hellosamblack/lidar-roomscanner/references/datasheets/NUCLEO-H563ZI/schematic/mb1404-bdp/readme.txt

******************************************************************************
* @file    readme.txt
* @author  MCD Application Team
* @version 1.1
* @date    04-August-2023  
* @brief   MB1404 board design files package
******************************************************************************
* COPYRIGHT(c) 2023 STMicroelectronics
*
* The Open Platform License Agreement (“Agreement”) is a binding legal contract
* between you ("You") and STMicroelectronics International N.V. (“ST”), a
* company incorporated under the laws of the Netherlands acting for the purpose
* of this Agreement through its Swiss branch 39, Chemin du Champ des Filles,
* 1228 Plan-les-Ouates, Geneva, Switzerland.
*
* By using the enclosed reference designs, schematics, PC board layouts, and
* documentation, in hardcopy or CAD tool file format (collectively, the
* “Reference Material”), You are agreeing to be bound by the terms and
* conditions of this Agreement. Do not use the Reference Material until You
* have read and agreed to this Agreement terms and conditions. The use of
* the Reference Material automatically implies the acceptance of the Agreement
* terms and conditions.
*
* The complete Open Platform License Agreement can be found on www.st.com/opla.
******************************************************************************

========================
* 1.0 - 22-February-2023
========================
    + First official release.
 
========================
* 1.1 - 04-August-2023
========================
    +  Schematics template updated + minor component changes (C59, C66, C69, C74, C79, C80, C81, C83, C84: YAGEO reference replaced by KEMET reference).

******************* (C) COPYRIGHT 2023 STMicroelectronics *****END OF FILE
