hellosamblack/lidar-roomscanner/references/datasheets/NUCLEO-IKS4A1/LSM6DSV16XTR/an5763-lsm6dsv16x-6axis-imu-with-embedded-sensor-fusion-ai-qvar-for-highend-applications-stmicroelectronics.md

# AN5763 Application Note Summary

* **Document ID**: AN5763 (Rev 4)
* **Title**: LSM6DSV16X: 6-axis IMU with embedded sensor fusion, AI, Qvar for high-end applications application note
* **PDF Files**: [an5763...pdf](file:///home/sam/git/personal/lidar-roomscanner/references/datasheets/NUCLEO-IKS4A1/LSM6DSV16XTR/an5763-lsm6dsv16x-6axis-imu-with-embedded-sensor-fusion-ai-qvar-for-highend-applications-stmicroelectronics.pdf) / [applicationNote.pdf](file:///home/sam/git/personal/lidar-roomscanner/references/datasheets/NUCLEO-IKS4A1/LSM6DSV16XTR/applicationNote.pdf) (See also `an.txt`)
* **Page Count**: 147 pages
* **Manufacturer**: STMicroelectronics

---

## Executive Summary
**AN5763** is the primary, comprehensive application note for the LSM6DSV16X 6-axis IMU. It details full operating modes, digital filtering pipelines (LPF1, LPF2, HPF), FIFO operation & compression, Embedded Sensor Fusion (SFI), interrupt routing, temperature compensation, Qvar sensing, and $\text{I}^2\text{C}$/SPI/$\text{I3C}$ serial interface protocol handling.

---

## Major Technical Topics & Chapters

### 1. Operating Modes & Power Management
* **Power Modes**: Low-power mode 1/2/3 and High-Performance mode.
* **Independent ODR Selection**: Accelerometer and Gyroscope can run at independent output data rates (1.875 Hz to 7.68 kHz).
* **Dual Channel Mode**: Allows splitting stream data for UI (User Interface) and EIS/OIS (Electronic / Optical Image Stabilization).

### 2. Digital Filtering & Processing Pipeline
```
[ Raw Sensor ] ---> [ LPF1 ] ---> [ LPF2 / HPF ] ---> [ FIFO / Output Registers ]
                                       |
                                       +---> [ Embedded Sensor Fusion (SFI) ]
```
* **Accelerometer Filters**: LPF1 cutoff frequency, LPF2 second-order low-pass filter, HPF high-pass filter for motion detection.
* **Gyroscope Filters**: LPF1 and HPF configuration for bias removal.

### 3. FIFO Buffer (4.5 KB) & Compression
* Modes: Bypass, FIFO mode, Continuous (Stream), Continuous-to-FIFO, Bypass-to-Continuous.
* Batching ODRs for Accel, Gyro, SFI, Temperature, FSM, MLC, and external sensors.
* **FIFO Compression**: Embedded lossless compression algorithm (2x or 3x compression factor) to maximize FIFO autonomy buffer time.

### 4. Embedded Sensor Fusion (SFLP)
* Computes the **game rotation vector** (attitude quaternion), gravity vector and gyroscope bias directly inside the LSM6DSV16X hardware core.
* **6-axis ONLY — accelerometer + gyroscope. There is no 9-axis / eCompass / geomagnetic mode on this part.**
  AN5763 §6.5: *"based on the accelerometer and gyroscope data processing"*. Datasheet §2.8 and p.1:
  *"a sensor fusion low-power (SFLP) algorithm able to provide a 6-axis (accelerometer + gyroscope) game
  rotation vector"*; the `SFLP_GAME_EN` bit is documented as *"sensor fusion algorithm for 6-axis
  accelerometer + gyroscope"*. "Game rotation vector" is Android's term for precisely the mag-free one.
* The **sensor hub (mode 2) is an I²C master**, not a fusion input: it attaches an external magnetometer or
  barometer so their data can reach the FIFO / FSM / MLC. It does **not** feed SFLP. Magnetometer fusion on
  this project is therefore host-side (`roomscan.sensors` `YawFusion`) by necessity, not by choice.
* Heading drift spec (datasheet Table 1): **0.5°/5 min** static, **0.7°/5 min** low-dynamic,
  **5.9°/5 min** high-dynamic. Pitch/roll 1.5°/0.5°/1.6° respectively.
* Outperformed host software fusion in power efficiency (~0.65 mA total IMU + fusion current).

> ⚠ **This file is a derived summary, not ST text.** An earlier revision of this section claimed SFLP
> *"Operates in 6-axis mode or 9-axis eCompass mode (Accel + Gyro + External Magnetometer via Sensor Hub /
> I3C)"* — that sentence appears **nowhere** in the source PDF and sent a 2026-07-30 session looking for an
> on-chip 9-axis mode that does not exist. Corrected against `pdftotext` output of the PDF beside it.
> **Verify any load-bearing claim in these `.md` summaries against the PDF before acting on it.**

### 5. Interrupt & Event Generation
* **Free-Fall Detection**: Triggers when acceleration along all 3 axes drops below configurable threshold.
* **Wake-Up & Activity/Inactivity**: Dynamic sleep-to-wake switching.
* **6D / 4D Orientation**: Detects portrait/landscape tilt position changes.
* **Single-Tap / Double-Tap**: Advanced tap gesture recognition.

---

## Recommended Initialization Code Sequence

```c
// 1. Soft Reset
write_reg(CTRL3, 0x01); // SW_RESET = 1
delay_ms(10);

// 2. Enable Block Data Update & Auto-Increment
write_reg(CTRL3, 0x44); // BDU = 1, IF_INC = 1

// 3. Configure Accelerometer: High-Performance Mode @ 120 Hz, FS = +/-4g
write_reg(CTRL1, 0x05 | (0x02 << 2)); // ODR_XL = 120 Hz, FS_XL = +/-4g

// 4. Configure Gyroscope: High-Performance Mode @ 120 Hz, FS = +/-2000 dps
write_reg(CTRL2, 0x05 | (0x03 << 2)); // ODR_G = 120 Hz, FS_G = +/-2000 dps

// 5. Enable Timestamp Counter
write_reg(CTRL10, 0x20); // TIMESTAMP_EN = 1
```

---

## LLM Routing Guide: When to Consult This File
Consult `AN5763` when:
* Implementing the complete hardware driver, FIFO reader, or interrupt handler for LSM6DSV16X.
* Configuring Embedded Sensor Fusion (SFI) vector outputs.
* Setting up FIFO batching and 2x/3x data compression.
* Tuning digital filters (LPF1, LPF2, HPF) for noise reduction or motion detection.
