hellosamblack/lidar-roomscanner/references/datasheets/NUCLEO-IKS4A1/LIS2MDL/dt0104-exploiting-the-magnetometer-as-a-virtual-gyroscope-at-low-and-ultrahigh-spin-rates-stmicroelectronics.md

# DT0104 Design Tip Summary

* **Document ID**: DT0104
* **Title**: Exploiting the magnetometer as a virtual gyroscope at low and ultra-high spin rates
* **Author**: Andrea Vitali
* **PDF File**: [dt0104...pdf](file:///home/sam/git/personal/lidar-roomscanner/references/datasheets/NUCLEO-IKS4A1/LIS2MDL/dt0104-exploiting-the-magnetometer-as-a-virtual-gyroscope-at-low-and-ultrahigh-spin-rates-stmicroelectronics.pdf)
* **Page Count**: 5 pages
* **Manufacturer**: STMicroelectronics

---

## Executive Summary
**DT0104** explains how to use a 3-axis magnetometer (e.g. LIS2MDL) as a **virtual gyroscope** to estimate angular velocity ($\omega$). This techniques allows measuring high spin rates beyond the dynamic full-scale range of physical gyroscopes (> 4000 dps) or saving power by disabling physical gyroscopes in low-rate monitoring applications.

---

## Technical Principle & Mathematical Derivation

### Principle
When a magnetometer rotates in a stable ambient magnetic field $\vec{B}_{earth}$, the magnetic vector measured in the sensor frame rotates at rate $\vec{\omega}$.
The time derivative of the magnetic field vector in the sensor body frame is:
$$\frac{d\vec{B}}{dt} = -\vec{\omega} \times \vec{B}$$

### Angular Rate Calculation
From the cross-product relation, the component of angular velocity perpendicular to the magnetic field vector is given by:
$$\vec{\omega}_{\perp} = \frac{\vec{B} \times \frac{d\vec{B}}{dt}}{\|\vec{B}\|^2}$$

### Spin Rate Estimation (Rotation Phase Derivative)
For 2D planar rotation around the Z axis:
$$\theta(t) = \arctan2(B_y(t), B_x(t))$$
$$\omega_z(t) = \frac{d\theta(t)}{dt} = \frac{B_x \cdot \frac{dB_y}{dt} - B_y \cdot \frac{dB_x}{dt}}{B_x^2 + B_y^2}$$

---

## Key Benefits & Operating Ranges

| Capability | Physical Gyroscope | Virtual Gyroscope (LIS2MDL) |
| :--- | :--- | :--- |
| **Max Rate Range** | $\pm 2000$ to $\pm 4000$ dps (saturation) | **> 10,000 dps** (limited only by sampling ODR & bandwidth) |
| **Power Consumption** | High (~0.5 - 1.2 mA) | **Ultralow (~50 - 200 $\mu\text{A}$)** |
| **Bias Drift** | Temperature / time gyro bias drift | **Zero long-term drift** (tied to Earth's magnetic field) |

---

## LLM Routing Guide: When to Consult This File
Consult `DT0104` when:
* Measuring extremely high spin rates (e.g., spinning lidar turrets, projectiles, drill heads, high-RPM motors).
* Reducing power consumption by replacing or augmenting physical gyroscopes with magnetometer angular rate tracking.
* Estimating rotational velocity when gyro sensors saturate or fail.
