hellosamblack/lidar-roomscanner/references/datasheets/NUCLEO-IKS4A1/LSM6DSV16XTR/an5882-lsm6dsv16x-finite-state-machine-stmicroelectronics.md

# AN5882 Application Note Summary

* **Document ID**: AN5882 (Rev 3)
* **Title**: LSM6DSV16X: finite state machine application note
* **PDF File**: [an5882...pdf](file:///home/sam/git/personal/lidar-roomscanner/references/datasheets/NUCLEO-IKS4A1/LSM6DSV16XTR/an5882-lsm6dsv16x-finite-state-machine-stmicroelectronics.md)
* **Page Count**: 68 pages
* **Manufacturer**: STMicroelectronics

---

## Executive Summary
**AN5882** describes the programming, architecture, and instruction set of the **Finite State Machines (FSM)** integrated into the LSM6DSV16X. Up to **8 independent state machines** can be programmed to detect specific gesture sequences, motion patterns, or orientation changes directly in hardware.

---

## FSM Architecture & Instruction Set

```
[ Motion Sensor Stream ] ---> [ Signal Conditioning ] ---> [ FSM Program Memory ] ---> [ FSM Interrupt / Status ]
                                (Filters & Selection)      (Commands: CHK, JMP...)
```

### 1. Key Components
* **Signal Conditioning Block**: Applies high-pass / low-pass filtering, magnitude calculation ($\sqrt{X^2+Y^2+Z^2}$), vector inner products, and thresholds.
* **FSM Block**: 8 independent execution engines reading FSM program memory.
* **Long Counter**: 16-bit timing counter shared between state machines to evaluate duration constraints.

### 2. Main FSM Commands / Opcodes
* `NOP`: No operation.
* `CHK`: Check condition (evaluates threshold, axis sign, or time counter).
* `JMP`: Jump to instruction address if condition evaluates true.
* `SET`: Set flag or output state.
* `RESET`: Reset timer counter or state.
* `OUT`: Generate FSM interrupt signal and output state code to status register.

---

## Programming & Memory Loading
1. Create state machine definition using ST FSM Tool / MEMS Studio.
2. Generate FSM byte code program.
3. Write FSM configuration bytes into LSM6DSV16X Embedded Advanced Features pages (`EMB_FUNC_EN_A`, `FSM_ENABLE`).

---

## LLM Routing Guide: When to Consult This File
Consult `AN5882` when:
* Developing custom hardware-accelerated motion gesture algorithms (e.g., glance, wrist tilt, shake, rotation detection).
* Writing software drivers to load FSM binary code into LSM6DSV16X memory.
* Handling FSM interrupt status flags (`FSM_STATUS_A / B`).
