hellosamblack/lidar-roomscanner/references/datasheets/NUCLEO-IKS4A1/LSM6DSV16XTR/dt0060-exploiting-the-gyroscope-to-update-tilt-measurement-and-ecompass-stmicroelectronics.md

# DT0060 Design Tip Summary

* **Document ID**: DT0060
* **Title**: Exploiting the gyroscope to update tilt measurement and eCompass
* **Author**: Andrea Vitali
* **PDF File**: [dt0060...pdf](file:///home/sam/git/personal/lidar-roomscanner/references/datasheets/NUCLEO-IKS4A1/LSM6DSV16XTR/dt0060-exploiting-the-gyroscope-to-update-tilt-measurement-and-ecompass-stmicroelectronics.pdf)
* **Page Count**: 7 pages
* **Manufacturer**: STMicroelectronics

---

## Executive Summary
**DT0060** details how to integrate gyroscope angular rate measurements ($\omega_x, \omega_y, \omega_z$) into tilt and eCompass estimation loops to prevent external dynamic accelerations (such as linear motion, vehicle turning, or vibrations) from corrupting tilt and heading measurements.

---

## Dynamic Fusion Principle & Complementary Filtering

### Problem Statement
Accelerometer-only tilt computation (DT0058) assumes that the measured vector is pure Earth gravity ($1g$). Under linear acceleration (e.g. robot accelerating forward), accelerometer measurements combine gravity and linear acceleration ($A = g + a_{linear}$), creating severe tilt calculation errors.

### Gyroscope Integration Solution
1. **Short-Term High Frequency Update**: Integrate gyroscope angular velocity ($\vec{\omega}$) to update orientation quaternions or DCM (Direction Cosine Matrix) smoothly over time $\Delta t$.
2. **Long-Term Drift Correction**: Apply complementary filter or Kalman filter gain to fuse accelerometer gravity vector and magnetometer heading at low rates:
$$\vec{q}_{k} = \vec{q}_{k-1} \otimes \Delta\vec{q}_{gyro} + \alpha \cdot (\vec{q}_{accel/mag} - \vec{q}_{k-1})$$

---

## LLM Routing Guide: When to Consult This File
Consult `DT0060` when:
* Implementing 6-axis / 9-axis complementary filters or Extended Kalman Filters (EKF).
* Resolving orientation jitter or tilt errors caused by mechanical vibration or robot movement.
