hellosamblack/lidar-roomscanner/calibration/flatfield/2026-08-04/analysis_20260804_metrics.csv

file | raw_frames | depth_accuracy_global_error_mm | depth_plane_rms_mm | depth_zone_std_median_mm | depth_zone_std_p95_mm | depth_valid_pct | refl_fpn_pct | refl_holdout_after_pct | refl_temporal_cv_pct | deproj_xy_p95_mm | deproj_xy_edge_p95_mm
4msExpPrecision55inchFlatField.bin | 1271 | -4.109130859375 | 2.0163314069502403 | 0.7660982689572351 | 0.8609254001545432 | 100.0 | 6.596441922477059 | 1.4478581717208816 | 0.6963480464052492 | 31.431350536653053 | 43.82652857957803
8msExpPrecision55inchFlatField.bin | 1173 | -4.242919921875 | 2.0286684740914684 | 0.5268087677416203 | 0.601913518048294 | 100.0 | 6.679974894812315 | 1.4549387802397868 | 0.43813580350810893 | 31.420344466770047 | 43.81545564114227
8msExpPrecision60hzEnv55inchFlatField.bin | 1196 | -4.02734375 | 2.0329517637275347 | 0.5115222347405917 | 0.5867092585629184 | 100.0 | 6.662128279519313 | 1.4468677948119013 | 0.4390378373825098 | 31.420387760098127 | 43.81260219086063
Reg16msExpAmbient55inchFlatField.bin | 1227 | -7.1934814453125 | 2.5540982429090264 | 0.43187292052123105 | 0.5053695860848644 | 100.0 | 3.7271666114927395 | 1.7651792741803083 | 0.13134724100037556 | 31.3895410448603 | 43.94168717777747
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
