hellosamblack/lidar-roomscanner/calibration/flatfield/2026-08-04/analysis_20260804_flatfield_maps.png

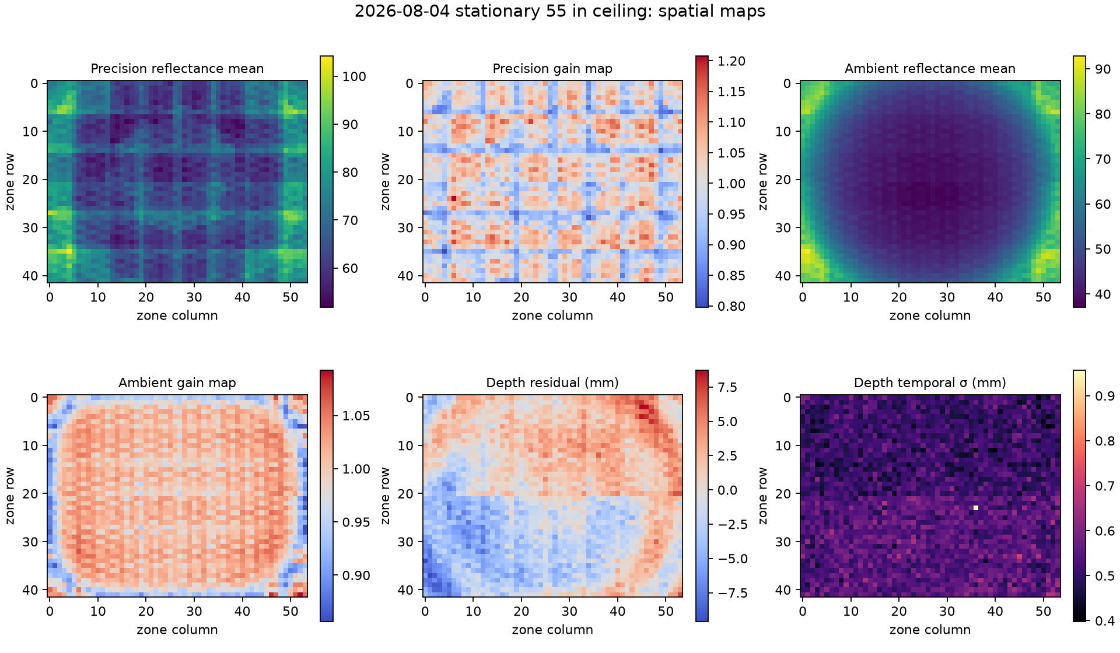
calibration/flatfield/2026-08-04/analysis_20260804_flatfield_maps.png
