hellosamblack/lidar-roomscanner/calibration/flatfield/2026-08-04/ffpan_20260804_ambientRegular8msFFpan.png

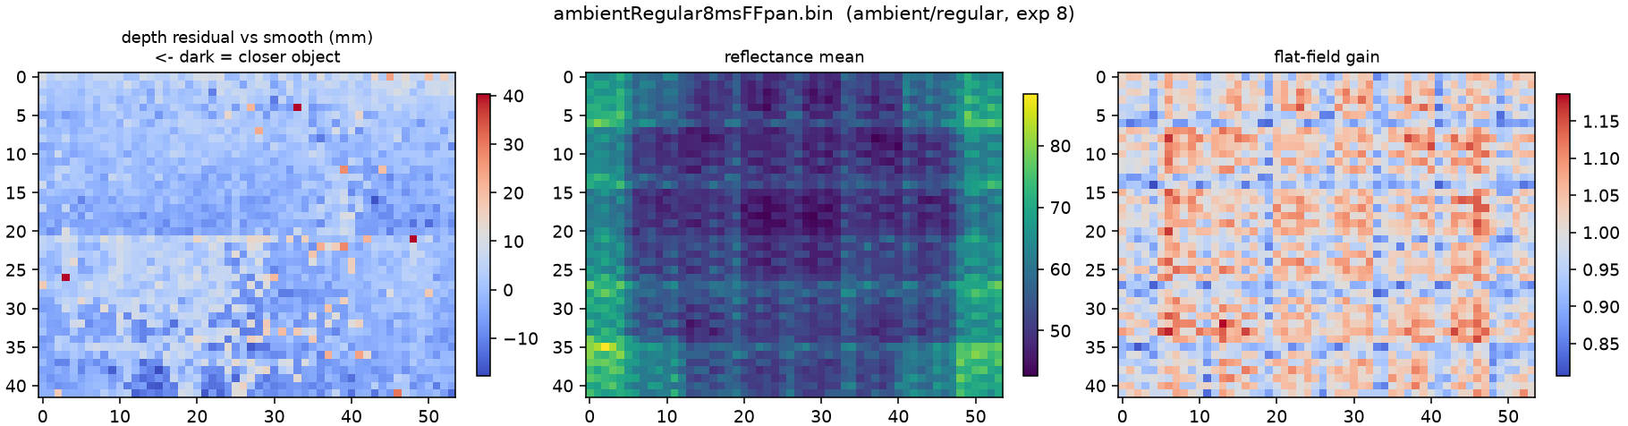
calibration/flatfield/2026-08-04/ffpan_20260804_ambientRegular8msFFpan.png
