hellosamblack/lidar-roomscanner/references/kicad/roomscanner-stack/roomscanner-stack.kicad_sch

## KiCad design references/kicad/roomscanner-stack/roomscanner-stack.kicad_sch (2026-07-10)

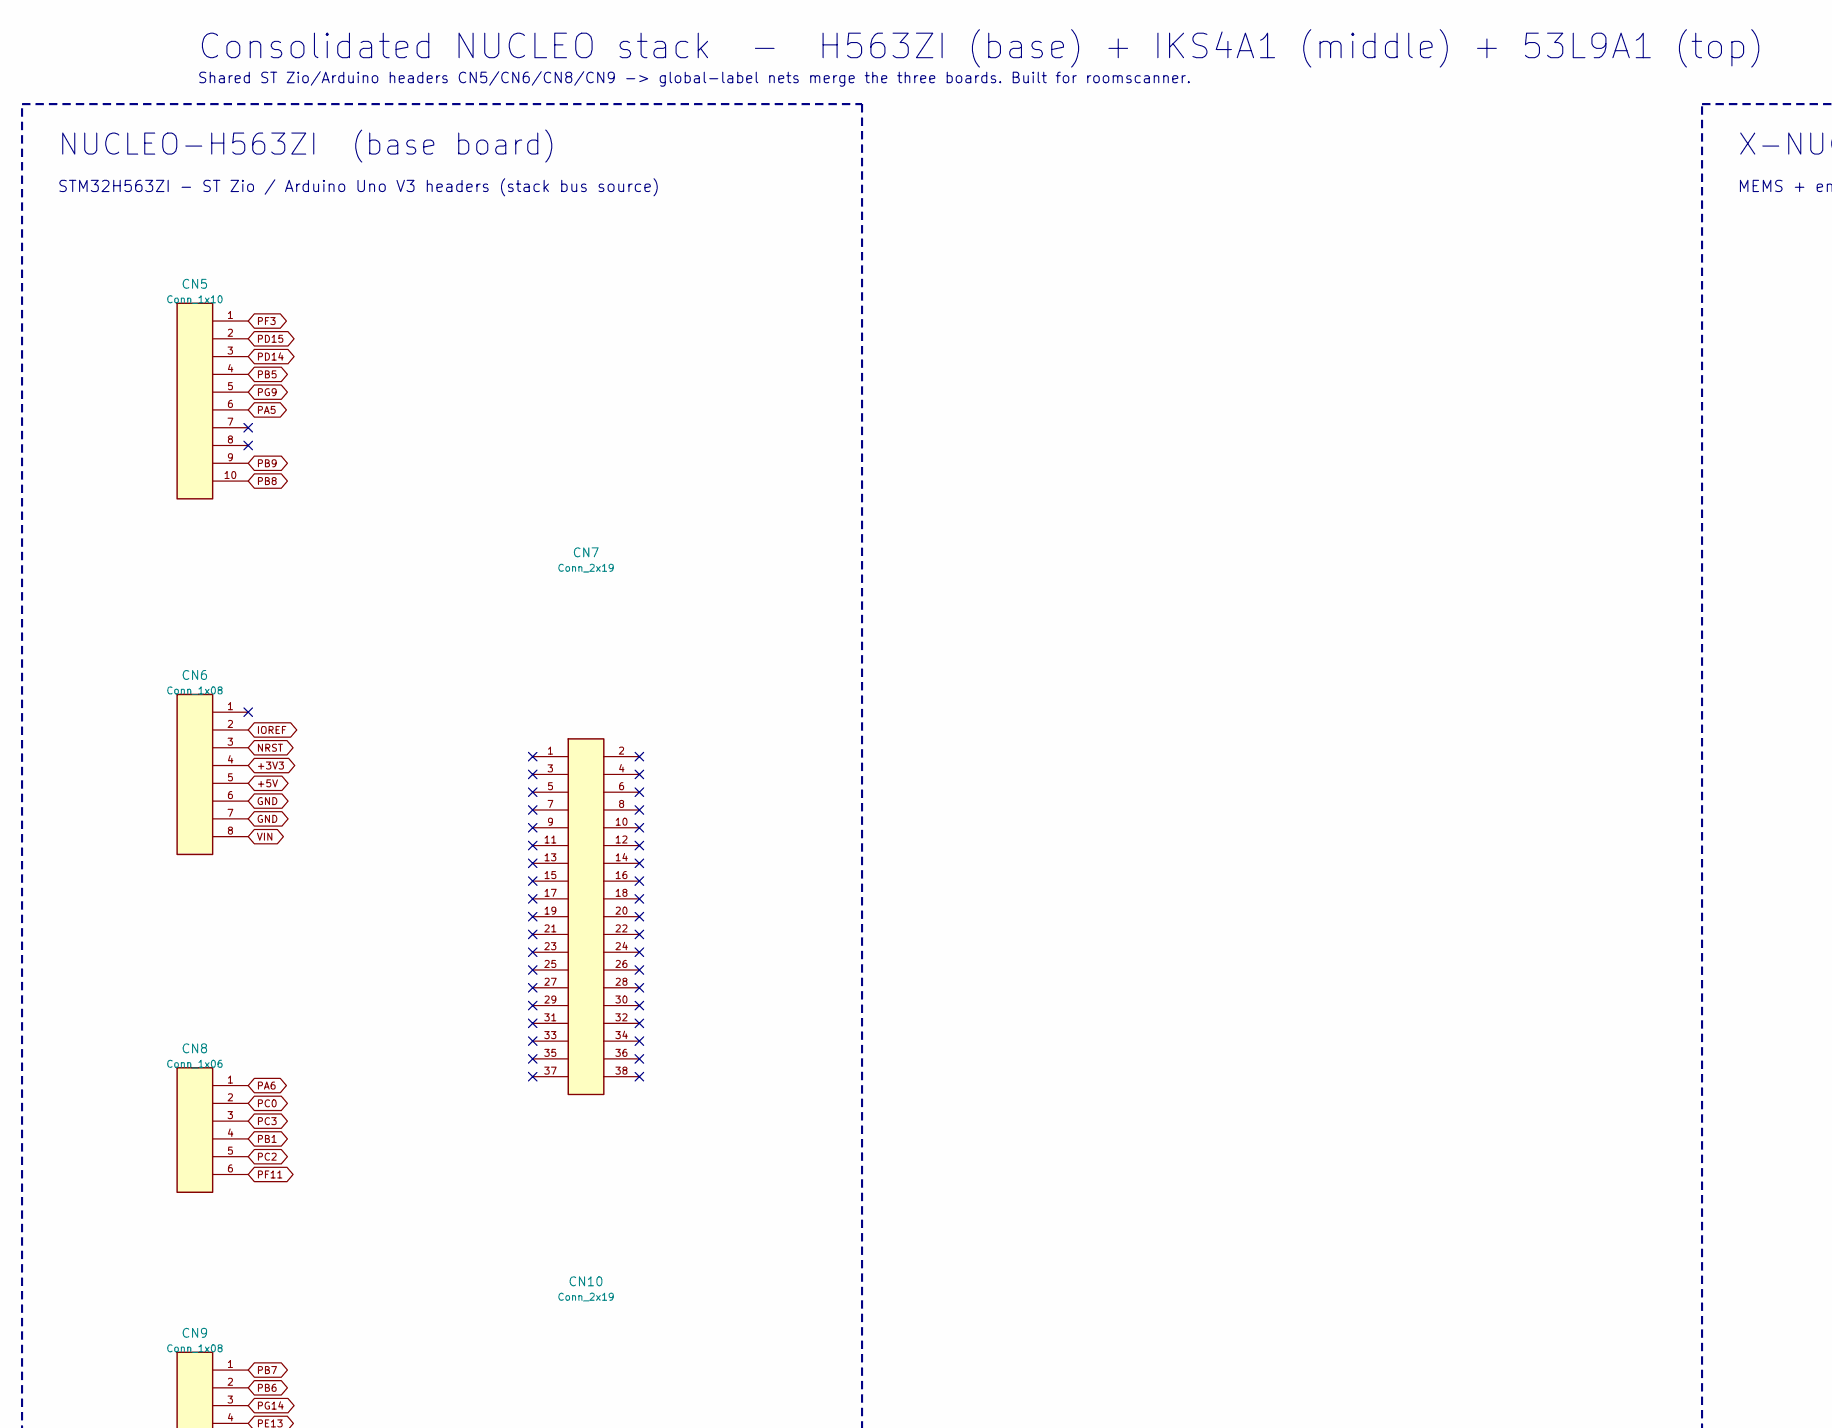
[picture p10: schematic roomscanner-stack.kicad_sch, part in row 1, column 1]

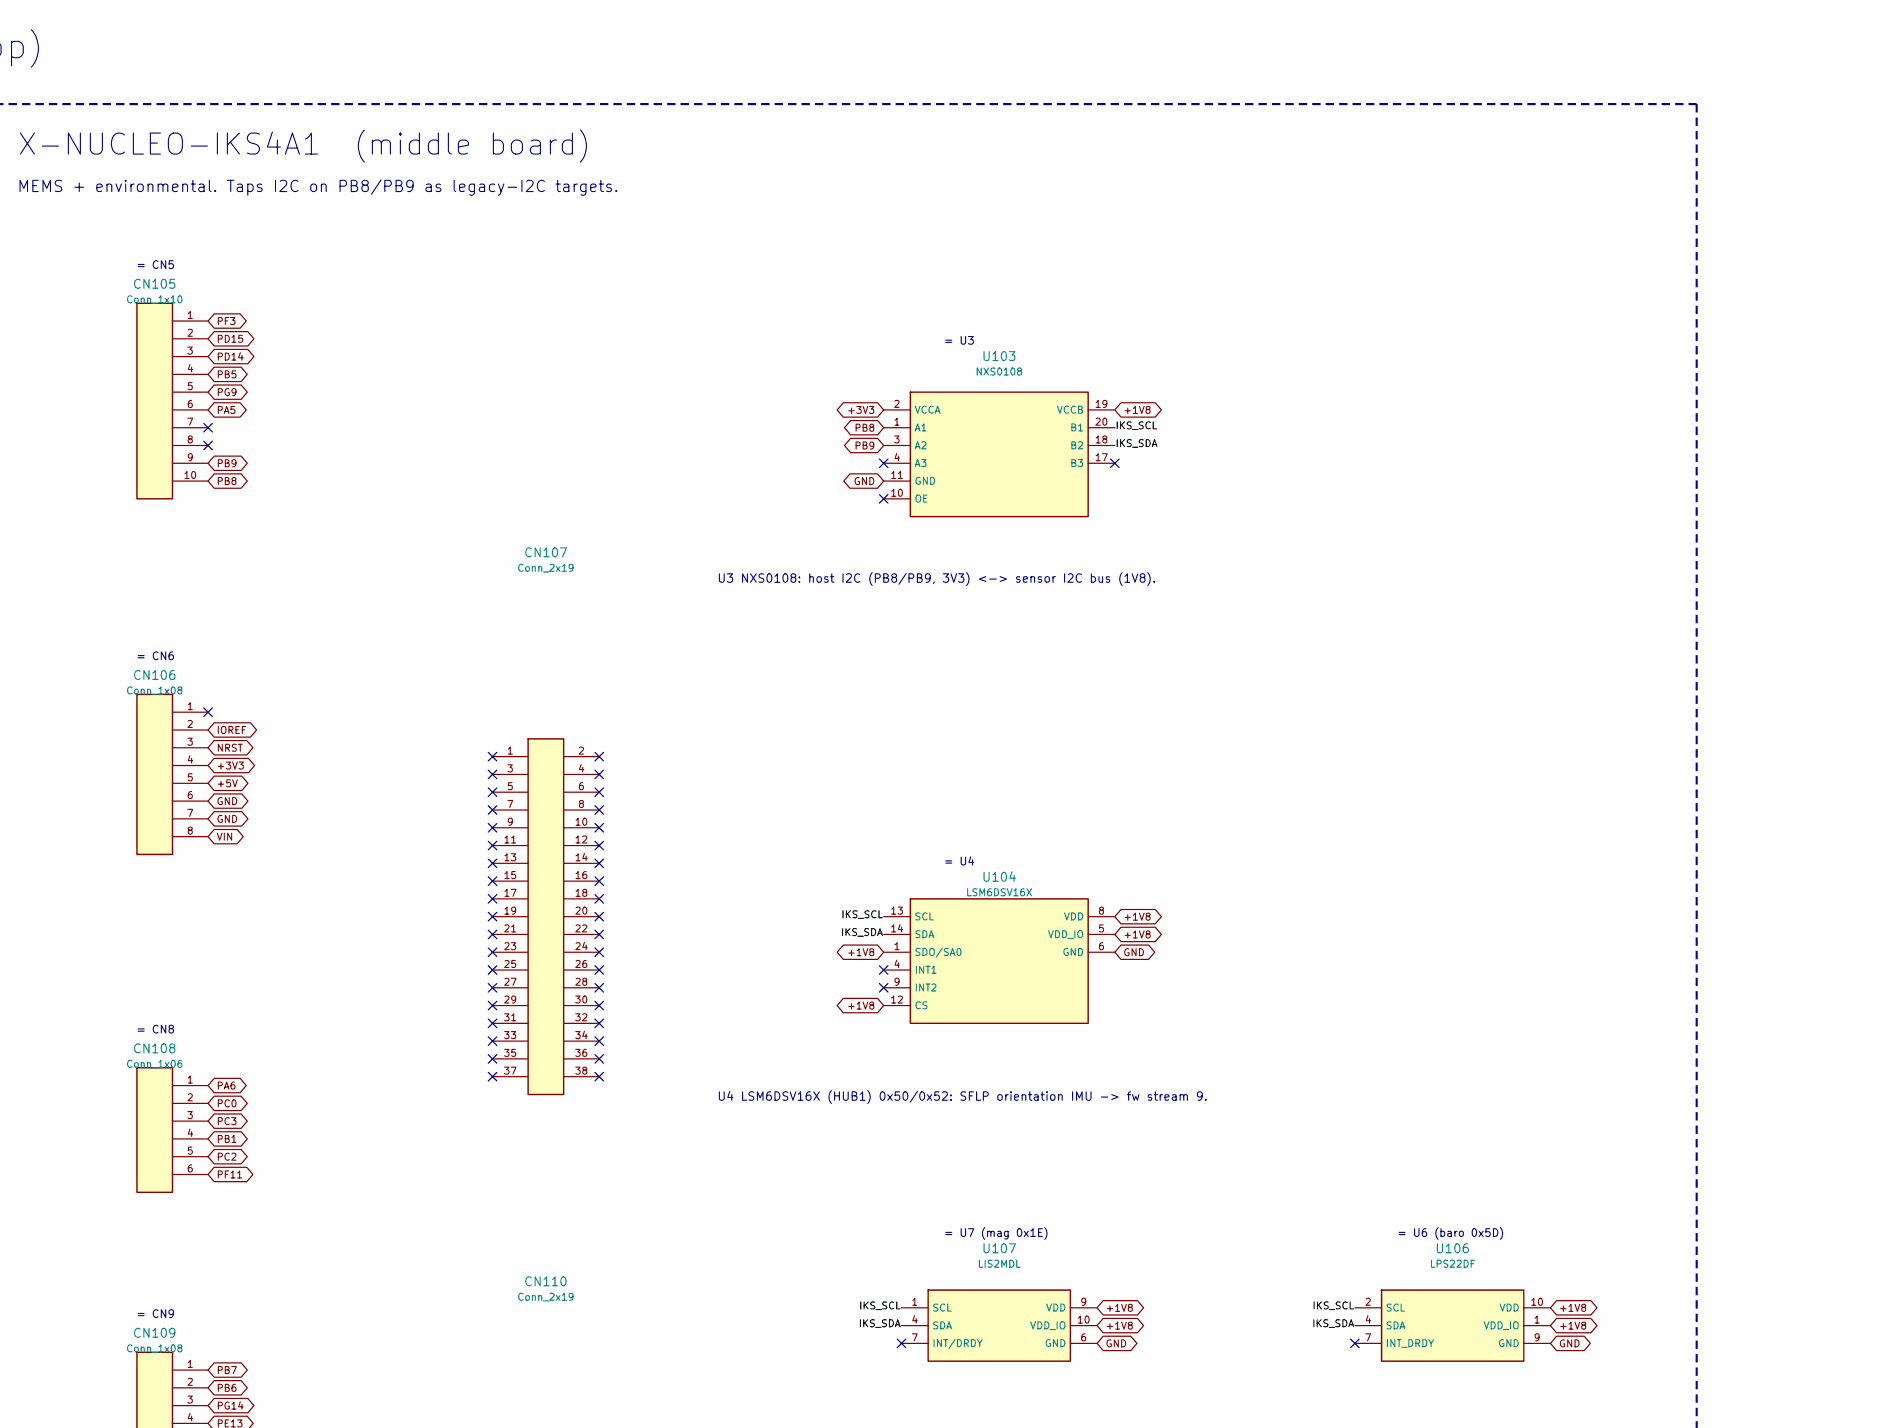
[picture p11: schematic roomscanner-stack.kicad_sch, part in row 1, column 2]

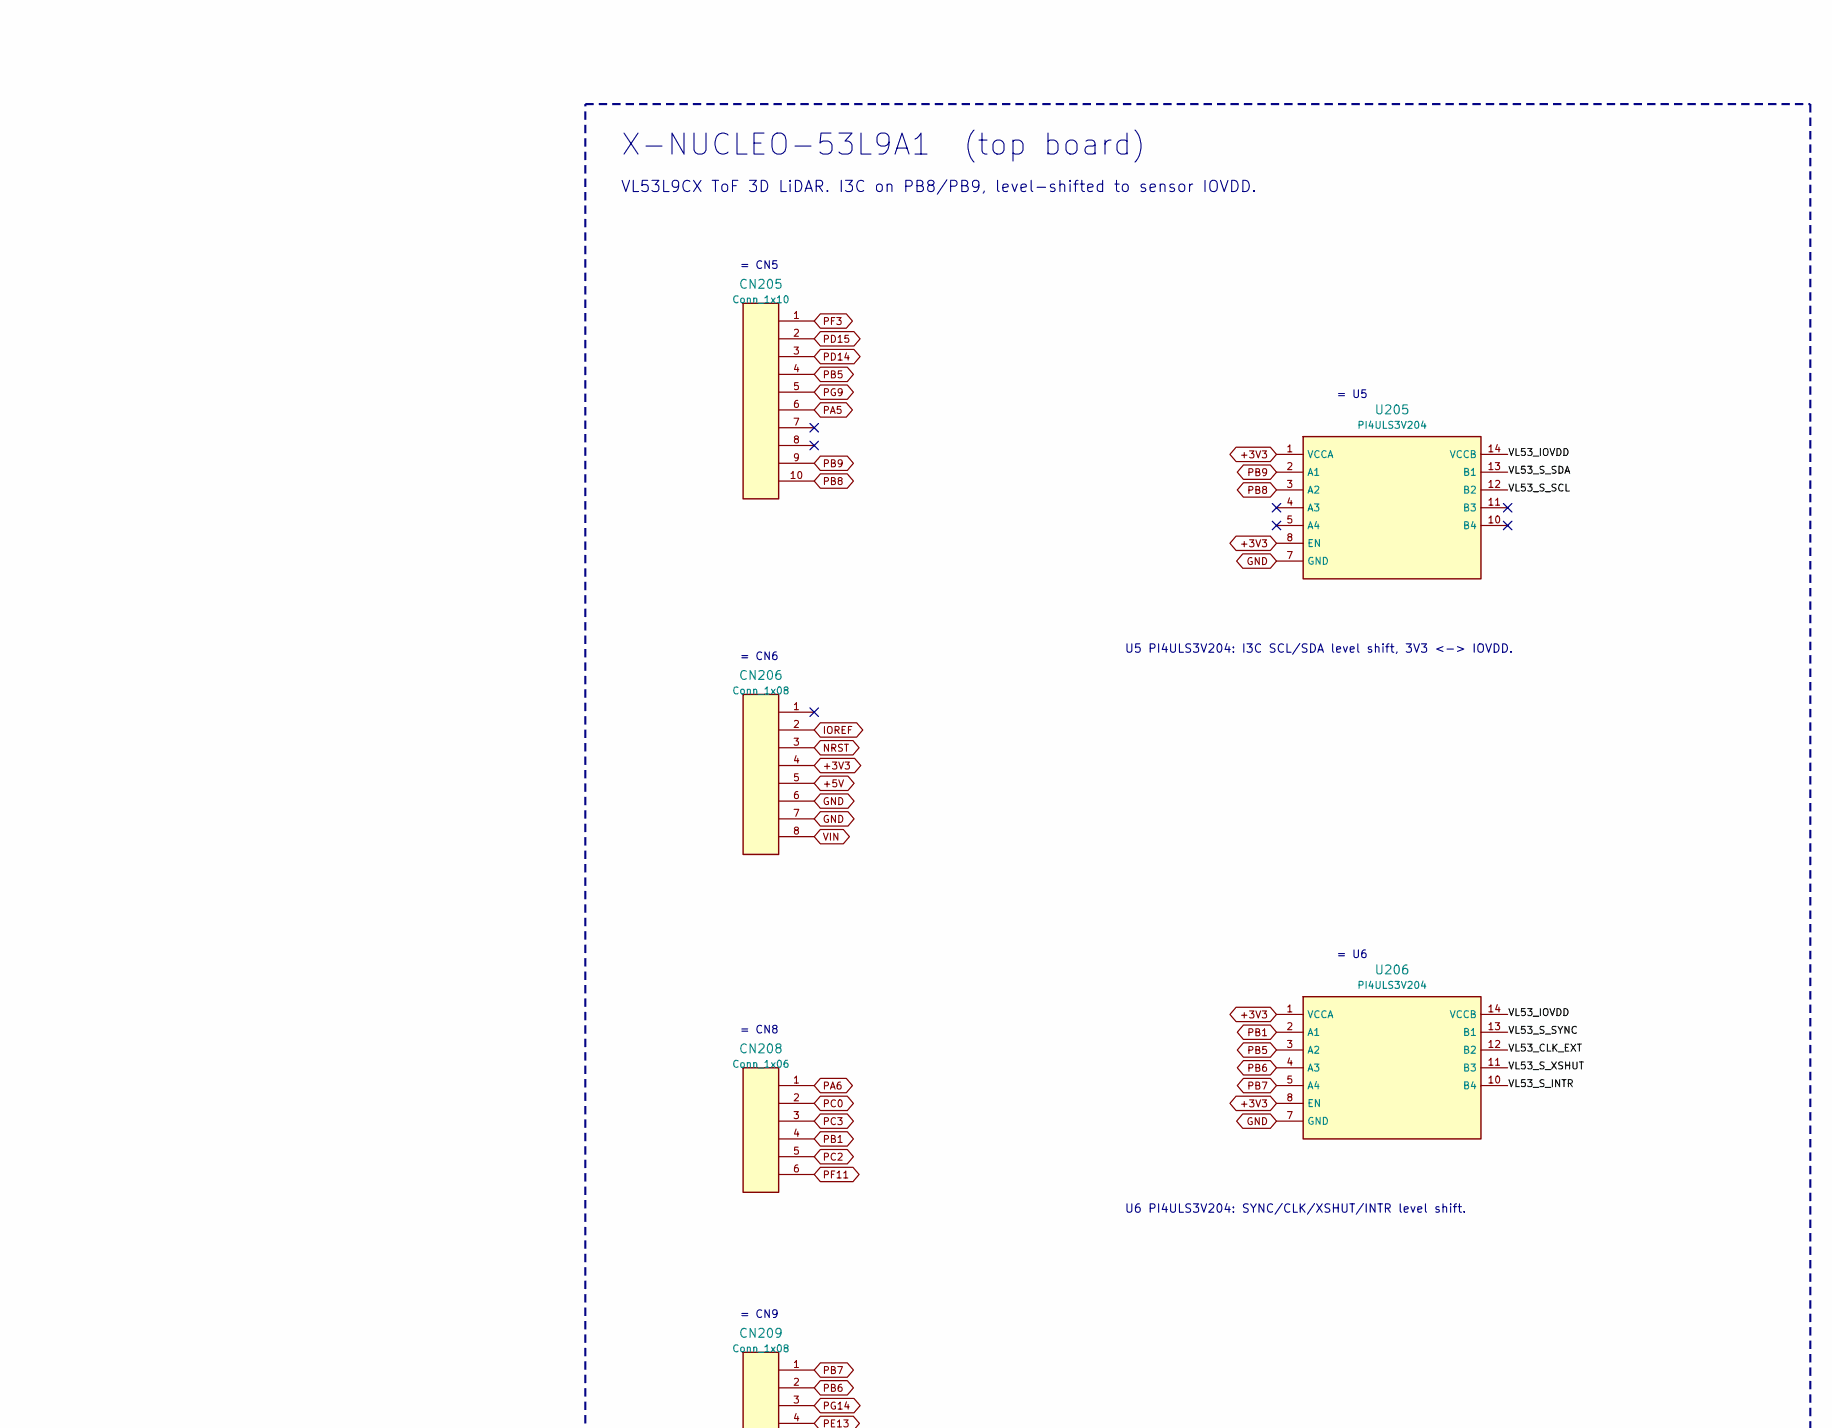
[picture p12: schematic roomscanner-stack.kicad_sch, part in row 1, column 3]

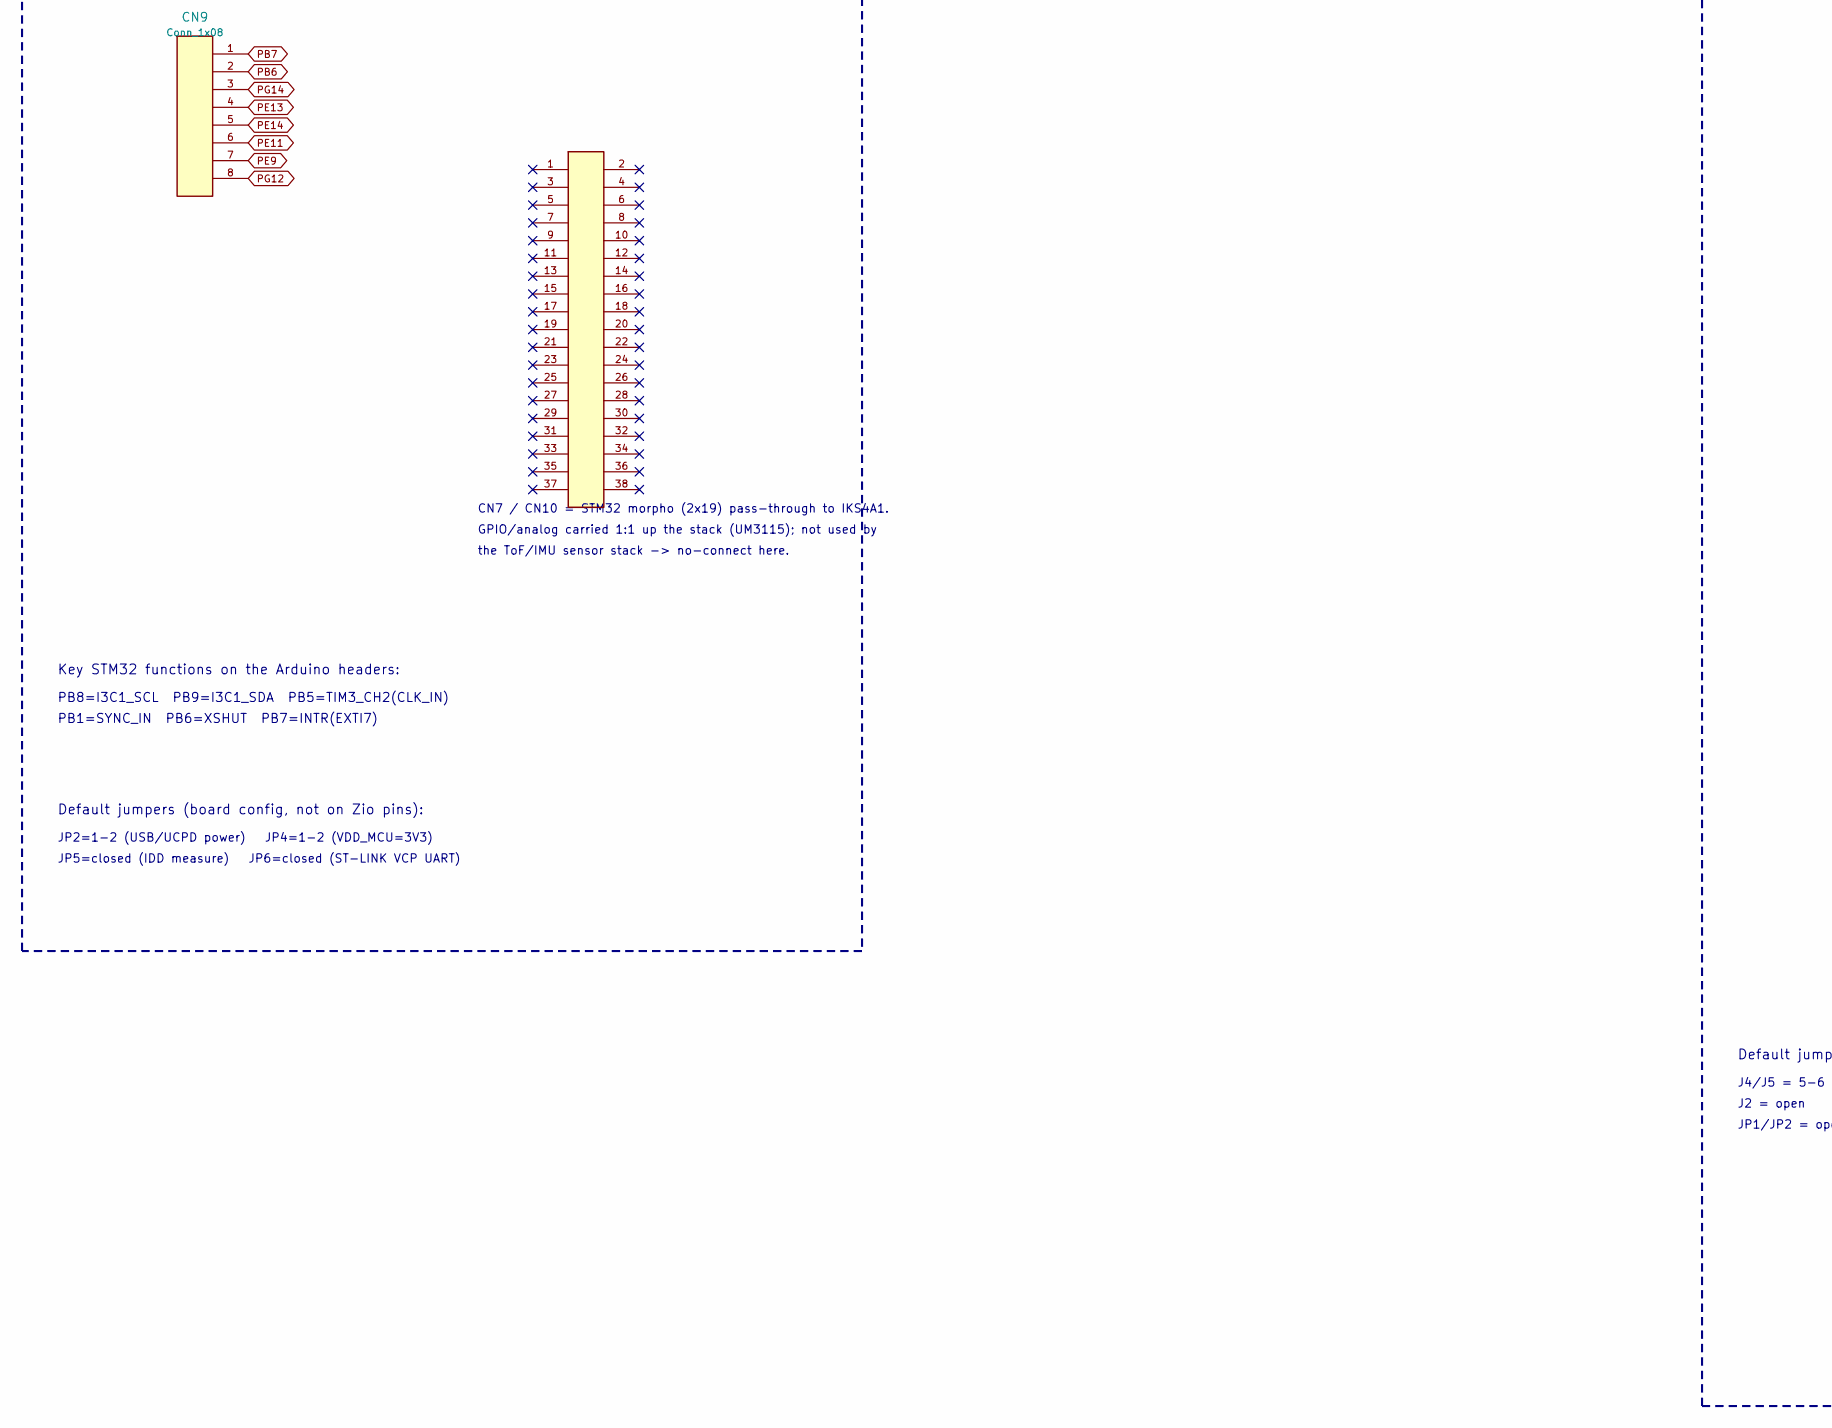
[picture p13: schematic roomscanner-stack.kicad_sch, part in row 2, column 1]

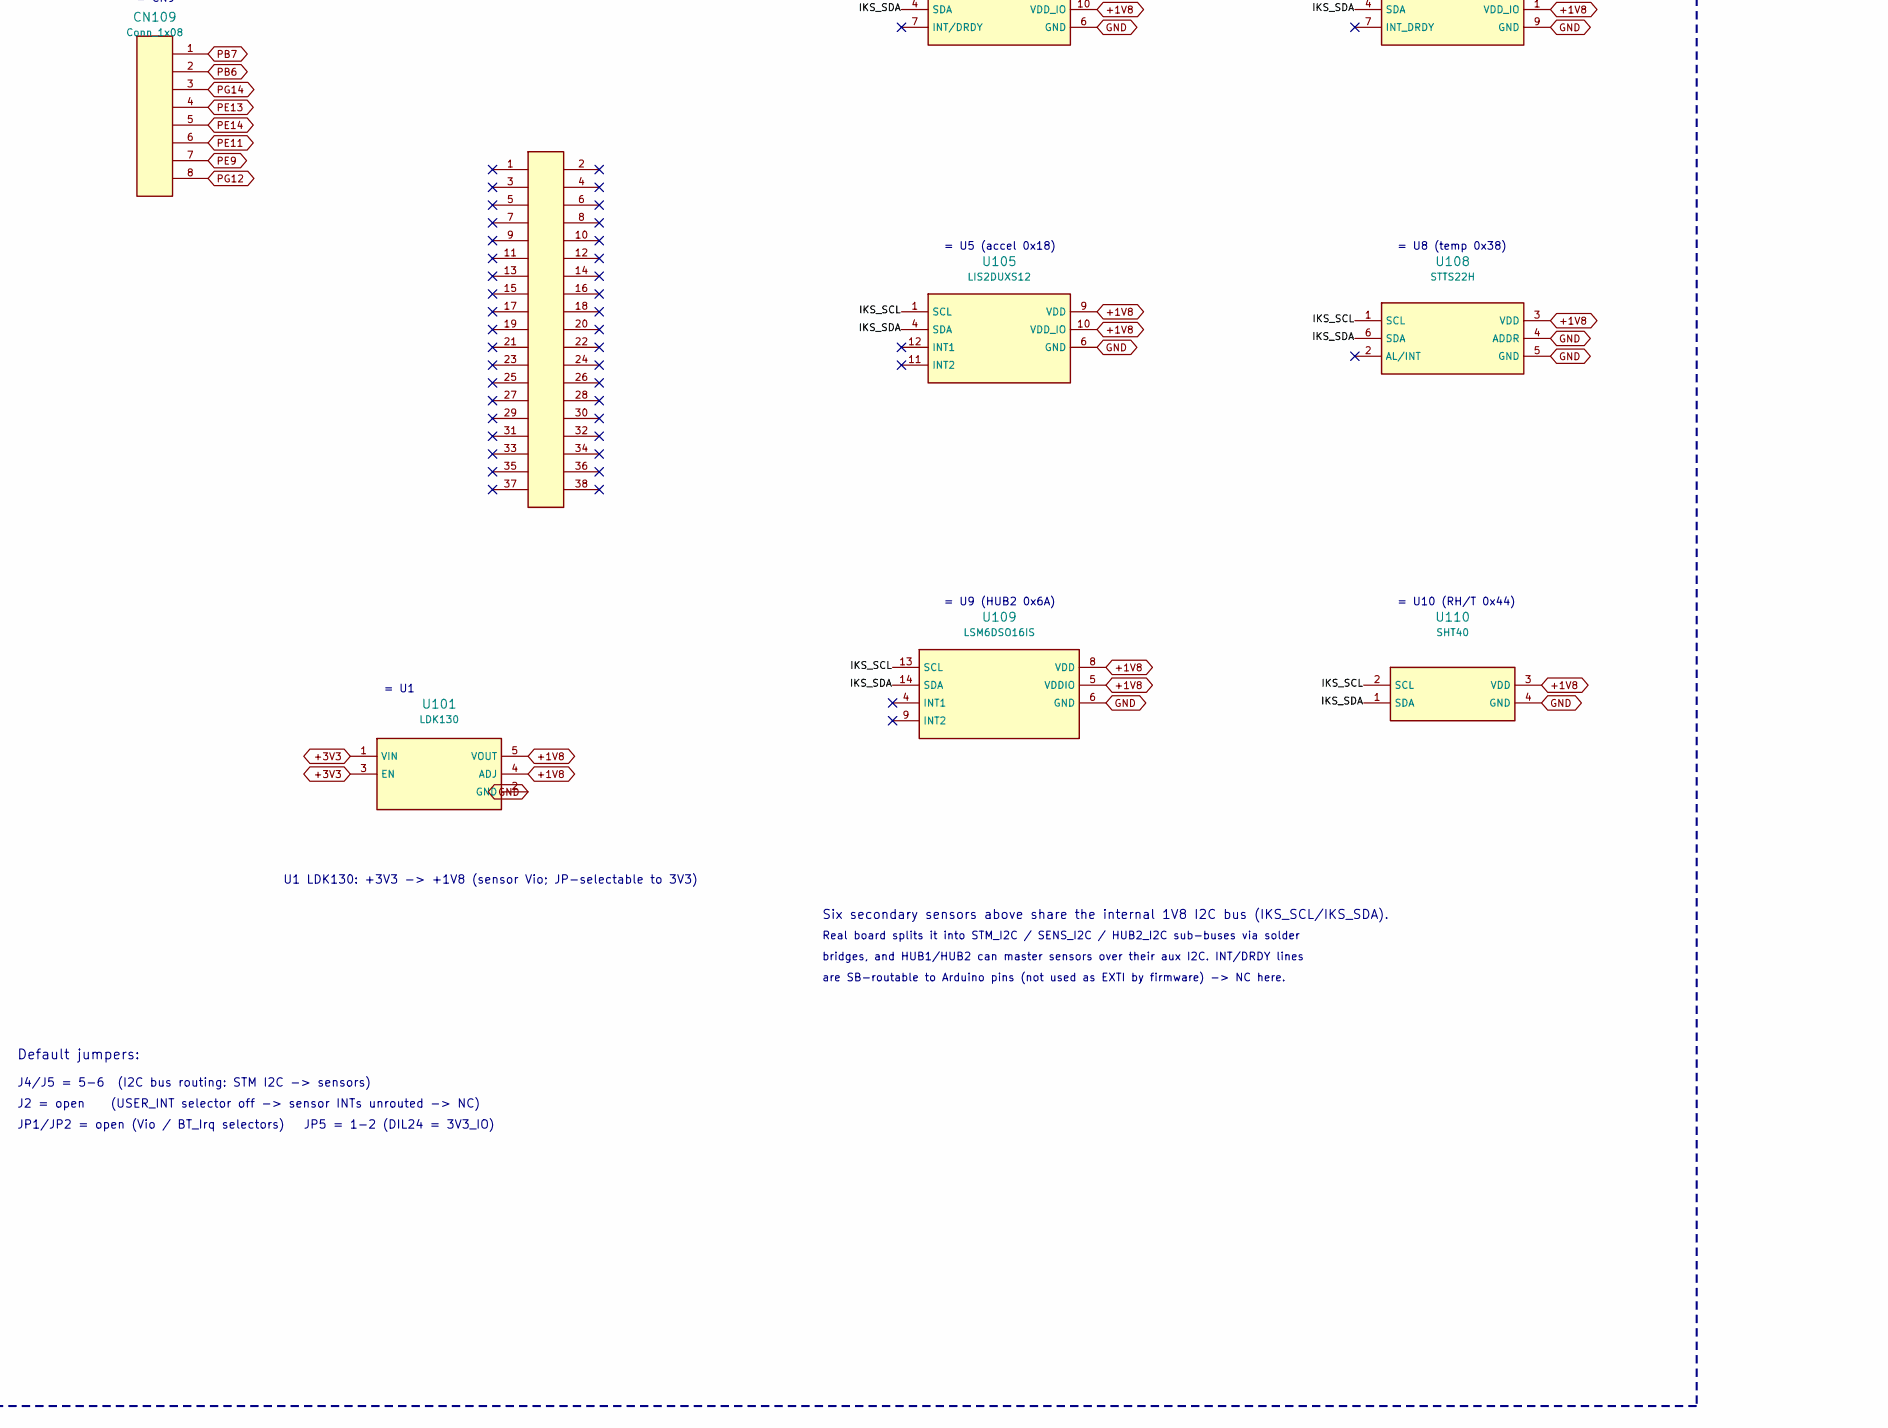
[picture p14: schematic roomscanner-stack.kicad_sch, part in row 2, column 2]

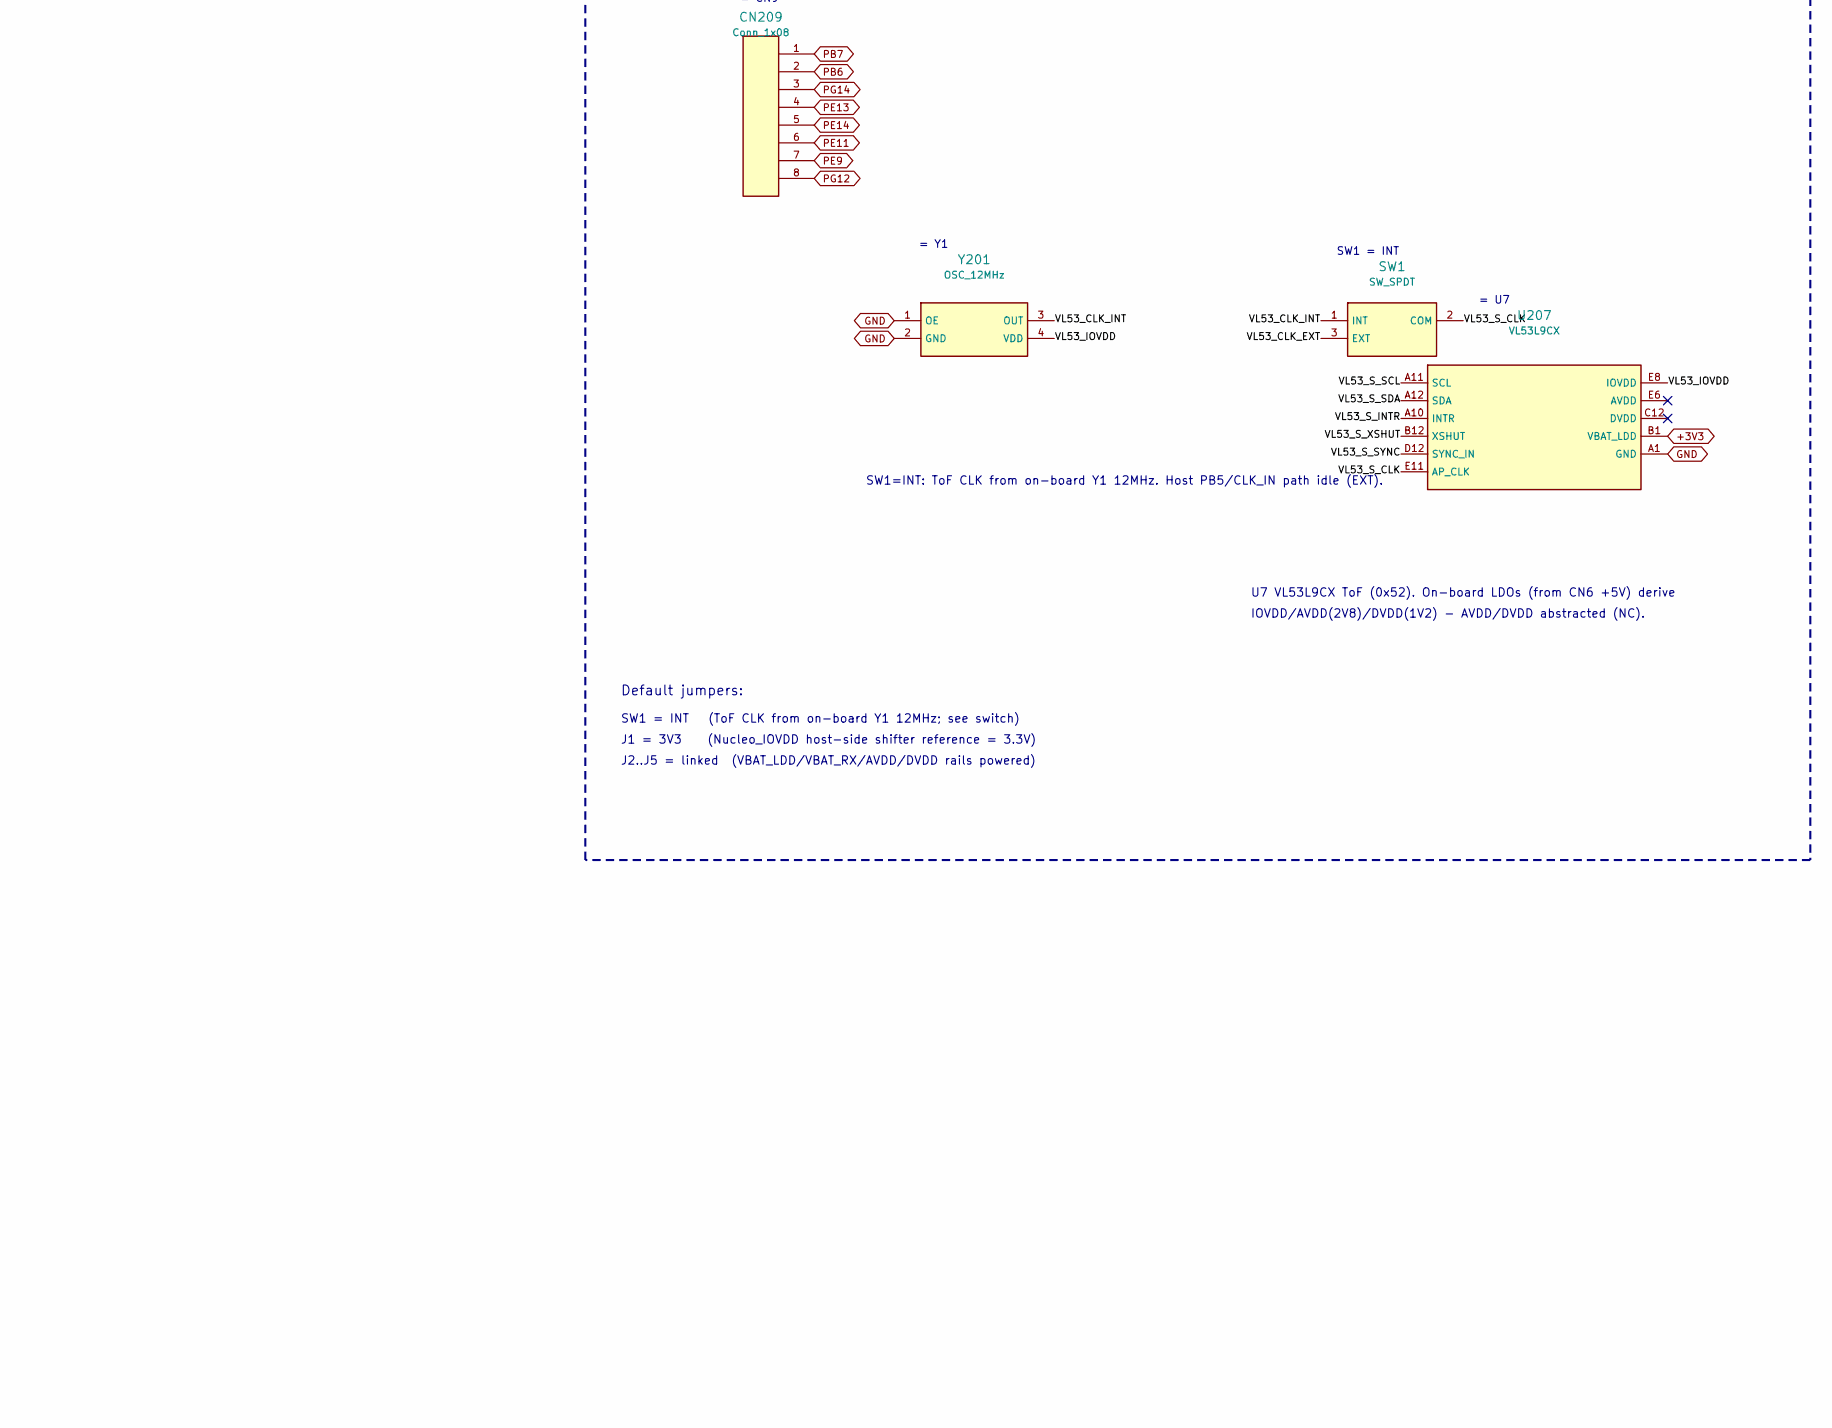
[picture p15: schematic roomscanner-stack.kicad_sch, part in row 2, column 3]

Parts:
CN5, CN105, CN205: Conn_1x10
CN6, CN9, CN106, CN109, CN206, CN209: Conn_1x08
CN7, CN10, CN107, CN110: Conn_2x19
CN8, CN108, CN208: Conn_1x06
SW1: SW_SPDT
U101: LDK130
U103: NXS0108
U104: LSM6DSV16X
U105: LIS2DUXS12
U106: LPS22DF
U107: LIS2MDL
U108: STTS22H
U109: LSM6DSO16IS
U110: SHT40
U205, U206: PI4ULS3V204
U207: VL53L9CX
Y201: OSC_12MHz

Connections:
+1V8: U101.4 (ADJ), U101.5 (VOUT), U103.19 (VCCB), U104.1 (SDO/SA0), U104.5 (VDD_IO), U104.8 (VDD), U104.12 (CS), U105.9 (VDD), U105.10 (VDD_IO), U106.1 (VDD_IO), U106.10 (VDD), U107.9 (VDD), U107.10 (VDD_IO), U108.3 (VDD), U109.5 (VDDIO), U109.8 (VDD), U110.3 (VDD)
+3V3: CN6.4, CN106.4, CN206.4, U101.1 (VIN), U101.3 (EN), U103.2 (VCCA), U205.1 (VCCA), U205.8 (EN), U206.1 (VCCA), U206.8 (EN), U207.B1 (VBAT_LDD)
+5V: CN6.5, CN106.5, CN206.5
GND: CN6.6, CN6.7, CN106.6, CN106.7, CN206.6, CN206.7, U101.2 (GND), U103.11 (GND), U104.6 (GND), U105.6 (GND), U106.9 (GND), U107.6 (GND), U108.4 (ADDR), U108.5 (GND), U109.6 (GND), U110.4 (GND), U205.7 (GND), U206.7 (GND), U207.A1 (GND), Y201.1 (OE), Y201.2 (GND)
IKS_SCL: U103.20 (B1), U104.13 (SCL), U105.1 (SCL), U106.2 (SCL), U107.1 (SCL), U108.1 (SCL), U109.13 (SCL), U110.2 (SCL)
IKS_SDA: U103.18 (B2), U104.14 (SDA), U105.4 (SDA), U106.4 (SDA), U107.4 (SDA), U108.6 (SDA), U109.14 (SDA), U110.1 (SDA)
IOREF: CN6.2, CN106.2, CN206.2
NRST: CN6.3, CN106.3, CN206.3
PA5: CN5.6, CN105.6, CN205.6
PA6: CN8.1, CN108.1, CN208.1
PB1: CN8.4, CN108.4, CN208.4, U206.2 (A1)
PB5: CN5.4, CN105.4, CN205.4, U206.3 (A2)
PB6: CN9.2, CN109.2, CN209.2, U206.4 (A3)
PB7: CN9.1, CN109.1, CN209.1, U206.5 (A4)
PB8: CN5.10, CN105.10, CN205.10, U103.1 (A1), U205.3 (A2)
PB9: CN5.9, CN105.9, CN205.9, U103.3 (A2), U205.2 (A1)
PC0: CN8.2, CN108.2, CN208.2
PC2: CN8.5, CN108.5, CN208.5
PC3: CN8.3, CN108.3, CN208.3
PD14: CN5.3, CN105.3, CN205.3
PD15: CN5.2, CN105.2, CN205.2
PE9: CN9.7, CN109.7, CN209.7
PE11: CN9.6, CN109.6, CN209.6
PE13: CN9.4, CN109.4, CN209.4
PE14: CN9.5, CN109.5, CN209.5
PF3: CN5.1, CN105.1, CN205.1
PF11: CN8.6, CN108.6, CN208.6
PG9: CN5.5, CN105.5, CN205.5
PG12: CN9.8, CN109.8, CN209.8
PG14: CN9.3, CN109.3, CN209.3
VIN: CN6.8, CN106.8, CN206.8
VL53_CLK_EXT: SW1.3 (EXT), U206.12 (B2)
VL53_CLK_INT: SW1.1 (INT), Y201.3 (OUT)
VL53_IOVDD: U205.14 (VCCB), U206.14 (VCCB), U207.E8 (IOVDD), Y201.4 (VDD)
VL53_S_CLK: SW1.2 (COM), U207.E11 (AP_CLK)
VL53_S_INTR: U206.10 (B4), U207.A10 (INTR)
VL53_S_SCL: U205.12 (B2), U207.A11 (SCL)
VL53_S_SDA: U205.13 (B1), U207.A12 (SDA)
VL53_S_SYNC: U206.13 (B1), U207.D12 (SYNC_IN)
VL53_S_XSHUT: U206.11 (B3), U207.B12 (XSHUT)

Notes on the sheet:
Consolidated NUCLEO stack - H563ZI (base) + IKS4A1 (middle) + 53L9A1 (top)
Shared ST Zio/Arduino headers CN5/CN6/CN8/CN9 -> global-label nets merge the three boards. Built for roomscanner.
NUCLEO-H563ZI (base board)
STM32H563ZI - ST Zio / Arduino Uno V3 headers (stack bus source)
CN7 / CN10 = STM32 morpho (2x19) pass-through to IKS4A1.
GPIO/analog carried 1:1 up the stack (UM3115); not used by
the ToF/IMU sensor stack -> no-connect here.
Key STM32 functions on the Arduino headers:
PB8=I3C1_SCL PB9=I3C1_SDA PB5=TIM3_CH2(CLK_IN)
PB1=SYNC_IN PB6=XSHUT PB7=INTR(EXTI7)
Default jumpers (board config, not on Zio pins):
JP2=1-2 (USB/UCPD power) JP4=1-2 (VDD_MCU=3V3)
JP5=closed (IDD measure) JP6=closed (ST-LINK VCP UART)
X-NUCLEO-IKS4A1 (middle board)
MEMS + environmental. Taps I2C on PB8/PB9 as legacy-I2C targets.
= CN5
= CN6
= CN8
= CN9
= U1
U1 LDK130: +3V3 -> +1V8 (sensor Vio; JP-selectable to 3V3)
= U3
U3 NXS0108: host I2C (PB8/PB9, 3V3) <-> sensor I2C bus (1V8).
= U4
U4 LSM6DSV16X (HUB1) 0x50/0x52: SFLP orientation IMU -> fw stream 9.
= U7 (mag 0x1E)
= U6 (baro 0x5D)
= U5 (accel 0x18)
= U8 (temp 0x38)
= U9 (HUB2 0x6A)
= U10 (RH/T 0x44)
Six secondary sensors above share the internal 1V8 I2C bus (IKS_SCL/IKS_SDA).
Real board splits it into STM_I2C / SENS_I2C / HUB2_I2C sub-buses via solder
bridges, and HUB1/HUB2 can master sensors over their aux I2C. INT/DRDY lines
are SB-routable to Arduino pins (not used as EXTI by firmware) -> NC here.
Default jumpers:
J4/J5 = 5-6 (I2C bus routing: STM I2C -> sensors)
J2 = open (USER_INT selector off -> sensor INTs unrouted -> NC)
JP1/JP2 = open (Vio / BT_Irq selectors) JP5 = 1-2 (DIL24 = 3V3_IO)
X-NUCLEO-53L9A1 (top board)
VL53L9CX ToF 3D LiDAR. I3C on PB8/PB9, level-shifted to sensor IOVDD.
= U5
U5 PI4ULS3V204: I3C SCL/SDA level shift, 3V3 <-> IOVDD.
= U6
U6 PI4ULS3V204: SYNC/CLK/XSHUT/INTR level shift.
= Y1
SW1 = INT
SW1=INT: ToF CLK from on-board Y1 12MHz. Host PB5/CLK_IN path idle (EXT).
= U7
U7 VL53L9CX ToF (0x52). On-board LDOs (from CN6 +5V) derive
IOVDD/AVDD(2V8)/DVDD(1V2) - AVDD/DVDD abstracted (NC).
SW1 = INT (ToF CLK from on-board Y1 12MHz; see switch)
J1 = 3V3 (Nucleo_IOVDD host-side shifter reference = 3.3V)
J2..J5 = linked (VBAT_LDD/VBAT_RX/AVDD/DVDD rails powered)
