hellosamblack/lidar-roomscanner/host/src/roomscan/web.py

"""Web-based real-time instrument. One reader thread (the neutral
`reader._run_reader`, shared with the desktop panel) feeds a latest-wins slot; a SINGLE asyncio
broadcast task fans every transformed frame out to all connected WebSocket
clients. This replaces the old per-connection `slot.get_nowait()` loop, whose
competing gets stole frames from one another when two tabs were open (§5.3).

The wire is multiplexed on one `/ws` socket: binary messages (point cloud, IR
image) carry a leading little-endian uint32 tag; JSON text messages carry a
`type` discriminator (metrics/event/log/cmd/state). See the design spec
docs/superpowers/specs/completed/2026-07-15-web-phase1-core-instrument-design.md §6.

Pure, socket-free helpers (classify_bus_line / select_colors /
pack_point_cloud / pack_ir_image / build_metrics_message) are factored out at
module level so the protocol/coloring logic is unit-testable without a server.
"""
from __future__ import annotations

import asyncio
import base64
import itertools
import json
import logging
import math
import os
import queue
import re
import shlex
import shutil
import socket
import struct
import subprocess
import sys
import tempfile
import threading
import time
from collections import deque
import webbrowser
import zlib
from contextlib import asynccontextmanager, suppress
from dataclasses import asdict, dataclass, field, replace
from pathlib import Path

import numpy as np
import uvicorn
from fastapi import FastAPI, WebSocket, WebSocketDisconnect
from fastapi.responses import FileResponse, JSONResponse, RedirectResponse, Response
from fastapi.staticfiles import StaticFiles
from starlette.websockets import WebSocketState

from .colors import gray, turbo
from . import commstatus
from .config import ViewerConfig
from .control import (
    CommandClient,
    CommandDispatcher,
    _manual_params_to_wire,
    _POWER_MODE_TO_WIRE,
    _RANGING_MODE_TO_WIRE,
)
from .decoder import StreamDecoder
from .deproject import Deprojector
from .ir_image import ir_range, reflectance_to_rgb
from .logbus import LogBus
from .magcal import MagCalibration
from .magsweep import (
    MagSweepSession,
    assign_cells,
    build_report as build_magcal_report,
    calibrated_directions,
    calibrated_norms,
    motion_state,
    view_calibration,
)
from .metrics import MetricsRegistry, MetricsSnapshot, ResourceSampler
from .flatfield import FlatFieldSet
from .pipeline import TransformStage
from .reader import _Pacer, _run_reader, follow_camera_target
from .protocol import (
    HEADER_SIZE,
    MAGIC,
    CommandCode,
    FrameHeader,
    FrameType,
    ProtocolError,
    RangingConfigAck,
    ResultCode,
    StandbyLevel,
    StreamId,
)
from .sensors import (
    AXIS_CONVENTION,
    SensorState,
    YawFusion,
    absolute_heading,
    boresight_view_deg,
    display_rotation,
    graft_yaw,
    gravity_body_from_imu_raw,
    ir_gravity_residual_deg,
    ir_gravity_rot,
    quat_mul,
    quat_pitch_alt_deg,
    quat_pitch_deg,
    quat_roll_alt_deg,
    quat_roll_deg,
    quat_to_matrix,
    quat_yaw_alt_deg,
    quat_yaw_deg,
    tilt_from_down_deg,
    triad_roll_deg,
    wrap180,
)
from . import profiles
from . import thumbs as thumbs_mod
from .motion import coherence
from .sources import FileSource, Recorder, SerialSource, UdpSource, get_best_source
from zeroconf import ServiceInfo, Zeroconf
from .thin_render import (
    DEFAULT_JPEG_QUALITY, THIN_HEIGHT, THIN_WIDTH, ThinCamera,
    ThinRenderer, ThinRenderUnavailable, extract_ir_full, extract_ir_grid, image_scene,
    jpeg_available, points_scene, unpack_mesh_scene, warm_jpeg_import,
)
from .slam.config import DetailedSlamPreset, preferred_device
from .slam.detailed import (build_manifest, estimate_seconds, sidecar_paths,
                            sidecar_status, write_manifest_atomic)
from .slam.detailed import delete_sidecar as detailed_delete_sidecar
from .slam.detailed import rename_sidecar as detailed_rename_sidecar
from .slam.meshprep import MeshPrep
from .slam.metrics import write_tum
from .slam.frames import baro_height_m
from .slam.showcase import PostProcessWorker
from .splat import list_splats as list_splats_on_disk
from .splat import list_source_videos, slugify, splat_defaults
from .viewer import Stats, resolve_args
from .weather import FALLBACK_MSL_PA, MslPressure

log = logging.getLogger("roomscan.web")

# Binary message type tags (first 4 bytes, little-endian uint32).
TAG_POINT_CLOUD = 1
TAG_IR_IMAGE = 2
TAG_MESH = 3               # SLAM reconstruction mesh (web Phase 4)
TAG_SURFACE = 4            # surface-interpolated point cloud (grid + triangles)
TAG_MAGPOSE = 5            # 30 Hz magcal pose/field sample (magcal 3D feedback)

# Broadcast cadences (seconds). Point cloud paces the outer loop at a 30 Hz
# target (owner, 2026-07-16) -- the cap must sit at or above the source rate so
# it never down-samples the stream; a slower source just re-sends the last frame.
# IR and metrics run on their own slower elapsed-time gates off the same task.
POINT_INTERVAL = 1.0 / 30.0
IR_INTERVAL = 1.0 / 15.0
METRICS_INTERVAL = 1.0 / 4.0
# `/ws-thin` render cadence (#194). Deliberately far slower than the point
# cloud: each tick is a full server-side 3D render (~27 ms) plus a 460 KB
# uncompressed frame, so 10 fps is ~4.6 MB/s per client on the wireless uplink.
THIN_INTERVAL = 1.0 / 10.0
THIN_TELEMETRY_INTERVAL = 0.5
# `thin_hello` negotiation clamps (#197) -- deliberately generous but bounded:
# a client that never sends `thin_hello` is unaffected (`ThinFlow` defaults
# reproduce THIN_INTERVAL / THIN_WIDTH / THIN_HEIGHT exactly).
THIN_HELLO_FPS_MIN = 1
# The fps ceiling is COUPLED to format (#197 review finding 5): a raw
# RGB565 480x480 frame is 460 800 bytes, so even today's 10 fps default is
# ~4.6 MB/s per client (see docs/thin-client.md); 60 fps raw would be
# ~27.6 MB/s and ~160% of the SINGLE shared render thread for just one
# client, starving the other (THIN_MAX_CLIENTS=2) even before the network is
# considered. A JPEG frame at the default quality is roughly 15-25 KB, so
# 60 fps JPEG (~1-1.5 MB/s) is cheaper than 10 fps raw -- raw keeps today's
# ceiling, jpeg gets the higher one.
THIN_HELLO_FPS_MAX_RAW = 10
THIN_HELLO_FPS_MAX_JPEG = 60
#: square resolutions only -- a non-square request is rejected outright and
#: the flow's prior width/height are kept, rather than distorting the image.
THIN_HELLO_RESOLUTIONS = (320, 480)
THIN_HELLO_QUALITY_MIN = 40
THIN_HELLO_QUALITY_MAX = 95
DEFAULT_THIN_FPS = 1.0 / THIN_INTERVAL   # 10.0, matches today's cadence exactly
# `/ws-thin` v2 flow control (#202, CrowPanel bandwidth spec 2026-08-18). The
# server never has more than the granted credits outstanding to a v2 client and
# DROPS (never queues) at zero credit -- on the CrowPanel's ~1.5 Mbit/s link,
# pushing faster than the client drains only fills TCP buffers until pings hit
# seconds and the client's staleness timeout flaps the session. Depth 2 = one
# frame on the wire while the client works on the previous one; deeper just
# recreates the queue this exists to remove, so the clamp ceiling stays small.
THIN_CREDITS_DEFAULT = 2
THIN_CREDITS_MIN = 1
THIN_CREDITS_MAX = 8
#: floor for a client-advertised `max_frame_bytes` -- below this even a
#: quality-40 320x320 JPEG cannot reliably fit, so the request is nonsense.
THIN_MAX_FRAME_BYTES_MIN = 4096
# `ir_cells`: how many IR zones a client says it can render. The 8x8 thumbnail the
# CrowPanel shipped with is a ~97% throwaway of a 54x42 = 2268-zone sensor, so a client
# that can hold the real thing asks for it here. Floor is the old 64 (asking for less
# than the v1 shape buys nothing); ceiling is generous headroom over 2268 for a future
# sensor, bounded so one client cannot ask the telemetry message to become enormous.
THIN_IR_CELLS_MIN = 64
THIN_IR_CELLS_MAX = 4096
#: window for the per-client `tx_fps` / `tx_bytes_per_s` telemetry figures.
THIN_TX_WINDOW_S = 5.0
# Hard cap on concurrent thin clients. Connection count is a real performance
# variable on this server (BUG-060), and a thin client costs a full render --
# far above a deflate. All clients share the one renderer (a second
# `OffscreenRenderer` aborts the process), so renders serialise: 2 clients x
# 10 fps = 20 renders/s, about 54 % of the render thread.
THIN_MAX_CLIENTS = 2
# Sensor (streams 9/10) broadcast cadence: 15 Hz is smooth for a handheld gizmo
# and well above the ~4 Hz sparkline need. History rides every message so a
# late-joining tab's sparklines are instantly full (Phase-1 late-joiner rule).
SENSOR_INTERVAL = 1.0 / 15.0
# Rolling window for the orientation jitter stats (roll/pitch/yaw/heading/overall):
# ~5s of `sensor` messages at SENSOR_INTERVAL (15 Hz) => ~75 frame-to-frame samples.
SENSOR_JITTER_WINDOW_S = 5.0
# Magnetometer-sweep (`magcal` modal) TRUTH cadence -- the JSON report: cell
# counts, verdicts, coverage, guidance. 5 Hz (raised from 4 when `cell_dirs`
# stopped riding every message: 4490 B -> 1982 B, so the raise is still ~2x
# cheaper than before). This is data that changes at HUMAN speed; the 30 Hz
# render payload rides the binary MAGPOSE channel instead (docs/web-protocol.md
# "Framing": high-rate render payloads are tagged binary, human-rate state is
# JSON). Sent ONLY to tabs that have the modal open -- `state.magcal_clients`.
MAGCAL_INTERVAL = 1.0 / 5.0
MISSING_PLANE_LOG_INTERVAL = 3.0   # debounce for missing-plane bus lines

# Recording & playback (web Phase 3).
CAPTURES_DIR = "captures"          # where Record writes + the library browses
# SLAM mode (web Phase 4).
RESULTS_DIR = "results"            # where Save writes the full-res map + trajectory
_TRAJ_TAIL_MAX = 256               # trajectory positions shipped in each `slam` message
_VALID_MODES = ("realtime", "slam")  # legacy inbound compatibility
_VALID_SOURCES = ("live", "view", "splat")
_VALID_DISPLAYS = ("point_cloud", "preview", "slam", "detailed")
_VALID_WALL_MODES = ("solid", "split")
# The playback speed segmented control maps ×0.5/×1/×2/Max onto these fps; a
# capture's own cadence is ~28 Hz, so ×1 (30 fps) plays it near-native and is
# the default. Max (0 -> interval 0) drains as fast as it decodes.
_SPEED_BASE_FPS = 30.0

_VALID_COLOR_MODES = ("depth", "reflectance", "confidence")
_VALID_IR_COLORMAPS = ("gray", "turbo")
_VALID_VIEW_COLORMAPS = ("turbo", "gray")
_VALID_SURFACE_MODES = ("grid", "spatial")
_VALID_IDLE_LEVELS = ("soft", "hard")
# View-page capture browser (§12). Sorting is applied CLIENT-side off the
# already-broadcast `captures` array -- the server persists the choice, it does
# not re-scan for it.
_VALID_BROWSER_SORTS = ("recent", "name", "size", "duration")
_VALID_BROWSER_VIEWS = ("grid", "list")
# One inbound `delete_captures` can never nominate more files than the library
# could plausibly hold; a WS peer is untrusted and this is the only destructive
# handler in the app.
_MAX_DELETE_BATCH = 200
# Real-time view modes (owner ask, 2026-07-29). Which frame the live cloud is
# shipped in -- see `view_rotation`. Real-time only; SLAM has its own camera.
_VALID_VIEW_MODES = ("world", "fpv", "mirror")

# --- camera framing per view mode (owner ask, 2026-07-30) --------------------
# All three views are described as an offset from ONE baseline: the FPV ground
# truth, i.e. a camera sitting exactly at the sensor looking down its boresight.
# All-zero offsets reproduce that camera exactly, in every mode. `distance_m`
# backs the eye off along the view axis, `height_m` lifts it, and
# `rotation_deg` swings it about the vertical axis through the aim point (which
# stays on the axis, so the subject stays framed).
#
# The modes differ only in what "the axis" is: in fpv/mirror it is the live
# boresight, because the server has already rotated the cloud into the
# boresight view frame (`view_rotation`); in world it is the fixed world
# forward. Those coincide exactly when the board is held in the reference pose,
# which is what makes the FPV baseline a common reference rather than three
# unrelated cameras. Ranges are validated on the wire AND on config load.
_CAM_DISTANCE_RANGE = (0.0, 15.0)      # metres back along the view axis
_CAM_HEIGHT_RANGE = (-5.0, 10.0)       # metres up (negative dips below)
_CAM_ROTATION_RANGE = (-180.0, 180.0)  # degrees; positive swings the eye right
# Auto-orbit is WORLD-ONLY: fpv/mirror are locked to the sensor, so there is no
# scene to circle. Azimuth only -- elevation and distance are untouched, which
# is why the client hands it to OrbitControls' own `autoRotate` rather than
# animating `rotation_deg` (that would also churn the persisted value at 30 Hz).
_ORBIT_SPEED_RANGE = (-60.0, 60.0)     # deg/s; negative reverses
# Oscillate mode (owner ask, 2026-07-31): a triangle wave about the azimuth
# where oscillation started -- run one way for N deg, reverse and run 2N deg,
# reverse and run 2N deg, repeat, so the camera swings between -N and +N of the
# start azimuth. `scene.js` owns the wave itself (it tracks
# `controls.getAzimuthalAngle()` client-side); the server just stores/validates
# the mode + amplitude like any other `set_view` field.
_VALID_ORBIT_MODES = ("continuous", "oscillate")
_ORBIT_AMPLITUDE_RANGE = (5.0, 180.0)  # degrees; matches the UI slider's range
# See-through (x-ray) strength. 0 is off and is the DEFAULT, so nothing about
# the render changes until it is asked for; 1 draws the occluded layer at full
# alpha over its occluder. Validated on the wire AND on config load.
_SEE_THROUGH_RANGE = (0.0, 1.0)


@dataclass
class ViewCam:
    """Camera framing for one view mode, as an offset from the FPV baseline."""
    distance_m: float = 0.0
    height_m: float = 0.0
    rotation_deg: float = 0.0


# Defaults: world is an elevated establishing shot, fpv/mirror sit just off the
# optical centre. A camera exactly AT the centre (all zeros) reproduces the
# depth image's own projection and renders flat -- the small default offset is
# what supplies the parallax that makes depth legible.
_DEFAULT_VIEW_CAM = {
    "world": ViewCam(4.2, 2.6, 0.0),
    "fpv": ViewCam(0.30, 0.20, 0.0),
    "mirror": ViewCam(0.30, 0.20, 0.0),
}

# `[viewer]` keys per mode, in (distance, height, rotation) order. The TOML
# writer is flat/scalar-only, so the nine values are nine plain floats.
_VIEW_CAM_CONFIG_KEYS = {
    m: (f"web_cam_{m}_distance_m", f"web_cam_{m}_height_m", f"web_cam_{m}_rotation_deg")
    for m in _VALID_VIEW_MODES
}
_VIEW_CAM_FIELDS = (("distance_m", _CAM_DISTANCE_RANGE),
                    ("height_m", _CAM_HEIGHT_RANGE),
                    ("rotation_deg", _CAM_ROTATION_RANGE))


def default_view_cam() -> dict[str, ViewCam]:
    """A fresh, independent copy of the per-mode defaults (never share the
    module-level `ViewCam` instances -- they are mutable and would leak edits
    across `UiState`s, which in tests reads as one test corrupting the next)."""
    return {m: replace(c) for m, c in _DEFAULT_VIEW_CAM.items()}

# --- orientation decomposition modes (owner ask, 2026-07-28) -----------------
# Presentation-only: every mode is a different VIEW of the same
# `sensor_state.fused_quat()` -- none of this feeds `display_rotation`, the
# point-cloud rotation path, or SLAM. See `sensors.py`'s
# "Alternate orientation decompositions" section for the per-mode math and
# exactly where each one's gimbal lock sits.
_VALID_ORIENTATION_MODES = ("zyx", "zxy", "boresight", "world")
# The Sensors card is pinned to World (owner ask, 2026-07-31: the decomposition
# picker is gone, the owner only ever used World) -- and in World the three
# slots are NOT Roll/Pitch/Yaw. `orientation_view`'s World branch returns
# `roll_deg = triad_roll_deg` (roll about the boresight vs true vertical),
# `pitch_deg = tilt_from_down_deg` (boresight angle from horizontal), and
# `yaw_deg = heading` (absolute magnetic heading). The other modes (zyx/zxy/
# boresight) stay on the wire for the deprecated desktop panel and keep their
# own math unchanged -- only the DEFAULT labels, which the World-only web UI
# actually shows, change here.
DEFAULT_AXIS_LABELS = ("Roll", "Tilt", "Heading")
# The default before the Sensors card was pinned to World (2026-07-31). World's
# three slots are triad roll, boresight tilt from horizontal, and absolute
# magnetic heading -- so "Pitch"/"Yaw" named the wrong quantities. Kept only so
# `ui_from_config` can recognise a stored copy of it as un-customised.
_LEGACY_AXIS_LABELS = ("Roll", "Pitch", "Yaw")
_MAX_LABEL_LEN = 24

# "Zero yaw here" (owner ask, 2026-07-29): which modes have a free-running,
# SFLP-derived yaw-like slot that a user offset even applies to. "world" is
# deliberately absent -- its yaw slot is `heading_full`, an ABSOLUTE magnetic
# bearing computed independently of the fused quat's own yaw (see
# `absolute_heading`), so grafting it would corrupt its meaning rather than
# just re-zero a drifting reference. `_YAW_GRAFT_SIGN` is the sign to apply
# when CAPTURING an offset from a given mode's current `yaw_deg` (i.e. the
# multiplier `s` such that `graft_yaw(quat, s * yaw_deg)` reports that mode's
# yaw-like slot as ~0 immediately after capture): zyx/zxy report MORE positive
# as `graft_yaw`'s delta grows (so capturing needs the negative), boresight's
# azimuth is a compass bearing with the opposite handedness and reports LESS
# positive for the same delta (so capturing needs the positive) -- verified
# numerically against the actual decompositions, not derived by hand, because
# ZYX/ZXY/boresight are three genuinely different functions of the same
# rotation, not sign-flipped copies of one formula.
_YAW_GRAFT_SIGN = {"zyx": -1.0, "zxy": -1.0, "boresight": 1.0}
# The "near singularity" warning threshold for every decomposition mode below.
# Inherited from `YawFusion.gimbal_margin_deg`, which is gone (BUG-051: yaw
# fusion no longer has a singularity to gate on) -- this is a DISPLAY warning
# about the selected decomposition's own conditioning and is unrelated to it.
ORIENTATION_SINGULARITY_MARGIN_DEG = 15.0
# World mode's roll reference: the device's structural TOP in body coordinates.
# Body +X is the instrument's BOTTOM -- `static/devicemodel.js`'s MOUNT_ROTATION
# is a 180 deg turn about the boresight for exactly this reason -- so referencing
# `triad_roll_deg` to body +X (its default) made the normal upright grip read
# ~+-180 deg, sitting on the wrap and reading like a fault (BUG-051). Referenced
# to body -X instead, the normal grip reads ~0 deg and the wrap moves to
# upside-down, where it belongs. `triad_roll_deg` itself is untouched: it is a
# primitive, and its default stays body +X.
_DEVICE_TOP_BODY = (-1.0, 0.0, 0.0)
# Precedent: `YawFusion.anomaly_frac=0.3` gates its heading update on the
# calibrated mag magnitude; reused verbatim for the World mode's validity
# indicator (owner ask: "reuse that notion rather than inventing a new one").
WORLD_MODE_MAG_ANOMALY_FRAC = 0.3
# World mode's gravity reference is corrupted by linear acceleration; flag it
# when the stream-11 accel batch's mean norm strays this far from 1 g.
WORLD_MODE_ACCEL_TOL_G = 0.15


def idle_standby_level(name: str) -> int:
    """Map an `idle_level` name to its SET_STANDBY param. Anything but "hard"
    (including an unrecognized value) is treated as soft standby -- the safer,
    instant-resume default."""
    return int(StandbyLevel.HARD if name == "hard" else StandbyLevel.SOFT)

# Success command results look like "OK applied=1" / "REJECTED applied=0":
# a ResultCode name (upper snake) followed by applied=<int>.
_CMD_SUCCESS_RE = re.compile(r"^[A-Z0-9_]+ applied=-?\d+$")
_EVENT_RE = re.compile(r"^\[event\] code=(-?\d+) detail=(-?\d+)(?: (.*))?$")


# --- ui state ----------------------------------------------------------------

@dataclass
class UiState:
    """Server-held view/IR settings, so a late-joining tab is brought current
    the instant it connects (§5.1). All mutations are pure server state -- no
    device round-trip -- so color/IR changes apply regardless of device busy
    state."""
    color_mode: str = "depth"
    ir_colormap: str = "gray"
    ir_freeze: bool = False
    ir_freeze_range: tuple[float, float] | None = None
    # "Calibrated / Uncalibrated" toggle (Device card): apply the configured
    # mode-aware flat-field reflectance correction, or show the raw sensor FPN.
    # This is HOST-shared server state, not a per-client preference: there is one
    # `UiState` and one `TransformStage` for all clients, so flipping it changes
    # the host's output for everyone and persists once on the host (config
    # `[calibration] flatfield_enabled`). The MAP is picked host-side by the
    # current ranging mode; this only enables/disables applying it. No-op when no
    # map is configured, hence default on. Drives `stage.flatfield_enabled`.
    calibrated: bool = True
    # SLAM mode (web Phase 4). `mode` gates the whole SLAM pipeline: the worker
    # is only fed (and only constructed) while mode == "slam", so real-time mode
    # burns no GPU. The three display toggles ride the same one-way `state` echo
    # as color/IR, so a late-joining tab is brought current on connect.
    # `mode` is retained as a short-lived compatibility alias for older MCP
    # clients. The Live/View model is source + display; only `display == slam`
    # arms the latest-wins live runner.
    mode: str = "realtime"
    source: str = "live"              # "live" | "view" | "splat" (not persisted)
    display: str = "point_cloud"      # "point_cloud" | "preview" | "slam" | "detailed"
    selected_capture: str | None = None
    # Splat source (offline Gaussian-splat reconstruction). `selected_splat` is
    # the slug of the splat the viewer renders; the reader is left untouched (a
    # splat is static geometry the client draws, not a device/replay stream).
    selected_splat: str | None = None
    slam_trajectory: bool = True
    slam_walls: str = "split"          # "solid" | "split" -> MeshPrep wall_mode
    slam_follow: bool = True
    # Laser-wear auto-idle (SET_STANDBY): when enabled, the server idles the ToF
    # sensor while no tab is connected and wakes it on connect. `idle_level` picks
    # the depth (soft = FSM standby, hard = XSHUT power-down). These ride the same
    # persisted-pref + `state` echo path as the display toggles so a settings UI
    # (or roomscan.toml) can drive them; the debounce delay is config-only.
    view_colormap: str = "turbo"       # 3D viewport colormap: "turbo" | "gray"
    point_size: float = 0.025          # Three.js point size, world units (sizeAttenuation); when
                                       # point_size_auto it is the size at 1 m of RANGE instead
    point_size_auto: bool = True       # scale each point by its range from the sensor, so every
                                       # zone's splat subtends the same solid angle (the zone
                                       # pitch grows as r*dtheta, so one fixed size cannot cover
                                       # a near and a far surface at once)
    # See-through / x-ray (owner ask, 2026-07-31): whenever geometry occludes
    # other geometry, let the hidden layer show through its occluder. Strength
    # 0..1; 0 is off and reproduces the opaque render exactly (so the client
    # draws NO extra pass at 0 -- see scene.js). It is deliberately not a plain
    # material opacity: dialling opacity down would fade every surface against
    # the background, including the ones hiding nothing. Instead the client
    # redraws the same geometry with the depth test INVERTED, so only fragments
    # that lost the depth test -- i.e. exactly the occluded ones -- are blended
    # back over their occluder at this alpha. Unoccluded surfaces are untouched.
    see_through: float = 0.0
    surface_enabled: bool = False      # surface interpolation (triangulated mesh)
    surface_mode: str = "grid"         # "grid" (relative depth %) | "spatial" (3D Euclidean)
    surface_threshold_pct: float = 4.0 # grid: max depth gap %; spatial: % of mean depth -> metres
    # Real-time view mode (owner ask, 2026-07-29): "world" orbits a
    # gravity-aligned scene (the original behaviour), "fpv" ships the cloud in
    # the sensor's own frame for a camera locked to the sensor, "mirror" is fpv
    # with X negated so the user can look at themselves. See `view_rotation`.
    view_mode: str = "world"
    # Camera framing per view mode, all referenced to the FPV baseline --
    # see `_DEFAULT_VIEW_CAM`. Keyed by view mode; always all three keys.
    view_cam: dict[str, ViewCam] = field(default_factory=default_view_cam)
    # Slow auto-orbit of the world view (owner ask, 2026-07-30). Azimuth only.
    orbit_enabled: bool = False
    orbit_speed_deg_s: float = 6.0     # 60 s per revolution
    # Oscillate mode (owner ask, 2026-07-31): "continuous" is the original
    # behaviour above; "oscillate" swings +-orbit_amplitude_deg of the azimuth
    # where oscillation started (a triangle wave, driven client-side in
    # scene.js). See `_VALID_ORBIT_MODES` / `_ORBIT_AMPLITUDE_RANGE`.
    orbit_mode: str = "continuous"
    orbit_amplitude_deg: float = 45.0
    idle_enabled: bool = True
    idle_level: str = "soft"           # "soft" | "hard"
    browser_idle_timeout_s: float = 300.0   # idle.js: how long without user
                                            # activity before the client parks
                                            # itself; server-configured so a
                                            # single value governs every tab
    # View-page capture browser (§12). Presentation-only and persisted; see the
    # `[viewer] web_browser_*` comment in config.py for why sort is client-side.
    browser_sort: str = "recent"       # "recent" | "name" | "size" | "duration"
    browser_view: str = "grid"         # "grid" | "list"
    browser_thumbs: bool = True
    # Orientation decomposition (owner ask, 2026-07-28): which VIEW of the
    # orientation quaternion the Sensors panel reports, plus user-renamable
    # axis labels applied positionally (slot 1/2/3) whichever mode is active.
    # Presentation-only -- see the `_VALID_ORIENTATION_MODES` comment above.
    orientation_mode: str = "zyx"
    orientation_labels: tuple[str, str, str] = DEFAULT_AXIS_LABELS
    # "Zero yaw here" (owner ask, 2026-07-29): a world-Z `graft_yaw` delta
    # applied to the relative yaw-like slot of zyx/zxy/boresight ONLY, so the
    # Sensors card can read 0 at whatever attitude the user pressed the
    # button. World mode's `yaw_deg` is the absolute magnetic heading and is
    # NEVER offset -- see `_YAW_GRAFT_SIGN` and `build_sensor_message`.
    # Presentation-only, same guarantee as `orientation_mode` above: never
    # touches `fused_quat()`/`display_rotation`/the point-cloud rotation/SLAM.
    yaw_offset_deg: float = 0.0
    # Elevation datum (owner ask, 2026-07-31): the Delta button captures the
    # current smoothed elevation here, and the Sensors card switches from an
    # absolute reading ("935 ft") to a signed change since that datum
    # ("+12 ft"). None = absolute. Persisted, so the datum survives a restart;
    # presentation-only, like the yaw offset above.
    elevation_datum_ft: float | None = None


# --- pure helpers (no socket, no async) -------------------------------------

def classify_bus_line(line: str, command_labels: set[str] | None = None) -> dict | None:
    """Classify one LogBus line into a `cmd`/`event`/`log` JSON dict (§7.1).

    Robustness approach: we do NOT need a live registry of in-flight commands.
    A line is a device event iff it starts with the reader's `[event] ` prefix;
    a command result iff it contains the ` -> ` marker CommandDispatcher always
    emits AND its tail matches one of the four known status shapes (replay /
    busy / TIMEOUT / ERROR / "<ResultCode> applied=<n>"). `command_labels`, when
    supplied, further gates cmd-classification to labels we actually dispatched
    (belt-and-suspenders against a free-text log line that happens to contain
    ` -> `); when None, suffix-matching alone decides. Anything else is a plain
    log line. Returns None only for an empty/None input.
    """
    if not line:
        return None

    m = _EVENT_RE.match(line)
    if m:
        code, detail, msg = m.group(1), m.group(2), m.group(3) or ""
        return {"type": "event", "code": int(code), "detail": int(detail), "msg": msg}
    if line.startswith("[event]"):
        # e.g. "[event] undecodable payload (12 B)" -- not parseable as structured
        return {"type": "log", "line": line}

    if " -> " in line:
        label, _, tail = line.partition(" -> ")
        status = _cmd_status(tail)
        if status is not None and (command_labels is None or label in command_labels):
            return {"type": "cmd", "label": label, "status": status, "detail": tail}

    return {"type": "log", "line": line}


def _cmd_status(tail: str) -> str | None:
    """Map a CommandDispatcher result tail to a status, or None if it doesn't
    look like a command result at all (so the whole line falls back to log)."""
    if tail.endswith("not available in replay"):
        return "error"
    if "busy, command already in flight" in tail:
        return "busy"
    if tail.startswith("TIMEOUT"):
        return "timeout"
    if tail.startswith("ERROR"):
        return "error"
    if _CMD_SUCCESS_RE.match(tail):
        return "ok"
    return None


def _apply_colormap(vn: np.ndarray, colormap: str) -> np.ndarray:
    return gray(vn) if colormap == "gray" else turbo(vn)


# `display_rotation` now lives in `sensors.py` (beside T_WORLD_TO_CV /
# T_CV_TO_BODY, the two matrices it composes) and is re-exported here: the
# thumbnail renderer needs it and must not import `web`. See the import block
# at the top of this file; the name is unchanged for every existing caller.


# A horizontal (left-right) flip of the live cloud. The ToF/CV frame is
# X=Right, Y=Down, Z=Forward (`docs/coordinate-frames.md`), so negating X alone
# mirrors about the vertical axis -- a selfie flip -- and leaves up/down and
# range untouched. The IR raster shares that index space, which is why the same
# idea shows up client-side as one `scaleX(-1)` on the IR pane.
_MIRROR_X = np.diag([-1.0, 1.0, 1.0])
_WORLD_DOWN_CV = np.array([0.0, 1.0, 0.0])   # Open3D CV world is Y-DOWN
_CV_FORWARD = np.array([0.0, 0.0, 1.0])
_CV_UP = np.array([0.0, -1.0, 0.0])


def boresight_view_frame(grav_rot: np.ndarray) -> np.ndarray:
    """World -> a CV camera frame aimed along the sensor's boresight but *level*.

    Rows are the frame's right/down/forward axes in the gravity-aligned world:
    forward is the boresight, and right is forced perpendicular to world down,
    which is what keeps the horizon flat. Composed with `grav_rot` (below) the
    net effect on the cloud is a pure roll about the boresight -- the same
    un-rolling the IR pane already gets from `ir_gravity_rot`, so the FPV view
    and the IR monitor finally agree on which way is up.
    """
    z = grav_rot @ _CV_FORWARD
    z = z / np.linalg.norm(z)
    x = np.cross(_WORLD_DOWN_CV, z)
    nx = float(np.linalg.norm(x))
    if nx < 1e-6:
        # Aimed straight up or down: "level" is undefined about a vertical
        # boresight, so fall back to the sensor's own up axis. Without this the
        # frame would blow up exactly when a handheld scanner looks at the
        # ceiling or the floor.
        x = np.cross(grav_rot @ _CV_UP, z)
        nx = float(np.linalg.norm(x))
        if nx < 1e-6:                       # unreachable for a real rotation
            return np.eye(3)
    x = x / nx
    return np.stack([x, np.cross(z, x), z])


def view_rotation(grav_rot: np.ndarray | None, view_mode: str) -> np.ndarray | None:
    """The rotation baked into the live cloud for the selected real-time view mode.

    The mode is resolved HERE, server-side, rather than by moving the client's
    camera: the cloud is rotated by the smoothed display quat at the broadcast
    rate, while the client's only orientation feed (`sensor.rot`) is raw and
    half as fast, so a client-rotated camera would lag and slosh against the
    geometry it is supposed to be locked to. Baking the frame in instead makes
    the client camera a *static* pose, matched by construction.

    - "world"  -> `grav_rot`: gravity-aligned, free orbit (the original behaviour)
    - "fpv"    -> look down the boresight, still gravity-levelled (owner: FPV and
                  Mirror "need to respect gravity the same way world does" --
                  the camera follows the sensor's aim, but the scene never rolls)
    - "mirror" -> fpv, then flipped left-right
    """
    if view_mode == "world":
        return grav_rot
    if grav_rot is None:
        # No orientation yet (ToF-only session): the cloud is already in the
        # sensor's frame, which IS the boresight view -- there is simply no
        # gravity to level against. Mirror still mirrors.
        return _MIRROR_X if view_mode == "mirror" else None
    rot = boresight_view_frame(grav_rot) @ grav_rot
    return _MIRROR_X @ rot if view_mode == "mirror" else rot


def rotate_points(pts: np.ndarray, rot: np.ndarray | None) -> np.ndarray:
    """Rotate an (..., 3) array of CV-frame points by `rot`, returning float32.
    A no-op (same array back) when `rot` is None or there are no points, so the
    un-oriented path stays allocation-free."""
    if rot is None or pts.size == 0:
        return pts
    return np.ascontiguousarray(pts @ rot.T, dtype=np.float32)


def rotation_key(rot: np.ndarray | None):
    """Cache key for `rot`: quantized so a stationary sensor keeps hitting the
    cached point-cloud bytes, while real motion invalidates them."""
    return None if rot is None else tuple(np.round(rot.ravel(), 3).tolist())


def quat_slerp(a, b, t: float):
    """Shortest-arc spherical interpolation between unit quats [w,x,y,z]."""
    qa = np.asarray(a, dtype=np.float64)
    qb = np.asarray(b, dtype=np.float64)
    dot = float(qa @ qb)
    if dot < 0.0:            # take the short way round (q and -q are the same rotation)
        qb, dot = -qb, -dot
    dot = min(1.0, max(-1.0, dot))
    if dot > 0.9995:         # nearly parallel: lerp is numerically safer than slerp
        q = qa + t * (qb - qa)
    else:
        theta = math.acos(dot)
        s = math.sin(theta)
        q = (math.sin((1.0 - t) * theta) / s) * qa + (math.sin(t * theta) / s) * qb
    n = float(np.linalg.norm(q))
    return tuple(qa) if n < 1e-12 else tuple(q / n)


def quat_angle_deg(a, b) -> float:
    """Angle in degrees between two unit quats (rotation-aware, sign-agnostic)."""
    dot = abs(float(np.asarray(a, dtype=np.float64) @ np.asarray(b, dtype=np.float64)))
    return float(math.degrees(2.0 * math.acos(min(1.0, max(-1.0, dot)))))


def quat_rotvec(a, b) -> np.ndarray:
    """Rotation vector (axis × angle, in degrees) taking unit quat `a` to `b`."""
    qa = np.asarray(a, dtype=np.float64)
    qb = np.asarray(b, dtype=np.float64)
    if qa @ qb < 0.0:
        qb = -qb                                   # shortest arc
    conj = np.array([qa[0], -qa[1], -qa[2], -qa[3]])
    rel = np.asarray(quat_mul(tuple(conj), tuple(qb)), dtype=np.float64)
    if rel[0] < 0.0:
        rel = -rel
    v = rel[1:]
    n = float(np.linalg.norm(v))
    if n < 1e-12:
        return np.zeros(3)
    angle = 2.0 * math.atan2(n, float(rel[0]))
    return math.degrees(angle) * (v / n)


class OrientationSmoother:
    """Coherence-gated low-pass on the gravity-alignment quaternion.

    Measured on a *stationary* rig (2026-07-28, live Ethernet stream): the fused
    orientation carries ~0.14 deg mean / 0.25 deg p95 of zero-mean noise per
    update — net rotation 0.14 deg over 15 s against 22.9 deg of summed absolute
    change, i.e. essentially pure jitter. Rotating the cloud by that raw signal
    swings a 3 m lever arm, which is why it reads as shimmer at the cloud edges.

    A magnitude deadband cannot fix this, for the same reason it could not fix
    the SLAM translation jitter (slam/motion.py): 0.25 deg/frame of noise
    overlaps a slow deliberate pan (~20 deg/s = 0.7 deg/frame at 28 fps), so any
    threshold that suppresses the noise also drags on real aiming. The
    discriminator that separates them is directional COHERENCE — real rotation
    accumulates in a consistent direction (-> 1), noise cancels (-> 1/sqrt(N)).
    So this reuses `slam.motion.coherence` on the per-update rotation vectors:
    incoherent history damps by `floor_alpha`, coherent motion passes 1:1, and a
    single large step short-circuits the window so a fast flick never lags.

    Strictly display-only. SLAM feeds off `sensor_state.fused_quat()` directly,
    so a smoothed display quat can never reach the reconstruction — the same
    invariant that made the SLAM stationarity hold safe.
    """

    def __init__(self, window: int = 10, coherence_thresh: float = 0.5,
                 snap_deg: float = 2.0, floor_alpha: float = 0.05):
        self.window = int(window)
        self.coherence_thresh = float(coherence_thresh)
        self.snap_deg = float(snap_deg)
        self.floor_alpha = float(floor_alpha)
        self._held: tuple[float, float, float, float] | None = None
        self._prev_raw: tuple[float, float, float, float] | None = None
        self._hist: deque = deque(maxlen=self.window)

    def _alpha(self, delta_deg: float) -> float:
        # A single large step is motion whatever the history says -- act now.
        if delta_deg >= self.snap_deg:
            return 1.0
        # Never suppress before there's enough evidence to call it jitter.
        if len(self._hist) < self.window:
            return 1.0
        coh = coherence(np.array(self._hist))
        if coh <= self.coherence_thresh:
            return self.floor_alpha
        span = max(1.0 - self.coherence_thresh, 1e-9)
        ramp = (coh - self.coherence_thresh) / span
        return self.floor_alpha + (1.0 - self.floor_alpha) * ramp

    @property
    def held(self):
        """The current smoothed quat (None before the first sample). Read-only
        view for consumers that need the display orientation outside the tick
        that produced it -- e.g. the `sensor` message's `ir_roll_deg`, which must
        agree with the IR pane's snap."""
        return self._held

    def update(self, quat):
        """Feed the newest fused quat; return the smoothed one to display."""
        if quat is None:
            return None
        quat = tuple(float(v) for v in quat)
        if self._held is None:
            # First sample: adopt outright. Easing in from identity would swing
            # the whole scene through a large arc on the first frame.
            self._held = self._prev_raw = quat
            return self._held
        # Always measure increments RAW-to-RAW, never against the held value, or
        # damping would feed back into the motion estimate and lock the gate shut.
        self._hist.append(quat_rotvec(self._prev_raw, quat))
        self._prev_raw = quat
        self._held = quat_slerp(self._held, quat,
                                self._alpha(quat_angle_deg(self._held, quat)))
        return self._held

    def reset(self) -> None:
        """Drop the held/raw quat + coherence history so a source switch
        (issue #101) can't ease the FIRST frame of a new source in from the
        old one's orientation -- the same "adopt outright" first-sample path
        `update()` already takes when `_held` is None."""
        self._held = None
        self._prev_raw = None
        self._hist.clear()


#: Metres -> feet. The elevation readout is in feet (owner ask, 2026-07-31).
FT_PER_M = 3.280839895013123

#: EMA time constant for the elevation readout, seconds.
#:
#: BUG-037 measured the frame-rate barometer at ~3.1 Pa RMS of sample-to-sample
#: noise, which is **~267 mm RMS of apparent altitude** (~380 mm frame to
#: frame, ~1.2 ft). A raw readout would flicker over a foot several times a
#: second and read as broken. 6 s is long enough to sit still to ~0.1 ft
#: (267 mm / sqrt(6 s * 15 Hz) ~ 28 mm) and short enough that walking up a
#: flight of stairs settles before you reach the top. Stated in the row's
#: tooltip, because a filtered readout that does not say it is filtered is a
#: lie about the instrument's response time.
ELEVATION_TAU_S = 6.0


class ElevationSmoother:
    """Time-constant EMA over barometric altitude (metres), for display only.

    Deliberately time-based rather than a fixed per-sample alpha: the `sensor`
    message is emitted on an elapsed-time gate, not per frame, and a stalled
    stream (replay paused, device idled) must not make the filter's effective
    time constant balloon. `alpha = 1 - exp(-dt/tau)` gives the same 6 s
    response whatever the sample spacing.

    Never feeds SLAM -- the mapper does its own, differently-shaped barometric
    handling (`Mapper._apply_baro_z`, a bounded complementary correction), and
    the two must not be confused for each other.
    """

    def __init__(self, tau_s: float = ELEVATION_TAU_S, clock=time.monotonic):
        self.tau_s = max(1e-3, float(tau_s))
        self._clock = clock
        self._value_m: float | None = None
        self._t_prev: float | None = None

    @property
    def value_m(self) -> float | None:
        return self._value_m

    @property
    def value_ft(self) -> float | None:
        return None if self._value_m is None else self._value_m * FT_PER_M

    def update(self, altitude_m) -> float | None:
        """Feed the newest raw altitude (m); return the smoothed one."""
        if altitude_m is None:
            return self._value_m
        altitude_m = float(altitude_m)
        now = self._clock()
        if self._value_m is None or self._t_prev is None:
            self._value_m, self._t_prev = altitude_m, now
            return self._value_m
        dt = max(0.0, now - self._t_prev)
        self._t_prev = now
        alpha = 1.0 - math.exp(-dt / self.tau_s) if dt > 0.0 else 0.0
        self._value_m += alpha * (altitude_m - self._value_m)
        return self._value_m

    def reset(self) -> None:
        self._value_m = self._t_prev = None


def _sanitize_axis_labels(labels) -> tuple[str, str, str]:
    """Coerce an inbound labels value to exactly 3 short, non-empty strings,
    falling back to `DEFAULT_AXIS_LABELS` slot-by-slot on anything malformed
    (wrong length/type, empty/whitespace-only entry, absurdly long) -- a
    stray WS message must never leave a blank or runaway-length label stuck
    in the UI (or persisted to disk)."""
    out = list(DEFAULT_AXIS_LABELS)
    if isinstance(labels, (list, tuple)):
        for i, v in enumerate(labels[:3]):
            if isinstance(v, str) and v.strip():
                out[i] = v.strip()[:_MAX_LABEL_LEN]
    return (out[0], out[1], out[2])


def _mag_validity(mag_ut, mag_cal: MagCalibration | None):
    """(valid, reason, measured_ut, expected_ut) for the World mode's heading
    component. `valid` gates on the calibrated+axis-corrected mag magnitude
    matching the fitted field strength within `WORLD_MODE_MAG_ANOMALY_FRAC` --
    the same anomaly notion `YawFusion` already gates its heading update on
    (owner ask: reuse it, don't invent a second threshold). No calibration at
    all is reported as invalid with its own reason, not silently "valid"."""
    if mag_cal is None or mag_ut is None:
        return False, "no magnetometer calibration", None, None
    cal_mag = AXIS_CONVENTION @ mag_cal.apply(mag_ut)
    measured = float(np.linalg.norm(cal_mag))
    expected = float(mag_cal.field_ut)
    ok = abs(measured - expected) <= WORLD_MODE_MAG_ANOMALY_FRAC * expected
    reason = None if ok else (
        f"mag field {measured:.1f} uT vs calibrated {expected:.1f} uT "
        f"(>{WORLD_MODE_MAG_ANOMALY_FRAC:.0%} off -- local magnetic interference?)")
    return ok, reason, measured, expected


def _accel_motion_flag(batch) -> bool | None:
    """True if the stream-11 accel batch's mean norm strays more than
    `WORLD_MODE_ACCEL_TOL_G` from 1 g -- a cheap "is the device accelerating"
    proxy. Linear acceleration is indistinguishable from gravity tilt to a
    3-axis accelerometer, so this is precisely when the World mode's
    gravity-only tilt/roll degrade (that dynamic weakness is the whole reason
    the gyro + complementary filter exist for the primary orientation).
    None when no IMU_RAW batch is available -- motion state is simply
    unknown, not "assumed stationary"."""
    if batch is None or batch.accel_g.shape[0] == 0:
        return None
    norm = float(np.linalg.norm(batch.accel_g.mean(axis=0)))
    return abs(norm - 1.0) > WORLD_MODE_ACCEL_TOL_G


def orientation_view(mode: str, quat, mag_ut_raw=None, heading_full: float | None = None,
                      mag_cal: MagCalibration | None = None, imu_raw_batch=None) -> dict:
    """Decompose `quat` into the selected presentation MODE's three named
    slots (`roll_deg`/`pitch_deg`/`yaw_deg` -- generic positional names; what
    each one physically means depends on `mode`, see `sensors.py`), plus how
    close the CURRENT attitude is to that mode's own singularity.

    Presentation-only: reads `sensor_state.fused_quat()` (passed in as
    `quat`) and never writes anything back -- `display_rotation`/
    `fused_quat()`/the SLAM path are untouched by which mode is selected.

    Returns a dict always shaped {roll_deg, pitch_deg, yaw_deg,
    singularity_margin_deg, near_singularity, valid, reason, ...mode extras}.
    `valid`/`reason` gate the MAG-dependent yaw slot only (World mode); the
    gravity-only roll/pitch slots are reported regardless (their own
    trustworthiness is `near_singularity`, not `valid`)."""
    if quat is None:
        return {"roll_deg": None, "pitch_deg": None, "yaw_deg": None,
                "singularity_margin_deg": None, "near_singularity": False,
                "valid": False, "reason": "no orientation yet"}

    if mode == "zxy":
        roll = quat_roll_alt_deg(quat)
        pitch = quat_pitch_alt_deg(quat)
        yaw = quat_yaw_alt_deg(quat)
        margin = 90.0 - abs(pitch)
        return {"roll_deg": roll, "pitch_deg": pitch, "yaw_deg": yaw,
                "singularity_margin_deg": margin,
                "near_singularity": margin < ORIENTATION_SINGULARITY_MARGIN_DEG,
                "valid": True, "reason": None}

    if mode == "boresight":
        azimuth, elevation, roll = boresight_view_deg(quat)
        margin = 90.0 - abs(elevation)
        return {"roll_deg": roll, "pitch_deg": elevation, "yaw_deg": azimuth,
                "singularity_margin_deg": margin,
                "near_singularity": margin < ORIENTATION_SINGULARITY_MARGIN_DEG,
                "valid": True, "reason": None}

    if mode == "world":
        raw_down = gravity_body_from_imu_raw(imu_raw_batch)
        gravity_source = "imu_raw"
        if raw_down is None:
            r = quat_to_matrix(*quat)
            raw_down = tuple((r.T @ np.array([0.0, 0.0, -1.0])).tolist())
            gravity_source = "quat"
        tilt = tilt_from_down_deg(raw_down)
        roll = triad_roll_deg(raw_down, up_ref_body=_DEVICE_TOP_BODY)
        heading = heading_full   # reuse the caller's absolute_heading(quat, calibrated_mag)
        mag_valid, mag_reason, mag_norm, mag_expected = _mag_validity(mag_ut_raw, mag_cal)
        motion_flag = _accel_motion_flag(imu_raw_batch)
        reasons = [r for r in (mag_reason,) if r]
        if motion_flag:
            reasons.append("device is accelerating -- gravity tilt reference degraded")
        if heading is None and mag_valid:
            # A good mag reading with no heading means the aim itself has no
            # bearing -- say which, rather than leaving a bare "—" (BUG-058).
            reasons.append("boresight within 10 deg of vertical -- no compass bearing exists")
        margin = 90.0 - abs(tilt)
        return {"roll_deg": roll, "pitch_deg": tilt, "yaw_deg": heading,
                "singularity_margin_deg": margin,
                "near_singularity": margin < ORIENTATION_SINGULARITY_MARGIN_DEG,
                "valid": mag_valid and not motion_flag and heading is not None,
                "reason": "; ".join(reasons) if reasons else None,
                "gravity_source": gravity_source,
                "mag_norm_ut": mag_norm, "mag_expected_ut": mag_expected,
                "motion_stable": (None if motion_flag is None else not motion_flag)}

    # default: "zyx" (and any unrecognized value -- fail safe to the original,
    # always-on-by-default decomposition rather than raising)
    roll = quat_roll_deg(quat)
    pitch = quat_pitch_deg(quat)
    yaw = quat_yaw_deg(quat)
    margin = 90.0 - abs(pitch)
    return {"roll_deg": roll, "pitch_deg": pitch, "yaw_deg": yaw,
            "singularity_margin_deg": margin,
            "near_singularity": margin < ORIENTATION_SINGULARITY_MARGIN_DEG,
            "valid": True, "reason": None}


def _unit_quat(q) -> tuple[float, float, float, float]:
    """Re-normalize a [w,x,y,z] quaternion to unit length (float64).

    Device quats are float32 and not always exactly unit-norm. Skipping this
    before a dot product lets `|a . b|` exceed 1.0, get clamped to exactly
    1.0 by the acos guard, and silently report a ZERO angle for the smallest
    real steps -- the bug that produced a bogus zero-jitter reading on
    2026-07-28. Only needed for the dot-product angle; `quat_yaw_deg` /
    `quat_pitch_deg` / `quat_roll_deg` tolerate the float32 slop fine."""
    arr = np.asarray(q, dtype=np.float64)
    n = float(np.linalg.norm(arr))
    if n < 1e-12:
        return (1.0, 0.0, 0.0, 0.0)
    return tuple(arr / n)


_JITTER_SIGNALS = ("roll", "pitch", "yaw", "heading", "orientation")


def _jitter_stats(samples: list[dict[str, float]]) -> dict:
    """[{signal: abs frame-to-frame delta_deg}, ...] -> per-signal {mean_deg,
    p95_deg, n}. mean/p95 of the ABSOLUTE step, not the signed value (a jitter
    magnitude, not a drift). p95 is the headline statistic (measured CV 1.45%,
    the most stable of mean/median/p95 on this signal); mean is secondary.
    MEDIAN is deliberately not reported: quantization ties pile up at
    near-zero steps and make it the least stable (CV 4.41%). `n == 0` (no diff computed yet --
    fewer than two raw samples fed) reports None, not 0.0 -- a flat line is not the same claim
    as "no data". A single diff (n=1) is a well-defined mean/p95 of one value."""
    out = {}
    for key in _JITTER_SIGNALS:
        vals = [s[key] for s in samples if key in s]
        if not vals:
            out[key] = {"mean_deg": None, "p95_deg": None, "n": 0}
        else:
            arr = np.asarray(vals, dtype=np.float64)
            out[key] = {
                "mean_deg": float(arr.mean()),
                "p95_deg": float(np.percentile(arr, 95)),
                "n": len(vals),
            }
    return out


class OrientationJitter:
    """Rolling-window frame-to-frame noise stats for the RAW (unsmoothed)
    fused orientation -- roll/pitch/yaw/heading plus the overall angular step
    between consecutive quaternions (the quaternion dot-product angle).

    Computed server-side from FULL-PRECISION internal values, fed once per
    `sensor` message (never from the rounded wire fields -- `rot` is rounded
    to 5dp / ~0.0006 deg, which would censor exactly the noise floor this
    exists to measure). Feeds off `sensor_state.fused_quat()` directly, the
    same pre-`OrientationSmoother` signal SLAM sees -- this reports real
    sensor noise, not the display-smoothed shimmer-suppressed one.

    Angular signals (roll/yaw/heading) diff with `wrap180` so a heading
    crossing 360->0 doesn't register as a 360 deg jump; pitch is bounded
    already but wrapped too for uniformity. The overall-orientation angle
    re-normalizes both quats first (`_unit_quat`) -- see its docstring.

    `orientation` (the quat dot-product angle) and `heading` (magnetic, via
    `absolute_heading`) are convention-INDEPENDENT -- they mean the same thing
    regardless of the selected decomposition mode, so they are always tracked
    and are the trustworthy signals when comparing across a mode switch.
    `roll`/`pitch`/`yaw`, by contrast, are whatever the ACTIVE mode's slots
    report (owner ask, 2026-07-28: "jitter must follow the selected mode") --
    on a mode change those three are reset (history purged, not just the
    running `_prev_*`) so a diff is never taken across two incompatible
    labelings of the same rotation."""

    def __init__(self, window_s: float = SENSOR_JITTER_WINDOW_S):
        self.window_s = float(window_s)
        self._samples: deque[tuple[float, dict[str, float]]] = deque()
        self._prev_quat: tuple[float, float, float, float] | None = None
        self._prev_roll: float | None = None
        self._prev_pitch: float | None = None
        self._prev_yaw: float | None = None
        self._prev_heading: float | None = None
        self._mode: str = "zyx"

    def update(self, quat, heading_deg: float | None, now: float | None = None,
               mode: str = "zyx", roll_deg: float | None = None,
               pitch_deg: float | None = None, yaw_deg: float | None = None) -> dict:
        """Feed the newest RAW quat (+ full-precision heading, or None before
        env/mag data arrives). `roll_deg`/`pitch_deg`/`yaw_deg`, when given,
        are the ACTIVE `mode`'s decomposition of `quat` (from
        `orientation_view`); omitted, they default to the ZYX Tait-Bryan
        values (`quat_roll_deg` etc.) for backward compatibility with direct
        callers that don't care about mode. Returns `{"window_s": ..,
        <signal>: {mean_deg, p95_deg, n}, ...}` for
        roll/pitch/yaw/heading/orientation."""
        now = time.monotonic() if now is None else now
        if mode != self._mode:
            # Mode switch: the numeric MEANING of roll/pitch/yaw just changed,
            # so a frame-to-frame diff spanning the switch is nonsense -- purge
            # only those three signals (orientation/heading are mode-agnostic
            # and stay valid) from both the running "previous value" state and
            # the buffered window.
            self._samples = deque(
                (t, {k: v for k, v in d.items() if k not in ("roll", "pitch", "yaw")})
                for t, d in self._samples)
            self._prev_roll = self._prev_pitch = self._prev_yaw = None
            self._mode = mode
        diffs: dict[str, float] = {}
        if quat is not None:
            quat = tuple(float(v) for v in quat)
            roll = quat_roll_deg(quat) if roll_deg is None else float(roll_deg)
            pitch = quat_pitch_deg(quat) if pitch_deg is None else float(pitch_deg)
            yaw = quat_yaw_deg(quat) if yaw_deg is None else float(yaw_deg)
            if self._prev_roll is not None:
                diffs["roll"] = abs(wrap180(roll - self._prev_roll))
                diffs["pitch"] = abs(wrap180(pitch - self._prev_pitch))
                diffs["yaw"] = abs(wrap180(yaw - self._prev_yaw))
            self._prev_roll, self._prev_pitch, self._prev_yaw = roll, pitch, yaw
            if self._prev_quat is not None:
                diffs["orientation"] = quat_angle_deg(_unit_quat(self._prev_quat), _unit_quat(quat))
            self._prev_quat = quat
        if heading_deg is not None:
            if self._prev_heading is not None:
                diffs["heading"] = abs(wrap180(heading_deg - self._prev_heading))
            self._prev_heading = float(heading_deg)
        if diffs:
            self._samples.append((now, diffs))
        cutoff = now - self.window_s
        while self._samples and self._samples[0][0] < cutoff:
            self._samples.popleft()
        out = _jitter_stats([d for _, d in self._samples])
        out["window_s"] = self.window_s
        return out

    def reset(self) -> None:
        """Purge the whole window + every running "previous value" (issue
        #101): a source switch must not let the last frame of the OLD source
        be diffed against the first frame of the NEW one, which would report
        a huge, meaningless one-off jitter spike."""
        self._samples.clear()
        self._prev_quat = None
        self._prev_roll = self._prev_pitch = self._prev_yaw = None
        self._prev_heading = None


def select_colors(outputs: dict, deproj: Deprojector, color_mode: str,
                  colormap: str = "turbo"):
    """Deproject depth and colorize by the selected plane (§7.2).

    Returns (pts, colors, fell_back): pts (N,3) float32 metres, colors (N,3)
    float32 in [0,1], and fell_back True iff the requested non-depth plane was
    missing this frame and depth coloring was substituted. Coloring reuses the
    validity mask (finite, >0, < max_range) + min-max normalize + turbo/gray,
    exactly as the classic viewer. `color_mode == "depth"` colors by deprojected Z.
    """
    depth = outputs["depth"]
    pts = deproj(depth)
    fell_back = False
    if len(pts) == 0:
        empty = np.zeros((0, 3), dtype=np.float32)
        return empty, empty, False

    if color_mode == "depth":
        vals = pts[:, 2].astype(np.float64, copy=False)
    else:
        plane = outputs.get(color_mode)
        if plane is None:
            fell_back = True
            vals = pts[:, 2].astype(np.float64, copy=False)
        else:
            valid = np.isfinite(depth) & (depth > 0.0) & (depth < deproj.max_range_mm)
            vals = plane[valid].astype(np.float64, copy=False)

    vn = (vals - vals.min()) / max(float(np.ptp(vals)), 1e-6)
    colors = _apply_colormap(vn, colormap)
    return pts.astype(np.float32, copy=False), colors.astype(np.float32, copy=False), fell_back


def pack_point_cloud(pts: np.ndarray, colors: np.ndarray) -> bytes:
    """POINT_CLOUD binary (tag 1): u32 tag=1 · f32[3N] positions · f32[3N]
    colors, all little-endian. Positions then colors, concatenated (§6.1)."""
    pos = np.ascontiguousarray(pts, dtype="<f4").ravel()
    col = np.ascontiguousarray(colors, dtype="<f4").ravel()
    return struct.pack("<I", TAG_POINT_CLOUD) + pos.tobytes() + col.tobytes()


def select_surface(outputs: dict, deproj: Deprojector, color_mode: str,
                   colormap: str = "turbo", surface_mode: str = "grid",
                   threshold_pct: float = 4.0):
    """Grid-structured coloring + triangulation for surface mode.

    Returns (pts_grid, colors_grid, valid, triangles, covered, fell_back):
    pts_grid (h,w,3) f32, colors_grid (h,w,3) f32, valid (h,w) bool,
    triangles (T,3) int64, covered (h*w,) bool, fell_back bool."""
    from .surface import grid_triangles, grid_triangles_3d

    depth = outputs["depth"]
    pts_grid, valid = deproj.grid(depth)
    fell_back = False

    if color_mode == "depth":
        vals = pts_grid[..., 2]
    else:
        plane = outputs.get(color_mode)
        if plane is None:
            fell_back = True
            vals = pts_grid[..., 2]
        else:
            vals = plane.astype(np.float64, copy=False)

    valid_vals = vals[valid]
    if valid_vals.size > 0:
        lo, hi = float(valid_vals.min()), float(valid_vals.max())
    else:
        lo, hi = 0.0, 1.0
    rng = max(hi - lo, 1e-6)
    vn = np.clip((vals - lo) / rng, 0.0, 1.0)
    colors_grid = _apply_colormap(vn, colormap)
    colors_grid[~valid] = 0.0

    if surface_mode == "spatial":
        mean_z = float(np.mean(pts_grid[valid, 2])) if np.any(valid) else 1.0
        threshold_m = max((threshold_pct / 100.0) * mean_z, 1e-6)
        triangles, covered = grid_triangles_3d(pts_grid, valid, threshold_m)
    else:
        triangles, covered = grid_triangles(pts_grid, valid, threshold_pct)

    return (pts_grid.astype(np.float32, copy=False),
            colors_grid.astype(np.float32, copy=False),
            valid, triangles, covered, fell_back)


def pack_surface_cloud(pts_grid: np.ndarray, colors_grid: np.ndarray,
                       valid: np.ndarray, triangles: np.ndarray,
                       covered: np.ndarray) -> bytes:
    """SURFACE binary (tag 4): grid-ordered positions + colors + triangle mesh.

    Layout: u32 tag=4 · u16 w · u16 h · u32 n_tris ·
    f32[3*W*H] positions · f32[3*W*H] colors · u8[W*H] valid ·
    u32[3*T] tri_indices · u8[W*H] covered."""
    h, w = pts_grid.shape[:2]
    n_tris = len(triangles)
    pos = np.ascontiguousarray(pts_grid.reshape(-1, 3), dtype="<f4").ravel()
    col = np.ascontiguousarray(colors_grid.reshape(-1, 3), dtype="<f4").ravel()
    val = np.ascontiguousarray(valid.ravel(), dtype=np.uint8)
    tri = (np.ascontiguousarray(triangles.ravel(), dtype="<u4")
           if n_tris > 0 else np.array([], dtype="<u4"))
    cov = np.ascontiguousarray(covered, dtype=np.uint8)
    header = struct.pack("<IHHI", TAG_SURFACE, w, h, n_tris)
    return (header + pos.tobytes() + col.tobytes() + val.tobytes()
            + tri.tobytes() + cov.tobytes())


def pack_ir_image(rgb: np.ndarray) -> bytes:
    """IR_IMAGE binary (tag 2): u32 tag=2 · u16 width · u16 height ·
    u8[width*height*3] RGB, little-endian. width/height read from the array
    shape (H, W, 3) (§6.1)."""
    arr = np.ascontiguousarray(rgb, dtype=np.uint8)
    height, width = arr.shape[0], arr.shape[1]
    return struct.pack("<IHH", TAG_IR_IMAGE, width, height) + arr.tobytes()


def pack_mesh(packet) -> bytes:
    """MESH binary (tag 3): a SLAM `MeshPacket` (slam/meshprep.py) flattened to
    one self-describing little-endian frame (web Phase 4, docs/web-protocol.md).

    Counts up front so the client allocates once; then non-wall (verts f32·3,
    colors f32·3, tris u32·3), wall (same), floor (verts f32·3, lines u32·2).
    Positions/colors cast f64->f32; indices to u32. `flags` bit0=decimated,
    bit1=walls_split (a split packet carries a non-empty wall submesh)."""
    nw_v = np.ascontiguousarray(packet.non_wall_verts, dtype="<f4").ravel()
    nw_c = np.ascontiguousarray(packet.non_wall_colors, dtype="<f4").ravel()
    nw_t = np.ascontiguousarray(packet.non_wall_tris, dtype="<u4").ravel()
    w_v = np.ascontiguousarray(packet.wall_verts, dtype="<f4").ravel()
    w_c = np.ascontiguousarray(packet.wall_colors, dtype="<f4").ravel()
    w_t = np.ascontiguousarray(packet.wall_tris, dtype="<u4").ravel()
    f_v = np.ascontiguousarray(packet.floor_pts, dtype="<f4").ravel()
    f_l = np.ascontiguousarray(packet.floor_lines, dtype="<u4").ravel()

    flags = (1 if packet.decimated else 0) | (2 if packet.wall_mode == "split" else 0)
    header = struct.pack(
        "<IIIIIIIII", TAG_MESH, int(packet.mesh_seq), flags,
        len(packet.non_wall_verts), len(packet.non_wall_tris),
        len(packet.wall_verts), len(packet.wall_tris),
        len(packet.floor_pts), len(packet.floor_lines))
    return (header + nw_v.tobytes() + nw_c.tobytes() + nw_t.tobytes()
            + w_v.tobytes() + w_c.tobytes() + w_t.tobytes()
            + f_v.tobytes() + f_l.tobytes())


def _packed_or_pack(packet) -> bytes | None:
    """MESH bytes for a packet, preferring the ones `MeshPrep` already produced
    on its own thread (BUG-060). Packing is O(map) numpy work; doing it here, on
    the broadcaster, put that straight on the asyncio event loop. Falls back to
    packing inline for a MeshPrep built without a `packer` (tests, and any
    caller that hasn't opted in)."""
    if packet is None:
        return None
    return packet.packed if packet.packed is not None else pack_mesh(packet)


def build_slam_message(step, trajectory, *, frames_integrated: int, mesh_seq: int,
                       source_vertex_count: int, device: str | None = None,
                       backend: str | None = None,
                       frames_submitted: int | None = None,
                       frames_processed: int | None = None,
                       frames_overwritten: int | None = None,
                       mesh_extract_ms: float | None = None,
                       mesh_prep_ms: float | None = None,
                       mesh_pack_ms: float | None = None,
                       mesh_payload_bytes: int | None = None,
                       gpu: dict | None = None) -> dict:
    """FrameStep + trajectory -> `slam` JSON (web Phase 4). Follow-camera
    eye/center/up are computed server-side (reader.follow_camera_target) per the
    web-protocol "server-side math stays server-side" rule -- the browser just
    places its camera. `traj_tail` is downsampled to <=_TRAJ_TAIL_MAX positions
    so the JSON stays small on a long scan; `traj_len` carries the true length.

    `ts` (wall-clock seconds) lets the client measure its own pose age
    (`slamAgeS`, BUG-061) without trusting frame arrival timing. `device` is
    the resolved SLAM compute device (e.g. "CUDA:0", BUG-061 Part B -- GPU use
    was previously visible only in a log line); null/omitted when no worker
    has been built yet.

    Plan item 2 (2026-08-02, "Counters and stage timing"), all optional/None
    when the caller doesn't have them (an older worker, or nothing built yet):
      - `backend`: "local" (in-process Mapper) or "remote" (SlamService).
      - `frames_submitted`/`frames_processed`/`frames_overwritten`: the
        worker's latest-wins input-slot counters. An overwritten frame NEVER
        reached `Mapper.step` -- do not confuse it with `tracking_lost`,
        which is a frame that DID reach the mapper and failed to register
        (see SlamWorker.frames_overwritten's docstring).
      - `raycast_ms`/`icp_ms`/`integrate_ms` (from `step`, not a param here):
        per-stage timing. `raycast_ms`/`icp_ms` are real elapsed time on any
        device (both stages already force a device->host sync internally);
        `integrate_ms` is usually a DISPATCH-time lower bound on CUDA, not
        kernel-completion time -- see FrameStep's docstring, and do not read
        it as "this many ms of GPU work" without checking whether a sync
        happened to coincide (BLOCK_USAGE_INTERVAL/rehash-headroom checks).
      - `mesh_extract_ms`/`mesh_prep_ms`/`mesh_pack_ms`/`mesh_payload_bytes`:
        the throttled mesh pipeline's own stage costs. Extraction time IS a
        real sync on any device (TsdfMap._extract always returns host-
        resident). These only change on ticks where a fresh mesh was
        actually produced; the JSON still repeats the last-known values on
        every other tick, same pattern as `blocks_used`.
      - `gpu`: optional dict with `gpu_util_pct`/`gpu_util_scope`/
        `vram_used_bytes`/`vram_total_bytes`/`vram_scope` -- see
        `_slam_gpu_fields`. All device-wide (this box has no per-process
        `pynvml`); device-wide utilization proves *some* CUDA kernel ran on
        the card, not that SLAM's kernel did."""
    pose = np.asarray(step.pose, dtype=np.float64)
    eye, center, up = follow_camera_target(pose)
    n = len(trajectory)
    if n > _TRAJ_TAIL_MAX:
        idx = np.linspace(0, n - 1, _TRAJ_TAIL_MAX).astype(int)
        tail = [trajectory[i] for i in idx]
    else:
        tail = trajectory
    traj_tail = [[round(float(p[0, 3]), 4), round(float(p[1, 3]), 4), round(float(p[2, 3]), 4)]
                 for p in tail]
    return {
        "type": "slam",
        "ts": time.time(),
        "pose": [round(float(v), 5) for v in pose.reshape(-1)],   # row-major 16
        "follow": {"eye": [round(float(v), 4) for v in eye],
                   "center": [round(float(v), 4) for v in center],
                   "up": [round(float(v), 4) for v in up]},
        "traj_tail": traj_tail,
        "traj_len": n,
        "fitness": round(float(step.fitness), 4),
        "rmse": round(float(step.rmse), 5),
        "tracking_lost": bool(step.tracking_lost),
        "slam_ms": round(float(step.slam_ms), 2),
        "frames_integrated": int(frames_integrated),
        "mesh_seq": int(mesh_seq),
        "mesh_verts": int(source_vertex_count),
        # TSDF block-grid occupancy (BUG-035), sampled at ~4 Hz inside the
        # mapper -- `block_usage()` is a device sync on CUDA. Null before the
        # first sample, or from a worker that predates the gauge; the client
        # renders that as unknown rather than as an empty map.
        "blocks_used": _opt_int(getattr(step, "blocks_used", None)),
        "blocks_capacity": _opt_int(getattr(step, "blocks_capacity", None)),
        "blocks_configured": _opt_int(getattr(step, "blocks_configured", None)),
        "device": device,
        "backend": backend,
        # Stage timing straight off `step` -- see the docstring above for
        # which of these are sync-forced (real) vs. dispatch-only on CUDA.
        "raycast_ms": round(float(getattr(step, "raycast_ms", 0.0)), 3),
        "icp_ms": round(float(getattr(step, "icp_ms", 0.0)), 3),
        "integrate_ms": round(float(getattr(step, "integrate_ms", 0.0)), 3),
        "frames_submitted": _opt_int(frames_submitted),
        "frames_processed": _opt_int(frames_processed),
        "frames_overwritten": _opt_int(frames_overwritten),
        "mesh_extract_ms": (None if mesh_extract_ms is None
                            else round(float(mesh_extract_ms), 2)),
        "mesh_prep_ms": None if mesh_prep_ms is None else round(float(mesh_prep_ms), 2),
        "mesh_pack_ms": None if mesh_pack_ms is None else round(float(mesh_pack_ms), 2),
        "mesh_payload_bytes": _opt_int(mesh_payload_bytes),
        "gpu": gpu,
    }


def _opt_int(v) -> int | None:
    return None if v is None else int(v)


def sanitize_result_name(name, results_dir) -> Path | None:
    """A results filename from the client -> a safe existing path, or None.
    Basename only, `.ply`/`.tum` allow-list, must exist under results_dir
    (same discipline as sanitize_capture_name)."""
    if not name or not isinstance(name, str):
        return None
    base = Path(name).name
    if base != name or Path(name).suffix not in (".ply", ".tum"):
        return None
    p = Path(results_dir) / base
    return p if p.is_file() else None


def list_results(results_dir) -> list[dict]:
    """`results/*.ply` as {name, bytes, mtime}, newest first (the saved-maps
    library; mirrors list_captures)."""
    d = Path(results_dir)
    if not d.is_dir():
        return []
    items = []
    for p in sorted(d.glob("*.ply")):
        try:
            st = p.stat()
        except OSError:
            continue
        items.append({"name": p.name, "bytes": st.st_size, "mtime": round(st.st_mtime, 1)})
    items.sort(key=lambda x: x["mtime"], reverse=True)
    return items


def build_saved_message(results_dir) -> dict:
    return {"type": "saved", "items": list_results(results_dir)}


def _device_gpu_util() -> dict | None:
    """Device-wide GPU utilization fallback (BUG-061 Part B) via the ctypes
    NVML wrapper in `roomscan.slam.gpumem` -- the only utilization number
    available on this host, since `probe_gpu_process` (metrics.py) needs
    `pynvml` (absent) for a per-process figure. Imported lazily and
    defensively: another change lands `device_utilization()` concurrently
    with this one, so it may not exist yet, and this must never be the reason
    a `metrics` message fails to build."""
    try:
        from .slam.gpumem import device_utilization
    except (ImportError, AttributeError):
        return None
    try:
        return device_utilization()
    except Exception:
        return None


def _slam_gpu_fields(res) -> dict:
    """GPU/VRAM fields for the `slam` message (plan item 2, 2026-08-02),
    sourced from the SAME cached `ResourceSnapshot` the `metrics` message
    uses (`res`, a `ResourceSnapshot | None`) -- no extra NVML query is made
    on the SLAM poll path, which runs at the broadcaster's ~30 Hz tick and
    must not add its own device-sync cost (see `TsdfMap.block_usage`'s
    docstring on why that gauge is throttled).

    `vram_used_bytes`/`vram_total_bytes` come from `res.device_vram_*`, which
    `ResourceSnapshot`'s own docstring guarantees is DEVICE-wide (every
    process on the card, not just this one) -- `vram_scope` says so
    explicitly rather than leaving it to be inferred from the field name.
    `gpu_util_pct` mirrors `res.gpu_util`, whose scope is NOT fixed: it is
    `res.gpu_source` ("pynvml" = per-process, when that optional dependency
    is installed; "nvml-device" = the ctypes NVML device-wide fallback used
    on this box, which has no pynvml; "n/a" = no NVML at all) --
    `gpu_util_scope` carries that straight through so a caller never assumes
    "device-wide" when it might actually be per-process. Either way: a
    device-wide reading proves *some* CUDA kernel ran on the card, never
    that SLAM's did (a second CUDA process moves this number too)."""
    if res is None:
        return {"gpu_util_pct": None, "gpu_util_scope": None,
                "vram_used_bytes": None, "vram_total_bytes": None,
                "vram_scope": "device-wide"}
    return {
        "gpu_util_pct": None if res.gpu_util is None else round(float(res.gpu_util), 1),
        "gpu_util_scope": res.gpu_source,
        "vram_used_bytes": res.device_vram_used,
        "vram_total_bytes": res.device_vram_total,
        "vram_scope": "device-wide",
    }


def resources_to_dict(res) -> dict | None:
    """ResourceSnapshot -> the `metrics.resources` JSON object, or None.

    Raw numbers only (bytes, percent); the frontend formats them, same rule as
    the rest of the `metrics` message. Both scopes ride together because the
    owner's question -- "am I approaching a RAM/VRAM/GPU/CPU limit?" -- needs
    the ceiling, which is a property of the box, not of this process. Every
    field except the two the sampler always has (`proc_*`) can be null: no
    GPU, no NVML, or a psutil error all report absence rather than a zero that
    reads as a measurement (the trap in the verify-the-knob memory).

    This is deliberately a pure projection of the background sampler's cached
    snapshot. In particular it performs no NVML call: on this host opening and
    querying NVML costs about 40 ms, and doing that here used to block the
    asyncio broadcaster every 4 Hz metrics tick (#197). `ResourceSampler`
    applies the device-wide fallback on its own thread; the per-process figure,
    when present, still wins.
    """
    if res is None:
        return None
    return {
        "proc_cpu_percent": round(float(res.proc_cpu_percent), 1),
        "n_cores": int(res.n_cores),
        "proc_rss": int(res.proc_rss),
        "ram_total": int(res.ram_total),
        "ram_used": None if res.ram_used is None else int(res.ram_used),
        "sys_cpu_percent": (None if res.sys_cpu_percent is None
                            else round(float(res.sys_cpu_percent), 1)),
        "gpu_util": None if res.gpu_util is None else round(float(res.gpu_util), 1),
        "proc_vram": None if res.proc_vram is None else int(res.proc_vram),
        "vram_total": None if res.vram_total is None else int(res.vram_total),
        "gpu_name": res.gpu_name,
        "gpu_source": res.gpu_source,
        "device_vram_used": (None if res.device_vram_used is None
                             else int(res.device_vram_used)),
        "device_vram_total": (None if res.device_vram_total is None
                              else int(res.device_vram_total)),
        "device_vram_source": getattr(res, "device_vram_source", "n/a"),
    }


def build_metrics_message(snapshot: MetricsSnapshot) -> dict:
    """MetricsSnapshot -> `metrics` JSON dict (§6.2). Numeric fields go raw over
    the wire, the frontend formats. device_hz/jitter_ms may be None -> JSON null.

    `resources` is null until a `ResourceSampler` has published its first sample
    (it is constructed and started in `main()`, and passed to the
    `MetricsRegistry`, whose `snapshot()` folds it in); it stays null forever on
    a state built without one, e.g. in tests."""
    return {
        "type": "metrics",
        "render_fps": float(snapshot.render_fps),
        # Task 9 (2026-08-03): the transform's own completion rate, uncapped
        # by the ~30 Hz presentation loop above -- at a 30 Hz source the two
        # agree; a divergence at a higher source rate is deliberate
        # presentation decimation, not loss. See MetricsSnapshot's docstring.
        "transform_fps": float(snapshot.transform_fps),
        # Literal count of point-cloud sends -- see tick_browser's docstring
        # for why this differs from render_fps in non-point_cloud display.
        "browser_fps": float(snapshot.browser_fps),
        "streams": [
            {
                "stream_id": s.stream_id,
                "label": s.label,
                "device_hz": s.device_hz,
                "host_hz": s.host_hz,
                "bytes_per_s": s.bytes_per_s,
                "jitter_ms": s.jitter_ms,
            }
            for s in snapshot.streams
        ],
        "link_bytes_per_s": float(snapshot.link_bytes_per_s),
        "resources": resources_to_dict(snapshot.resources),
        "drops": snapshot.drops,
        "gaps": snapshot.gaps,
    }


_FUSION_LABELS = {
    "off": "Off",
    "init": "Initializing",
    "active": "Active",
    "gated:no-cal": "No mag calibration",
    "gated:motion": "Fast motion",
    "gated:anomaly": "Mag anomaly",
    "gated:no-field": "No horizontal field",
    "gated:invalid-mag": "Invalid mag sample",
}


def build_sensor_message(sensor_state: SensorState, mag_cal: MagCalibration | None,
                          jitter: OrientationJitter | None = None,
                          orientation_mode: str = "zyx",
                          axis_labels=DEFAULT_AXIS_LABELS,
                          yaw_offset_deg: float = 0.0,
                          ir_display_quat=None,
                          msl_pa: float | None = None,
                          msl_source: str = "fallback",
                          msl_age_s: float | None = None,
                          elevation_datum_ft: float | None = None,
                          altitude_smoother: "ElevationSmoother | None" = None,
                          tof_meta: dict | None = None) -> dict | None:
    """SensorState -> `sensor` JSON dict (streams 9/10), or None when there is no
    sensor data at all (so the broadcaster stays silent on a ToF-only session).

    The load-bearing math is reused verbatim from the desktop panel: the gizmo
    `rot` is the same display rotation `gizmo_pose` builds
    (T_WORLD_TO_CV @ R @ T_CV_TO_BODY, sensors.py:183-192), and `heading` is
    `absolute_heading` over the calibrated mag (panel.py:3172-3178). Computing
    them here keeps the sign/permutation matrices in exactly one place (Python),
    so the frontend never re-derives them.

    `orientation_raw` and `jitter` are additive fields (owner ask, 2026-07-28):
    the RAW numeric orientation (quat + Euler + heading, un-rounded relative to
    `rot`/`heading` above -- those are rounded for the wire and would censor
    the very noise `jitter` measures) and rolling-window frame-to-frame jitter
    stats (mean_deg/p95_deg/n) for roll/pitch/yaw/heading/orientation. Both are
    computed off `sensor_state.fused_quat()` -- pre-`OrientationSmoother`, the
    same raw signal SLAM sees -- never off the smoothed display quat, so they
    read real sensor noise. `jitter` is None-safe: pass no tracker (e.g. from a
    test) and every signal reports `n=0` / `None` stats rather than raising.

    `orientation_view` (owner ask, 2026-07-28) adds the SELECTED decomposition
    mode's own take on the same quat -- ZYX Tait-Bryan by default (identical
    numbers to `orientation_raw`), or an alternate Euler sequence / boresight
    az-el-roll / gravity+mag "world" reference when `orientation_mode` picks
    one (see `orientation_view()` and `sensors.py`'s "Alternate orientation
    decompositions" section for the math + where each mode's singularity
    sits). `axis_labels` are carried through verbatim for the frontend to use
    instead of hardcoded "Roll"/"Pitch"/"Yaw" strings. This is purely
    presentation: `orientation_raw`/`rot`/`heading` above are computed exactly
    as before, unaffected by `orientation_mode`.

    `yaw_offset_deg` ("Zero yaw here", owner ask, 2026-07-29) is a further
    presentation-only graft applied ONLY to the decomposition fed into
    `orientation_view` -- never to `quat` itself, so `rot`/`heading`/
    `orientation_raw`/`jitter`'s "orientation" signal above are computed from
    the untouched quat exactly as before. It is applied via `graft_yaw`
    (a world-Z rotation that provably preserves roll/pitch/tilt -- see its
    docstring) rather than by adding/subtracting degrees from a Euler
    component, so the decomposition it feeds is still a valid rotation. It is
    skipped entirely for World mode: that mode's `yaw_deg` is the absolute
    magnetic `heading_full` computed above, not a function of this graft, so
    applying it would be a no-op at best and confusing at worst -- the skip
    just documents that explicitly. A constant offset cancels exactly in any
    frame-to-frame diff, so `jitter`'s roll/pitch/yaw magnitudes are
    unaffected by it (see `test_yaw_offset_does_not_change_jitter_magnitude`).

    `elevation_ft` / `pressure_hpa` / `msl_*` (owner ask, 2026-07-31) turn the
    raw Pascals into the number a person actually reads: elevation above sea
    level, in feet. The altitude is `slam.frames.baro_height_m` -- the SAME
    barometric formula SLAM uses, never a second one -- evaluated against
    `msl_pa`, the current sea-level reference `weather.py` fetches. Whether
    that reference is real is REPORTED (`msl_source`), not hidden: with no
    internet it is 101325 Pa and the absolute elevation can be a couple of
    hundred feet off, while the *change* since a datum stays correct either
    way (a constant reference cancels in a difference). `altitude_smoother`
    low-passes the readout -- BUG-037 measured ~267 mm RMS of white noise per
    barometer sample (~1.2 ft), so the raw number is unreadable; pass None and
    you get the raw instantaneous altitude. `elevation_hist` is derived from
    the same decimated pressure history the sparkline already draws, so the
    trace and the readout are the same quantity in the same units.
    """
    quat = sensor_state.fused_quat()
    env = sensor_state.latest_env()
    press_spark = sensor_state.pressure_spark_history()
    temp_spark = sensor_state.temp_spark_history()
    if quat is None and env is None and press_spark.size == 0:
        return None

    rot = None
    r = display_rotation(quat)
    if r is not None:
        rot = [round(float(v), 5) for v in r.reshape(-1)]   # row-major 9

    heading = None
    heading_full = None
    mag_out = None
    if env is not None:
        mag = env.mag_ut
        if mag_cal is not None:
            mag = tuple(float(v) for v in AXIS_CONVENTION @ mag_cal.apply(mag))
        mag_out = [round(float(v), 2) for v in mag]
        if quat is not None:
            # None where a boresight bearing does not exist -- aimed within 10
            # deg of straight up/down (BUG-058). The client already renders a
            # null heading as "—"; World mode reports the reason below.
            heading_full = absolute_heading(quat, tuple(mag))
            heading = round(heading_full, 1) if heading_full is not None else None

    orientation_raw = {
        "quat": [round(float(v), 6) for v in quat] if quat is not None else None,
        "roll_deg": round(quat_roll_deg(quat), 4) if quat is not None else None,
        "pitch_deg": round(quat_pitch_deg(quat), 4) if quat is not None else None,
        "yaw_deg": round(quat_yaw_deg(quat), 4) if quat is not None else None,
        "heading_deg": round(heading_full, 4) if heading_full is not None else None,
    }

    mode = orientation_mode if orientation_mode in _VALID_ORIENTATION_MODES else "zyx"
    # "Zero yaw here": graft the user's offset onto a DISPLAY-ONLY copy of the
    # quat, never `quat` itself -- World mode is excluded, its yaw slot is the
    # absolute `heading_full` above, not a function of this quat's yaw.
    display_quat = quat
    if quat is not None and mode != "world" and yaw_offset_deg:
        display_quat = graft_yaw(quat, float(yaw_offset_deg))
    view = orientation_view(mode, display_quat,
                             mag_ut_raw=(env.mag_ut if env is not None else None),
                             heading_full=heading_full, mag_cal=mag_cal,
                             imu_raw_batch=sensor_state.latest_imu_raw())
    orientation_view_out = {
        **{k: (round(v, 4) if isinstance(v, float) else v) for k, v in view.items()},
        "mode": mode,
        "labels": list(axis_labels),
        # Echoed for the frontend to show/hide "Clear offset" -- 0.0 (not the
        # raw setting) whenever mode == "world", since it never applied there.
        "yaw_offset_deg": round(float(yaw_offset_deg), 2) if mode != "world" else 0.0,
    }

    jitter_out = (jitter.update(quat, heading_full, mode=mode, roll_deg=view["roll_deg"],
                                 pitch_deg=view["pitch_deg"], yaw_deg=view["yaw_deg"])
                  if jitter is not None
                  else _jitter_stats([]) | {"window_s": SENSOR_JITTER_WINDOW_S})

    # --- elevation (owner ask, 2026-07-31) ---------------------------------
    # One barometric formula in the whole project: slam.frames.baro_height_m.
    # `msl_ref` is the sea-level reference; falling back to the ICAO standard
    # atmosphere is a real answer (the Delta datum still works against it), it
    # just gets reported as such via `msl_source`.
    msl_ref = float(msl_pa) if msl_pa else FALLBACK_MSL_PA
    pressure_pa = float(env.pressure_pa) if env is not None else None
    altitude_raw_m = baro_height_m(pressure_pa, msl_ref) if pressure_pa else None
    altitude_m = (altitude_smoother.update(altitude_raw_m)
                  if altitude_smoother is not None else altitude_raw_m)
    elevation_ft = None if altitude_m is None else round(altitude_m * FT_PER_M, 1)
    # Same decimated samples the pressure sparkline uses, converted so the
    # trace and the readout are in one unit. Unsmoothed on purpose: the
    # sparkline's job is to show the noise band and the trend, and it is
    # min/max autoscaled anyway.
    elevation_hist = [round(baro_height_m(float(p), msl_ref) * FT_PER_M, 1)
                      for p in press_spark.tolist() if p]

    raw_status = sensor_state.fusion_status()
    return {
        "type": "sensor",
        "have_quat": quat is not None,
        "rot": rot,
        "heading": heading,
        "pressure_pa": round(float(env.pressure_pa), 1) if env is not None else None,
        "temp_c": round(float(env.temp_c), 2) if env is not None else None,
        "mag_ut": mag_out,
        "fusion": _FUSION_LABELS.get(raw_status, raw_status),
        "fusion_key": raw_status,
        "has_mag_cal": mag_cal is not None,
        "pressure_hist": [round(float(v), 1) for v in press_spark.tolist()],
        "temp_hist": [round(float(v), 2) for v in temp_spark.tolist()],
        # Elevation readout. `pressure_pa`/`pressure_hist` above are KEPT (the
        # diagnostics drawer still shows the raw Pascals, and nothing that
        # already consumes them has to change).
        "elevation_ft": elevation_ft,
        "elevation_datum_ft": (None if elevation_datum_ft is None
                               else round(float(elevation_datum_ft), 1)),
        "elevation_hist": elevation_hist,
        "pressure_hpa": None if pressure_pa is None else round(pressure_pa / 100.0, 2),
        "msl_pa": round(msl_ref, 1),
        "msl_source": msl_source,
        "msl_age_s": None if msl_age_s is None else round(float(msl_age_s), 1),
        "elevation_tau_s": round(float(altitude_smoother.tau_s
                                       if altitude_smoother is not None else 0.0), 1),
        "orientation_raw": orientation_raw,
        "orientation_view": orientation_view_out,
        "jitter": jitter_out,
        # ToF per-frame metadata (decoded host-side from the RAW tail; None on a
        # ToF-frame-less tick). Diagnostics-drawer only.
        "tof_exposure_ms": (None if tof_meta is None or tof_meta.get("exposure_ms") is None
                            else round(float(tof_meta["exposure_ms"]), 2)),
        "tof_ranging_mode": None if tof_meta is None else tof_meta.get("ranging_mode"),
        "tof_die_temp_c": None if tof_meta is None else tof_meta.get("die_temp_c"),
        "tof_error": None if tof_meta is None else (tof_meta.get("error_status", 0) or tof_meta.get("error_code", 0)),
        "tof_dss_mode": None if tof_meta is None else tof_meta.get("dss_mode"),
        "tof_binning": None if tof_meta is None else tof_meta.get("binning"),
        "tof_fps": (None if tof_meta is None or tof_meta.get("fps") is None
                    else round(float(tof_meta["fps"]), 1)),
        # Residual in-plane roll the IR pane's server-side 90-deg snap leaves
        # behind, for the client to finish with a CSS transform (see
        # `ir_gravity_residual_deg`). CCW-positive, so CSS must negate it.
        # Computed from the SMOOTHED display quat -- the same one the snap uses --
        # or the two would disagree near a 45-deg boundary and the pane would jump.
        "ir_roll_deg": (None if ir_display_quat is None
                        else round(ir_gravity_residual_deg(ir_display_quat), 2)),
    }


def resolve_command(name: str, param) -> tuple[CommandCode, int, str] | None:
    """Inbound `cmd` request -> (CommandCode, param, label), or None for an
    unknown name. usecase carries the id as both param and label suffix."""
    if name == "ping":
        return CommandCode.PING, 0, "ping"
    if name == "calib":
        return CommandCode.SEND_CALIB, 0, "calib"
    if name == "reinit":
        return CommandCode.REINIT, 0, "reinit"
    if name == "usecase":
        uid = int(param)
        return CommandCode.SET_USECASE, uid, f"usecase {uid}"
    if name == "period":
        return CommandCode.SET_FRAME_PERIOD_US, int(param), f"period {int(param)}"
    if name == "exposure":
        return CommandCode.SET_EXPOSURE_MS, int(param), f"exposure {int(param)}"
    if name == "standby":
        level = int(param)
        return CommandCode.SET_STANDBY, level, f"standby {level}"
    return None


# --- Ranging profiles & manual sensor control (Task 10, high-framerate plan) ------
#
# Server-owned, device-authoritative state for SET_RANGING_PROFILE/SET_MANUAL_PARAMS/
# GET_RANGING_CONFIG (cmd 8/9/10, live+hardware-verified) and SET/GET_IMU_ENV_RATE
# (cmd 11/12, Task 7 -- firmware parses them but currently ACKs UNKNOWN_CMD; this
# layer reports that honestly instead of pretending a rate was ever confirmed).
#
# `roomscan.profiles` is the single pure owner of every number shown here (fps/
# exposure ranges, DSS/context rules, power/range/I3C-bus estimates); nothing below
# hardcodes a threshold or formula that module doesn't already own -- see its module
# docstring for the derivations. This module only bridges wire <-> profiles enums,
# drives the CommandClient off the event loop, and never commits `applied_*` state
# from anything but a successful device readback (a SET_RANGING_PROFILE ACK carries
# no config fields at all -- cmd 8 keeps the legacy 12-byte ACK shape -- so a
# successful preset switch is always followed by one GET_RANGING_CONFIG round trip;
# SET_MANUAL_PARAMS's own ACK already IS the readback, so manual needs no second
# trip).
#
# Enum<->wire-string bridges: reuses `roomscan.control`'s tested
# `_RANGING_MODE_TO_WIRE`/`_POWER_MODE_TO_WIRE` name-keyed tables (inverted here for
# the read direction) rather than a second copy -- that module's own docstring warns
# passing `.value` straight through silently sends the wrong ranging/power mode
# because the wire and profiles enums use different numbering.
_WIRE_TO_PROFILE_RANGING_MODE: dict[int, profiles.RangingMode] = {
    int(wire): prof for prof, wire in _RANGING_MODE_TO_WIRE.items()
}
_WIRE_TO_PROFILE_POWER_MODE: dict[int, profiles.PowerMode] = {
    int(wire): prof for prof, wire in _POWER_MODE_TO_WIRE.items()
}

# JSON vocabulary for the `ranging` message -- deliberately the same tokens
# `roomscan-ctl`'s CLI already uses (ambient/precision, ulp/lp/regular), not
# `IntEnum.name.lower()` (which would say "ultra_low" for power, disagreeing
# with the CLI's "ulp" for the identical value). Owned by `roomscan.profiles`
# so the browser and the MCP tools cannot drift apart; aliased here because
# this module's readers know these names.
_PROFILE_ID_TO_STR = profiles.PROFILE_ID_TO_STR
_STR_TO_PROFILE_ID = profiles.STR_TO_PROFILE_ID
_RANGING_MODE_TO_STR = profiles.RANGING_MODE_TO_STR
_STR_TO_RANGING_MODE = profiles.STR_TO_RANGING_MODE
_POWER_MODE_TO_STR = profiles.POWER_MODE_TO_STR
_STR_TO_POWER_MODE = profiles.STR_TO_POWER_MODE


@dataclass
class RangingState:
    """Server-owned authoritative ranging-profile state.

    The device is the single source of truth for `applied_*` -- populated only
    from a `GET_RANGING_CONFIG` readback or a successful `SET_RANGING_PROFILE`/
    `SET_MANUAL_PARAMS` readback (see `_refresh_ranging_state`/`_commit_ranging_ack`),
    never assumed from a firmware default and never set optimistically from a
    click. `requested_*` is what the LAST command asked for -- shown while a
    command is pending or after it fails -- and never feeds `estimate`/`applied_*`
    on its own.
    """
    transport: str = "none"                # "udp" | "cdc" | "replay" | "none"
    initialized: bool = False              # True once a real device readback has landed
    applied_profile_id: int | None = None       # profiles.ProfileId
    applied_ranging_mode: int | None = None      # profiles.RangingMode
    applied_fps: int | None = None
    applied_exposure_ms: int | None = None
    applied_power_mode: int | None = None        # profiles.PowerMode
    estimate: dict | None = None            # _estimate_to_json() of the applied config
    measured_fps: float | None = None       # metrics device_hz for the ToF stream
    requested_profile_id: int | None = None
    requested_manual: dict | None = None     # {"ranging_mode","fps","exposure_ms","power_mode"}
    pending: bool = False
    pending_kind: str | None = None          # "profile" | "manual" | None
    error: str | None = None                 # last command's failure; cleared on next success


@dataclass
class ImuEnvRateState:
    """Independent pending-command state for SET/GET_IMU_ENV_RATE (cmd 11/12,
    Task 7). Deliberately separate from `RangingState` -- plan Task 10 item 8:
    "a second, independent pending command, not a fifth field bolted onto
    Manual ranging". Firmware parses 11/12 but currently ACKs UNKNOWN_CMD
    (Task 7 not yet landed); this state reports that honestly and stays
    "coupled" rather than pretending a rate was ever confirmed."""
    initialized: bool = False
    applied_rate_hz: int | None = None       # None until a real readback; 0 = coupled
    requested_rate_hz: int | None = None
    pending: bool = False
    warning: str | None = None
    error: str | None = None
    # Task 8: stream 9 (IMU_QUAT)'s OWN measured cadence (metrics.py
    # `device_hz`, from capture timestamps -- true whether live or replayed).
    # This is the "replay truthfulness" fallback for `_applied_imu_env_rate_hz`
    # when there is no live profile target at all (a replay, or before the
    # device's first readback) -- never assume the ToF rate, and never assume
    # 30 Hz, for a recording that may have been made at a different rate.
    measured_quat_hz: float | None = None


def _transport_kind(ctrl) -> str:
    """"udp" | "cdc" | "replay" | "none" -- authoritative, never guessed client-side
    (global constraint: "the server knows its source ... surface it in state")."""
    if ctrl is None:
        return "none"
    if getattr(ctrl, "mode", None) == "replay":
        return "replay"
    underlying = getattr(ctrl, "_live_underlying", None)
    if isinstance(underlying, UdpSource):
        return "udp"
    if isinstance(underlying, SerialSource):
        return "cdc"
    return "none"


def _match_profile_id(ranging_mode: profiles.RangingMode, fps: int, exposure_ms: int,
                      power_mode: profiles.PowerMode) -> profiles.ProfileId:
    """A device readback carries only ranging_mode/frame_period_us/exposure_ms/
    power_mode -- no profile id -- so "which of the four buttons is this"
    is inferred by exact match against `profiles.PRESETS`; anything that
    doesn't match one is MANUAL, whether it was reached via SET_MANUAL_PARAMS
    or is simply a configuration no preset happens to describe."""
    for pid, cfg in profiles.PRESETS.items():
        if (cfg.ranging_mode == ranging_mode and cfg.fps == fps
                and cfg.exposure_ms == exposure_ms and cfg.power_mode == power_mode):
            return pid
    return profiles.ProfileId.MANUAL


def _profile_config_from_ack(ack: RangingConfigAck, imu_env_rate_hz: int | None) -> profiles.ProfileConfig:
    ranging_mode = _WIRE_TO_PROFILE_RANGING_MODE[ack.ranging_mode]
    power_mode = _WIRE_TO_PROFILE_POWER_MODE[ack.power_mode]
    fps = round(profiles.period_us_to_fps(ack.frame_period_us)) if ack.frame_period_us else 0
    profile_id = _match_profile_id(ranging_mode, fps, ack.exposure_ms, power_mode)
    return profiles.ProfileConfig(profile_id, ranging_mode, fps, ack.exposure_ms,
                                  power_mode, imu_env_rate_hz)


# The estimate's JSON shape is owned by `roomscan.profiles` too, so `ranging`
# (browser) and `profile_estimate()`/`rig_profile()` (MCP) cannot describe the
# same configuration differently.
_estimate_to_json = profiles.estimate_to_json


def _recompute_ranging_estimate(state) -> None:
    """Rebuild `RangingState.estimate` from the currently-known applied fields
    -- no device round trip. Called after either half (ranging or IMU/env)
    changes, so the estimate's `imu_env_rate_hz`/`imu_env_coupled` never goes
    stale relative to the OTHER card's last confirmed rate."""
    rs: RangingState = state.ranging_state
    if not rs.initialized or rs.applied_ranging_mode is None:
        return
    ie: ImuEnvRateState = state.imu_env_state
    config = profiles.ProfileConfig(
        profiles.ProfileId(rs.applied_profile_id), profiles.RangingMode(rs.applied_ranging_mode),
        rs.applied_fps, rs.applied_exposure_ms, profiles.PowerMode(rs.applied_power_mode),
        ie.applied_rate_hz)
    estimate = profiles.estimate_profile(config, transport=rs.transport)
    rs.estimate = _estimate_to_json(estimate)


def _commit_ranging_ack(state, ack: RangingConfigAck) -> None:
    """Commit `RangingState.applied_*` from a REAL device readback (either a
    `GET_RANGING_CONFIG` ACK or a successful `SET_MANUAL_PARAMS` ACK, which
    carries the identical config shape) -- the only path allowed to write
    these fields (global constraint: "Profile state is server-authoritative
    and changes only after a successful ACK containing device readback.
    No optimistic client state.")."""
    rs: RangingState = state.ranging_state
    ie: ImuEnvRateState = state.imu_env_state
    config = _profile_config_from_ack(ack, ie.applied_rate_hz)
    rs.applied_profile_id = int(config.profile_id)
    rs.applied_ranging_mode = int(config.ranging_mode)
    rs.applied_fps = config.fps
    rs.applied_exposure_ms = config.exposure_ms
    rs.applied_power_mode = int(config.power_mode)
    rs.initialized = True
    rs.error = None
    # Point the mode-aware flat-field at the device's now-confirmed ranging mode,
    # so Precision/Ambient get their own map. No-op for a single/legacy map.
    st = getattr(state, "stage", None)
    if st is not None:
        st.set_ranging_mode(rs.applied_ranging_mode)
    _recompute_ranging_estimate(state)


def _ranging_message(state) -> dict:
    rs: RangingState = state.ranging_state
    ie: ImuEnvRateState = state.imu_env_state
    applied = None
    if rs.initialized:
        applied = {
            "profile": (_PROFILE_ID_TO_STR.get(profiles.ProfileId(rs.applied_profile_id))
                       if rs.applied_profile_id is not None else None),
            "ranging_mode": (_RANGING_MODE_TO_STR.get(profiles.RangingMode(rs.applied_ranging_mode))
                             if rs.applied_ranging_mode is not None else None),
            "fps": rs.applied_fps,
            "exposure_ms": rs.applied_exposure_ms,
            "power_mode": (_POWER_MODE_TO_STR.get(profiles.PowerMode(rs.applied_power_mode))
                          if rs.applied_power_mode is not None else None),
        }
    return {
        "type": "ranging",
        "transport": rs.transport,
        "initialized": rs.initialized,
        "applied": applied,
        "measured_fps": round(rs.measured_fps, 2) if rs.measured_fps is not None else None,
        "estimate": rs.estimate,
        "requested": {
            "kind": rs.pending_kind,
            "profile": (_PROFILE_ID_TO_STR.get(profiles.ProfileId(rs.requested_profile_id))
                       if rs.requested_profile_id is not None else None),
            "manual": rs.requested_manual,
        },
        "pending": rs.pending,
        "error": rs.error,
        "imu_env": {
            "initialized": ie.initialized,
            "applied_rate_hz": ie.applied_rate_hz,
            "coupled": ie.applied_rate_hz in (None, 0),
            "requested_rate_hz": ie.requested_rate_hz,
            "pending": ie.pending,
            "warning": ie.warning,
            "error": ie.error,
        },
    }


async def _broadcast_ranging(state) -> None:
    await _broadcast_text(state.clients, json.dumps(_ranging_message(state)))


async def _refresh_ranging_state(state, retries: int = 0, retry_delay: float = 0.5) -> None:
    """`GET_RANGING_CONFIG` (cmd 10): the authoritative restore path -- called
    at startup/device-connect and after every successful preset switch.

    At launch the device can answer BUSY (or time out) for the first second or two
    while it finishes bringing ranging up over I3C, which surfaced as a stuck
    "Error: GET_RANGING_CONFIG -> BUSY" on the first applied-mode read (owner-reported
    2026-08-05). `retries` re-reads on BUSY/timeout with `retry_delay` between attempts
    so the launch settles onto the real config instead; a genuine protocol error is
    not retried. Post-switch callers pass retries=0 (single-shot, as before)."""
    rs: RangingState = state.ranging_state
    ctrl = getattr(state, "controller", None)
    client = getattr(state, "client", None)
    rs.transport = _transport_kind(ctrl)
    if client is None:
        return
    for attempt in range(retries + 1):
        last = attempt >= retries
        try:
            result, ack = await asyncio.to_thread(client.get_ranging_config)
        except TimeoutError as exc:
            rs.error = f"GET_RANGING_CONFIG timeout: {exc}"
            if not last:
                await asyncio.sleep(retry_delay)
                continue
            return
        except ProtocolError as exc:
            rs.error = f"GET_RANGING_CONFIG protocol error: {exc}"
            return
        if result != ResultCode.OK:
            rs.error = f"GET_RANGING_CONFIG -> {result.name}"
            if result == ResultCode.BUSY and not last:
                await asyncio.sleep(retry_delay)
                continue
            return
        rs.error = None
        _commit_ranging_ack(state, ack)
        return


async def _refresh_imu_env_state(state) -> None:
    """`GET_IMU_ENV_RATE` (cmd 12). Honest with today's firmware: cmd 12 parses
    but ACKs UNKNOWN_CMD (Task 7 not yet landed), so this reports that error and
    leaves `initialized` False rather than adopting a guessed "coupled" state."""
    ie: ImuEnvRateState = state.imu_env_state
    client = getattr(state, "client", None)
    if client is None:
        return
    try:
        result, applied = await asyncio.to_thread(client.get_imu_env_rate)
    except TimeoutError as exc:
        ie.error = f"GET_IMU_ENV_RATE timeout: {exc}"
        return
    except ProtocolError as exc:
        ie.error = f"GET_IMU_ENV_RATE protocol error: {exc}"
        return
    if result != ResultCode.OK:
        ie.error = f"GET_IMU_ENV_RATE -> {result.name}"
        return
    ie.applied_rate_hz = int(applied)
    ie.initialized = True
    ie.error = None
    _recompute_ranging_estimate(state)


async def _init_ranging_state(state) -> None:
    """One-shot startup restore (Task 10 item 1: "Initialize through
    GET_RANGING_CONFIG ... NOT an assumed firmware default"). A no-op, not an
    error, when there is no live device (replay-only launch)."""
    ctrl = getattr(state, "controller", None)
    rs: RangingState = state.ranging_state
    rs.transport = _transport_kind(ctrl)
    if getattr(state, "client", None) is None:
        return
    # Retry the launch read across the device's brief post-boot BUSY window so the
    # applied mode reads back instead of sticking on "GET_RANGING_CONFIG -> BUSY".
    await _refresh_ranging_state(state, retries=8, retry_delay=0.5)
    await _refresh_imu_env_state(state)
    await _broadcast_ranging(state)


async def _set_profile(state, profile_id: int) -> None:
    """Inbound `set_profile`. Presets are HOST-COMPOSED (2026-08-05): resolve the id to
    its `profiles.PRESETS` entry and apply it as ONE `SET_MANUAL_PARAMS` (cmd 9) plus
    the preset's IMU/env rate (cmd 11) -- NOT the wire `SET_RANGING_PROFILE` (cmd 8),
    whose firmware-resident table is fixed and cannot carry an IMU rate. The device
    readback is re-labelled back to the preset by `_match_profile_id`, so the UI still
    shows the preset as `applied`. MANUAL is driven by the manual panel, not here."""
    rs: RangingState = state.ranging_state
    try:
        pid = profiles.ProfileId(profile_id)
    except ValueError:
        log.warning("set_profile: unknown profile id %r", profile_id)
        return
    cfg = profiles.PRESETS.get(pid)
    if cfg is None:
        log.warning("set_profile: %s is not a composable preset", pid.name)
        return
    # Ranging half: validated host-side and device-confirmed by SET_MANUAL_PARAMS.
    await _set_manual_params(
        state,
        ranging_mode=profiles.RANGING_MODE_TO_STR[cfg.ranging_mode],
        fps=cfg.fps, exposure_ms=cfg.exposure_ms,
        power_mode=profiles.POWER_MODE_TO_STR[cfg.power_mode])
    # Only apply the IMU half if the ranging half actually landed: an error, or a
    # still-pending flag (the ranging command was rejected because another was in
    # flight), means we must not push an IMU change on top.
    if rs.error or rs.pending:
        return
    if cfg.imu_env_rate_hz is not None:
        await _set_imu_env_rate(state, int(cfg.imu_env_rate_hz))


async def _set_manual_params(state, *, ranging_mode, fps, exposure_ms, power_mode) -> None:
    """Inbound `set_manual_params`. Validates through `roomscan.profiles`
    first (so a rejected request never touches the device), then sends the
    WHOLE candidate as one atomic `SET_MANUAL_PARAMS` (cmd 9) -- never four
    independent operations. Commits `applied_*` straight from cmd 9's own
    ACK, which already IS the device readback."""
    rs: RangingState = state.ranging_state
    ctrl = getattr(state, "controller", None)
    client = getattr(state, "client", None)
    rs.transport = _transport_kind(ctrl)
    if client is None or rs.transport == "replay":
        rs.error = "ranging control unavailable in replay"
        await _broadcast_ranging(state)
        return
    if rs.pending:
        log.warning("set_manual_params: rejected -- a ranging command is already pending")
        return

    rm = _STR_TO_RANGING_MODE.get(ranging_mode)
    pm = _STR_TO_POWER_MODE.get(power_mode)
    if rm is None or pm is None or not isinstance(fps, int) or not isinstance(exposure_ms, int):
        log.warning("set_manual_params: invalid request ranging_mode=%r fps=%r exposure_ms=%r "
                   "power_mode=%r", ranging_mode, fps, exposure_ms, power_mode)
        rs.error = "invalid manual params request"
        await _broadcast_ranging(state)
        return

    rs.requested_profile_id = int(profiles.ProfileId.MANUAL)
    rs.requested_manual = {"ranging_mode": ranging_mode, "fps": fps,
                          "exposure_ms": exposure_ms, "power_mode": power_mode}
    rs.pending_kind = "manual"

    params = profiles.ManualParams(rm, fps, exposure_ms, pm)
    validation = profiles.validate_manual_params(params)
    if not validation.ok:
        rs.error = "; ".join(validation.errors)
        await _broadcast_ranging(state)
        return

    rs.pending = True
    rs.error = None
    await _broadcast_ranging(state)

    wire_params = _manual_params_to_wire(params)
    try:
        result, ack = await asyncio.to_thread(client.send_manual_params, wire_params)
    except TimeoutError as exc:
        rs.error = f"SET_MANUAL_PARAMS timeout: {exc}"
        rs.pending, rs.pending_kind = False, None
        await _broadcast_ranging(state)
        return
    except ProtocolError as exc:
        rs.error = f"SET_MANUAL_PARAMS protocol error: {exc}"
        rs.pending, rs.pending_kind = False, None
        await _broadcast_ranging(state)
        return
    if result != ResultCode.OK:
        rs.error = f"SET_MANUAL_PARAMS -> {result.name}"
        rs.pending, rs.pending_kind = False, None
        await _broadcast_ranging(state)
        return
    _commit_ranging_ack(state, ack)
    rs.pending, rs.pending_kind = False, None
    await _broadcast_ranging(state)


async def _set_imu_env_rate(state, rate_hz: int) -> None:
    """Inbound `set_imu_env_rate`. Independent pending command from ranging
    (Task 10 item 8) -- `SET_IMU_ENV_RATE` (cmd 11), off the event loop.
    `rate_hz=0` means coupled. Honest with today's firmware: an UNKNOWN_CMD
    result is reported as an error and `applied_rate_hz` is left untouched
    (never adopts the request as if it had been confirmed)."""
    ie: ImuEnvRateState = state.imu_env_state
    ctrl = getattr(state, "controller", None)
    client = getattr(state, "client", None)
    if client is None or _transport_kind(ctrl) == "replay":
        ie.error = "IMU/env rate control unavailable in replay"
        await _broadcast_ranging(state)
        return
    if ie.pending:
        log.warning("set_imu_env_rate: rejected -- a rate command is already pending")
        return

    ie.requested_rate_hz = int(rate_hz)
    validation = profiles.validate_imu_env_rate(rate_hz or None)
    if not validation.ok:
        ie.error = "; ".join(validation.errors)
        await _broadcast_ranging(state)
        return
    ie.warning = "; ".join(validation.warnings) if validation.warnings else None
    ie.pending = True
    ie.error = None
    await _broadcast_ranging(state)

    try:
        result, applied = await asyncio.to_thread(client.send_imu_env_rate, int(rate_hz))
    except TimeoutError as exc:
        ie.error = f"SET_IMU_ENV_RATE timeout: {exc}"
        ie.pending = False
        await _broadcast_ranging(state)
        return
    except ProtocolError as exc:
        ie.error = f"SET_IMU_ENV_RATE protocol error: {exc}"
        ie.pending = False
        await _broadcast_ranging(state)
        return
    if result != ResultCode.OK:
        ie.error = f"SET_IMU_ENV_RATE -> {result.name}"
        ie.pending = False
        await _broadcast_ranging(state)
        return
    ie.applied_rate_hz = int(applied)
    ie.initialized = True
    ie.error = None
    ie.pending = False
    _recompute_ranging_estimate(state)
    await _broadcast_ranging(state)


def _view_ready(ui: "UiState", controller=None) -> bool:
    """The ONE predicate for "View is showing a genuinely loaded, matching
    capture" (issue #101 step 3): `ui.source == "view"`, the controller is
    actually replaying (not live, not mid-swap with `replay_path` not yet
    updated), and the file it is replaying is exactly the one the UI believes
    is selected.

    False for every OTHER case, including source != "view" -- this predicate
    says nothing about Live/Splat readiness; a call site that must also admit
    those combines it with its own `ui.source != "view"` check. It is False
    while View is just the capture BROWSER (nothing picked yet, the
    `set_source` empty-selection branch) and equally False in the brief
    window between `load_capture` swapping the reader and `replay_path`
    landing on the new file -- both cases where a live/stale frame must not
    reach the client (the defect this issue fixes)."""
    if ui.source != "view":
        return False
    if not ui.selected_capture or controller is None:
        return False
    if controller.mode != "replay" or not controller.replay_path:
        return False
    return os.path.basename(controller.replay_path) == ui.selected_capture


def _state_message(ui: UiState, controller=None, detailed=None,
                   calibration_available: bool = False) -> dict:
    """Authoritative presentation state.

    ``mode`` is emitted for one release so existing automation remains usable;
    new clients must use the unambiguous Live/View ``source`` + ``display``.
    """
    detail = None
    if controller is not None and controller.mode == "replay" and controller.replay_path:
        try:
            detail = sidecar_status(controller.replay_path, RESULTS_DIR,
                                    getattr(detailed, "preset", None))
        except OSError:
            detail = None
    slam_available = not (controller is not None and controller.mode == "replay" and
                          not controller.index.get("has_stream_9", False))
    return {"type": "state", "color_mode": ui.color_mode,
            "ir_colormap": ui.ir_colormap, "ir_freeze": ui.ir_freeze,
            "view_colormap": ui.view_colormap, "point_size": ui.point_size,
            "point_size_auto": ui.point_size_auto,
            "see_through": ui.see_through,
            "surface_enabled": ui.surface_enabled,
            "surface_mode": ui.surface_mode,
            "surface_threshold_pct": ui.surface_threshold_pct,
            "view_mode": ui.view_mode,
            "view_cam": {m: asdict(c) for m, c in ui.view_cam.items()},
            "orbit_enabled": ui.orbit_enabled,
            "orbit_speed_deg_s": ui.orbit_speed_deg_s,
            "orbit_mode": ui.orbit_mode,
            "orbit_amplitude_deg": ui.orbit_amplitude_deg,
            "mode": ui.mode, "source": ui.source, "display": ui.display,
            "selected_capture": ui.selected_capture,
            "selected_splat": ui.selected_splat, "detailed": detail,
            "slam_available": slam_available,
            # issue #101: the client's reset barrier. `stream_generation` bumps
            # on every live/replay/capture swap (`SessionController.generation`);
            # `ws.js` fires a local `stream_reset` when it changes so every
            # display module clears its OLD-source state before the new
            # `state`/data lands. `stream_ready` is `_view_ready` widened to
            # "Live/Splat are always ready, View only once its predicate holds"
            # -- while it's False the client keeps the capture browser visible
            # and shows nothing else.
            "stream_generation": getattr(controller, "generation", 0),
            "stream_ready": ui.source != "view" or _view_ready(ui, controller),
            "slam_trajectory": ui.slam_trajectory,
            "slam_walls": ui.slam_walls, "slam_follow": ui.slam_follow,
            "idle_enabled": ui.idle_enabled, "idle_level": ui.idle_level,
            "browser_idle_timeout_s": ui.browser_idle_timeout_s,
            "browser_sort": ui.browser_sort, "browser_view": ui.browser_view,
            "browser_thumbs": ui.browser_thumbs,
            "orientation_mode": ui.orientation_mode,
            "orientation_labels": list(ui.orientation_labels),
            "yaw_offset_deg": ui.yaw_offset_deg,
            "elevation_datum_ft": ui.elevation_datum_ft,
            "calibrated": ui.calibrated,
            "calibration_available": calibration_available}


# --- settings persistence (Web Phase 5) -------------------------------------
#
# The web UI's display preferences live in the SAME `roomscan.toml` [viewer]
# table the desktop viewer/panel uses, so a single config follows the user
# across both frontends. Only the web-owned prefs below (the six display toggles
# plus the two sensor auto-idle prefs) are written; every other [viewer] field
# (fov/port/near-mode/yaw-fusion/...) is preserved verbatim because we mutate and
# re-save the whole loaded `ViewerConfig`.
#
# `mode` is deliberately NOT persisted/restored: the SLAM worker is armed lazily
# on the first `set_mode slam` (no GPU burned until then), so a server restart
# always comes up in real-time regardless of the last session -- restoring into
# SLAM would silently spin up the GPU on launch. The desktop panel keeps its own
# `mode` in the file; the web app leaves that field untouched.
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
