hellosamblack/lidar-roomscanner/host/src/roomscan/protocol.py

"""Wire protocol v2 — see docs/protocol.md. Keep in lockstep via protocol-change skill."""
from __future__ import annotations

import math
import struct
import zlib
from dataclasses import dataclass
from enum import IntEnum

import numpy as np

from .sensor_time import signed_tick_delta

MAGIC = b"RSCN"
VERSION = 2
# v2 changed only the COMMAND/ACK payload registry (new commands 8-12, one new 12-byte
# COMMAND shape for SET_MANUAL_PARAMS, one new 16-byte ACK shape for commands 9/10). The
# 32-byte frame header and every DATA/EVENT stream are byte-for-byte unchanged, so a v1
# recording still decodes: FrameHeader.unpack() accepts either version, new encodes use
# VERSION (2). See docs/protocol.md "Version history".
SUPPORTED_VERSIONS = (1, 2)
HEADER_SIZE = 32
FLAG_DROPPED = 0x01

_HEADER = struct.Struct("<4sBBBBIQHHII")  # magic, ver, type, stream, flags, seq, t_us, w, h, plen, reserved
assert _HEADER.size == HEADER_SIZE


class FrameType(IntEnum):
    DATA = 1
    EVENT = 2
    COMMAND = 3
    ACK = 4


class StreamId(IntEnum):
    DEPTH_ZF32 = 0
    DEPTH_ZAPC = 1
    AMBIENT = 2
    AMPLITUDE = 3
    CONFIDENCE = 4
    REFLECTANCE = 5
    STATUS = 6
    RAW_3DMD = 7
    CALIB = 8
    IMU_QUAT = 9
    ENV = 10
    IMU_RAW = 11
    IMU_CAL = 12
    IMU_SYNC = 13


class EventCode(IntEnum):
    SENSOR_INIT_FAIL = 1
    TRIGGER_TIMEOUT = 2
    DMA_TIMEOUT = 3
    SENSOR_ERROR_STATUS = 4
    TX_OVERFLOW = 5
    AUTO_WAKE_MOTION = 6
    TX_QUEUE_STATS = 7  # Ethernet TX-pacer queue telemetry (Task 6); see
                        # parse_tx_queue_stats_event() -- its payload is NOT the
                        # general ASCII message parse_event() decodes.


class CommandCode(IntEnum):
    PING = 1
    SEND_CALIB = 2
    SET_USECASE = 3
    SET_FRAME_PERIOD_US = 4
    SET_EXPOSURE_MS = 5
    REINIT = 6
    SET_STANDBY = 7
    SET_RANGING_PROFILE = 8   # legacy cmd+param shape; param = ProfileId
    SET_MANUAL_PARAMS = 9     # v2-only manual shape (see pack_manual_command)
    GET_RANGING_CONFIG = 10   # legacy cmd+param shape; param ignored
    SET_IMU_ENV_RATE = 11     # legacy cmd+param shape; param = rate_hz (0 = coupled)
    GET_IMU_ENV_RATE = 12     # legacy cmd+param shape; param ignored


class ProfileId(IntEnum):
    """SET_RANGING_PROFILE (cmd 8) param / ACK applied -- the WIRE preset enum, whose
    table is firmware-resident. Values match the host-facing `profiles.ProfileId`.

    LEGACY as of 2026-08-05: the host now composes presets itself (resolves a preset to
    its `profiles.PRESETS` entry and applies it via SET_MANUAL_PARAMS + an IMU rate),
    so the web/CLI apply path no longer sends cmd 8. This enum is kept for the raw
    command path and back-compat. MANUAL (3) reapplies the last accepted
    SET_MANUAL_PARAMS candidate and is rejected until one exists."""
    STABILITY = 0
    PRECISION = 1
    HIGH_FRAMERATE = 2
    MANUAL = 3


class RangingMode(IntEnum):
    """SET_MANUAL_PARAMS (cmd 9) `ranging_mode` field, and the same field name in the
    cmd 9/10 extended ACK. AMBIENT = DSS-assisted, 450 mm min distance; PRECISION =
    no DSS, 50 mm min distance."""
    AMBIENT = 0
    PRECISION = 1


class PowerMode(IntEnum):
    """SET_MANUAL_PARAMS (cmd 9) `power_mode` field, and the same field name in the
    cmd 9/10 extended ACK."""
    ULP = 0
    LP = 1
    REGULAR = 2


# SET_MANUAL_PARAMS (cmd 9) exposure_ms unit: integer milliseconds. Task 1 finding: the
# current vl53l9_set_exposure() driver takes integer ms; a 0.5 ms step is not implemented
# by the firmware, so the wire field and the spec both use whole milliseconds — single
# source of truth for the unit, see docs/protocol.md.
EXPOSURE_MS_STEP = 1

# SET_IMU_ENV_RATE (cmd 11) param / ACK applied bounds. 0 is the default: one IMU/env
# sample per ToF trigger, byte-identical to pre-v2 firmware behavior (Task 7 implements
# the decoupled path; this registry is the codec-level contract).
IMU_ENV_RATE_COUPLED = 0
IMU_ENV_RATE_MAX_HZ = 480


class StandbyLevel(IntEnum):
    """SET_STANDBY param / ACK applied. ACTIVE = streaming, SOFT = FSM standby
    (VCSEL idle, instant resume), HARD = XSHUT power-down (full re-bring-up to wake)."""
    ACTIVE = 0
    SOFT = 1
    HARD = 2


class ResultCode(IntEnum):
    OK = 0
    UNKNOWN_CMD = 1
    BAD_PARAM = 2
    REJECTED_BINNING = 3
    SENSOR_ERROR = 4
    BUSY = 5


DEPTH_NO_RETURN_MM = 12000.0  # empirical no-return sentinel in DEPTH_ZF32 payloads (Task 8)
RAW_3DMD_SIZE_BIN2 = 14842  # size in bytes at binning=2 (54×42 zones)
CALIB_SIZE = 2332  # VL53L9_CALIB_DATA_SIZE per-device calibration blob
IMU_QUAT_SIZE = 16  # 4x float32 [w, x, y, z], LSM body frame
ENV_SIZE = 20       # pressure f32 (Pa) + mag 3xf32 (µT) + temp f32 (°C)

# --- stream 11 (IMU_RAW): verbatim LSM6DSV16X FIFO words ---------------------
IMU_RAW_REC_SIZE = 8  # tag byte + 6 data bytes + 1 reserved zero


class ImuFifoTag(IntEnum):
    """LSM6DSV16X FIFO tag ids (AN5763 rev 4, FIFO_DATA_OUT_TAG.TAG_SENSOR).

    Only the tags stream 11 carries: the SFLP game-rotation word (0x13) rides
    stream 9 already, and the sensor-hub words (0x0E-0x10) ride stream 10.
    """
    GY_NC = 0x01
    XL_NC = 0x02
    TIMESTAMP = 0x04
    SFLP_GBIAS = 0x16
    SFLP_GRAVITY = 0x17


# Sensitivities. NB the gyro/accel ones follow the FULL SCALE the firmware selects in
# firmware/scanner-stream/Src/rs_lsm.c (RS_LSM_GY_FS = ±500 dps, RS_LSM_XL_FS = ±4 g); change
# those knobs and these must change with them. The two SFLP vectors are fixed-scale regardless
# of the XL/GY full scale (gravity is always ±2 g, gbias always ±125 dps).
IMU_RAW_GY_MDPS_PER_LSB = 17.5     # ±500 dps
IMU_RAW_XL_MG_PER_LSB = 0.122      # ±4 g
IMU_RAW_GRAVITY_MG_PER_LSB = 0.061    # SFLP gravity vector, fixed ±2 g
IMU_RAW_GBIAS_MDPS_PER_LSB = 4.375    # SFLP gyro-bias vector, fixed ±125 dps
IMU_RAW_TICK_US = 21.7             # LSM timestamp counter LSB, nominal (DS13510 rev 4)

# --- stream 12 (IMU_CAL): the LSM's own clock trim -----------------------------------
# IMU_RAW_TICK_US above is only correct for a part whose internal oscillator landed exactly
# on nominal. Real parts are trimmed, and the trim is readable: INTERNAL_FREQ_FINE (register
# 0x4F) gives the deviation in 0.13% steps, and AN5763 6.4 turns it into the true period
#
#     t_tick = 1 / (46080 * (1 + 0.0013 * freq_fine))   [seconds]
#
# Measured on this rig 2026-07-28: the host clock ran 1.029790x the LSM's, i.e. ~29790 ppm
# of pure scale error, because the host was integrating gyro against the nominal tick. That
# turns a 90 deg pan into ~87.3 deg — far worse than any quantisation floor.
IMU_CAL_SIZE = 4                   # int8 freq_fine, uint8 valid, uint16 reserved
IMU_TICK_BASE_HZ = 46080.0         # nominal timestamp-counter frequency (AN5763 6.4)
IMU_TICK_FREQ_FINE_STEP = 0.0013   # 0.13% per FREQ_FINE LSB

# --- stream 13 (IMU_SYNC): the frame's FRAME_READY edge on the LSM's own clock ---------
# The header's t_us is that edge on the MCU's TIM2 clock. Placing it on the LSM clock used to
# mean guessing from stream 11's FIFO words, which are samples taken before a drain that runs
# 1-2 ms later in the firmware's loop -- measured host-side at 1082 µs RMS of residual against
# a windowed linear clock fit, and demonstrably load-dependent (a frame that also carries CALIB
# drains 673 µs later, t = -3.9 over 5331 static frames). Stream 13 carries the answer instead:
# the LSM TIMESTAMP register read at the edge, with the delay and the read's own duration
# alongside so the residual uncertainty is stated rather than assumed. See BUG-031.
#
# It also answers the question that turns out to dominate the error budget: WHEN the stream-9
# quaternion sent alongside a frame is actually valid. That quat is the mean of a whole FIFO
# batch (firmware `RS_LSM_SFLP_AVERAGE`, shipped for BUG-027's 2.8x noise cut), so it carries the
# batch's MIDPOINT orientation, which on this rig sits +7.8 ms AFTER the frame-ready edge (the
# drain is +24.3 ms after it). ~0.3 deg at 38.5 deg/s — an order of magnitude above the skew
# above, and it LEADS the depth frame rather than lagging it.
IMU_SYNC_SIZE = 22   # u32 ticks, u32 latch_us, u32 drain_us, u32 quat_mid_ticks, u16 read_us, u16 quat_n, u8 valid, u8 rsv

# --- EVENT code TX_QUEUE_STATS (7): Ethernet TX-pacer queue telemetry (Task 6) --------
# 4 code + 4 detail + 4 enqueue_drops + 4 stack_stalls + 4 emitted_bytes. Mirrors firmware
# RS_EVT_TX_QUEUE_STATS_LEN (firmware/scanner-stream/Src/rs_protocol.h). See
# parse_tx_queue_stats_event() below for the field layout.
RS_EVT_TX_QUEUE_STATS_LEN = 20


class ProtocolError(Exception):
    pass


@dataclass(frozen=True)
class FrameHeader:
    frame_type: int
    stream_id: int
    flags: int
    seq: int
    t_us: int
    width: int
    height: int
    payload_len: int

    @classmethod
    def unpack(cls, buf: bytes) -> "FrameHeader":
        magic, ver, ftype, stream, flags, seq, t_us, w, h, plen, _res = _HEADER.unpack(buf)
        if magic != MAGIC:
            raise ProtocolError(f"bad magic {magic!r}")
        if ver not in SUPPORTED_VERSIONS:
            raise ProtocolError(f"unsupported version {ver}")
        return cls(ftype, stream, flags, seq, t_us, w, h, plen)

    def pack(self) -> bytes:
        return _HEADER.pack(MAGIC, VERSION, self.frame_type, self.stream_id, self.flags,
                            self.seq, self.t_us, self.width, self.height, self.payload_len, 0)


@dataclass(frozen=True)
class Frame:
    header: FrameHeader
    payload: bytes


def pack_frame(header: FrameHeader, payload: bytes) -> bytes:
    if len(payload) != header.payload_len:
        raise ProtocolError(f"payload length {len(payload)} != header {header.payload_len}")
    body = header.pack() + payload
    return body + zlib.crc32(body).to_bytes(4, "little")


def parse_event(payload: bytes) -> tuple[int, int, str]:
    """Decode a frame_type=EVENT payload -> (code, detail, message)."""
    if len(payload) < 8:
        raise ProtocolError(f"event payload too short: {len(payload)} bytes")
    code, detail = struct.unpack_from("<II", payload, 0)
    return code, detail, payload[8:].decode("ascii", "replace")


# --- EVENT code TX_QUEUE_STATS (7): Ethernet TX-pacer queue telemetry (Task 6) --------
#
# docs/superpowers/plans/completed/2026-07-31-high-framerate-and-manual-ranging-modes.md Task 6
# step 2: "prove zero, don't infer it" -- the firmware emits this on the same 64-frame
# cadence as the periodic CALIB retransmit (firmware/scanner-stream/Src/vl53l9_app.c,
# rs_send_tx_queue_stats_event()) so a 60 s hardware capture at any rate samples it many
# times. Deliberately NOT routed through parse_event(): every other EVENT code's payload
# past code+detail is the general ASCII message, but this one packs three binary u32
# counters there instead (docs/protocol.md "TX_QUEUE_STATS (EVENT code 7) payload
# layout") -- parse_event() would garble it through its ascii/"replace" decode.
_TX_QUEUE_STATS_TRANSPORT_NAMES = {0: "none", 1: "cdc", 2: "udp"}


@dataclass(frozen=True)
class TxQueueStatsEvent:
    """Decoded TX_QUEUE_STATS payload. `active_transport` is the firmware's own
    coarse hint (Ethernet preferred if it has a target, else CDC if connected,
    else none) -- NOT the host's authoritative transport truth, which is
    computed independently from which physical source class is actually being
    read (`roomscan.web._transport_kind()`)."""
    queue_high_water: int
    active_transport: str        # "none" | "cdc" | "udp"
    pending_fragments: int
    enqueue_drops: int
    stack_stalls: int
    emitted_bytes: int


def parse_tx_queue_stats_event(payload: bytes) -> TxQueueStatsEvent:
    """Decode EVENT code TX_QUEUE_STATS (7)'s 20-byte payload (docs/protocol.md).

    Raises ProtocolError on the wrong length or a mismatched code -- callers
    that peek at raw EVENT bytes (e.g. `UdpSource`, which must not assume
    every EVENT it sees is this one) should catch that and treat it as "not a
    TX_QUEUE_STATS frame", the same tolerant-skip convention the rest of the
    wire decoder uses for anything it doesn't recognize.
    """
    if len(payload) != RS_EVT_TX_QUEUE_STATS_LEN:
        raise ProtocolError(
            f"tx-queue-stats payload must be {RS_EVT_TX_QUEUE_STATS_LEN} bytes, got {len(payload)}")
    code, detail, enqueue_drops, stack_stalls, emitted_bytes = struct.unpack("<IIIII", payload)
    if code != EventCode.TX_QUEUE_STATS:
        raise ProtocolError(f"not a TX_QUEUE_STATS event (code={code})")
    high_water = detail & 0xFF
    transport_id = (detail >> 8) & 0xFF
    pending = (detail >> 16) & 0xFFFF
    return TxQueueStatsEvent(
        queue_high_water=high_water,
        active_transport=_TX_QUEUE_STATS_TRANSPORT_NAMES.get(transport_id, "none"),
        pending_fragments=pending,
        enqueue_drops=enqueue_drops,
        stack_stalls=stack_stalls,
        emitted_bytes=emitted_bytes,
    )


def _humanize_bytes(n: int) -> str:
    """Compact IEC size for a byte counter, e.g. 1234567890 -> '1.15 GiB'."""
    val = float(n)
    for unit in ("B", "KiB", "MiB", "GiB", "TiB"):
        if val < 1024.0 or unit == "TiB":
            return f"{n} B" if unit == "B" else f"{val:.2f} {unit}"
        val /= 1024.0
    return f"{n} B"  # unreachable; keeps the type checker happy


def describe_event(payload: bytes) -> tuple[int, int, str]:
    """Decode an EVENT payload into (code, detail, human-legible message).

    A display-layer superset of parse_event(): it names the code and, for
    TX_QUEUE_STATS (7) -- whose bytes past code+detail are three binary u32
    counters, not an ASCII string -- formats those counters instead of
    ascii/'replace'-decoding them into mojibake (the ``code=7 detail=131589
    <garbage>`` seen in the web event log). Use this anywhere an EVENT is shown
    to a human (the web event log, the CLI viewers); parse_event() stays the
    low-level raw decode used by golden-vector tests and byte-exact callers.
    """
    if len(payload) < 8:
        raise ProtocolError(f"event payload too short: {len(payload)} bytes")
    code, detail = struct.unpack_from("<II", payload, 0)
    try:
        name = EventCode(code).name
    except ValueError:
        name = f"EVENT_{code}"

    if code == EventCode.TX_QUEUE_STATS:
        try:
            ev = parse_tx_queue_stats_event(payload)
        except ProtocolError:
            # Right code, unexpected length -- say so rather than garbling it.
            return code, detail, f"{name} (malformed {len(payload)}-byte payload)"
        return code, detail, (
            f"{name} transport={ev.active_transport} "
            f"high_water={ev.queue_high_water} pending={ev.pending_fragments} "
            f"drops={ev.enqueue_drops} stalls={ev.stack_stalls} "
            f"emitted={_humanize_bytes(ev.emitted_bytes)}")

    text = payload[8:].decode("ascii", "replace").strip()
    return code, detail, f"{name}: {text}" if text else name


def pack_command(cmd: int, param: int, token: int) -> bytes:
    """Pack a COMMAND frame: cmd (u32) + param (u32) LE, with header seq=token.

    Returns the full wire frame (header + payload + CRC).
    """
    payload = struct.pack("<II", cmd, param)
    header = FrameHeader(
        frame_type=FrameType.COMMAND,
        stream_id=0,
        flags=0,
        seq=token,
        t_us=0,
        width=0,
        height=0,
        payload_len=len(payload),
    )
    return pack_frame(header, payload)


def parse_ack(payload: bytes) -> tuple[int, int, int]:
    """Decode a frame_type=ACK payload -> (cmd, result, applied).

    ACK payloads are exactly 12 bytes; any other length is malformed (unlike
    EVENT's legitimate variable message tail) and raises ProtocolError.

    This is the legacy raw-tuple decoder (commands 1-8, 11, 12 all use this 12-byte
    shape; for 11/12 `applied` IS the applied rate_hz). Commands 9 and 10 use a longer,
    differently-shaped ACK and are NOT decodable with this function — use
    `parse_typed_ack` instead, which dispatches on the command code and returns a typed
    `LegacyAck`/`RangingConfigAck` rather than an untyped tuple.
    """
    if len(payload) != ACK_LEGACY_SIZE:
        raise ProtocolError(f"ACK payload must be exactly {ACK_LEGACY_SIZE} bytes, got {len(payload)}")
    cmd, result, applied = struct.unpack("<III", payload)
    return cmd, result, applied


# --- v2 typed COMMAND/ACK codec (SET_MANUAL_PARAMS + the extended ranging-config ACK) -------
# See docs/protocol.md "COMMAND frame payload" / "ACK frame payload" for the authoritative
# byte-offset tables. This is the payload-layout change v2 exists for: v1's fixed 8-byte
# cmd+param COMMAND payload cannot carry SET_MANUAL_PARAMS's four fields.

ACK_LEGACY_SIZE = 12  # cmd(4) + result(4) + applied(4) -- commands 1-8, 11, 12

_MANUAL_PARAMS_FMT = "<IBIHB"  # cmd, ranging_mode, frame_period_us, exposure_ms, power_mode
MANUAL_PARAMS_PAYLOAD_SIZE = struct.calcsize(_MANUAL_PARAMS_FMT)  # 12
assert MANUAL_PARAMS_PAYLOAD_SIZE == 12

_RANGING_CONFIG_FMT = "<BIHB"  # ranging_mode, frame_period_us, exposure_ms, power_mode
RANGING_CONFIG_SIZE = struct.calcsize(_RANGING_CONFIG_FMT)  # 8 -- the config-only portion
ACK_RANGING_CONFIG_SIZE = 8 + RANGING_CONFIG_SIZE  # cmd(4) + result(4) + config(8) = 16
assert ACK_RANGING_CONFIG_SIZE == 16


@dataclass(frozen=True)
class ManualParams:
    """Decoded SET_MANUAL_PARAMS (cmd 9) payload fields, sans the leading cmd word.

    `exposure_ms` is an integer millisecond count (EXPOSURE_MS_STEP; Task 1 finding: no
    0.5 ms step in the current driver). `ranging_mode`/`power_mode` are the raw wire ints
    -- construct with `RangingMode`/`PowerMode` members for readability, e.g.
    `ManualParams(RangingMode.PRECISION, 11_111, 4, PowerMode.REGULAR)`.
    """
    ranging_mode: int
    frame_period_us: int
    exposure_ms: int
    power_mode: int


def pack_manual_command(params: ManualParams, token: int) -> bytes:
    """Pack a SET_MANUAL_PARAMS (cmd 9) COMMAND frame.

    Payload: cmd(u32) + ranging_mode(u8) + frame_period_us(u32) + exposure_ms(u16) +
    power_mode(u8), 12 bytes total, no padding on the wire -- MANUAL_PARAMS_PAYLOAD_SIZE.
    This is the one COMMAND payload v1 cannot represent (v1's payload is a fixed 8 bytes),
    which is why protocol v2 exists. Returns the full wire frame (header + payload + CRC).
    """
    payload = struct.pack(_MANUAL_PARAMS_FMT, CommandCode.SET_MANUAL_PARAMS,
                          params.ranging_mode, params.frame_period_us,
                          params.exposure_ms, params.power_mode)
    header = FrameHeader(
        frame_type=FrameType.COMMAND,
        stream_id=0,
        flags=0,
        seq=token,
        t_us=0,
        width=0,
        height=0,
        payload_len=len(payload),
    )
    return pack_frame(header, payload)


def parse_manual_command(payload: bytes) -> ManualParams:
    """Decode a SET_MANUAL_PARAMS COMMAND payload -> ManualParams.

    Device-side counterpart of `pack_manual_command` (the firmware's C decoder is
    `rs_parse_command`'s RS_PARSED_CMD_MANUAL branch; this exists on the host so the same
    v2 vectors can be round-tripped and cross-checked in tests). Raises ProtocolError on
    the wrong length or a payload whose leading cmd word isn't SET_MANUAL_PARAMS.
    """
    if len(payload) != MANUAL_PARAMS_PAYLOAD_SIZE:
        raise ProtocolError(
            f"SET_MANUAL_PARAMS payload must be {MANUAL_PARAMS_PAYLOAD_SIZE} bytes, "
            f"got {len(payload)}")
    cmd, ranging_mode, frame_period_us, exposure_ms, power_mode = struct.unpack(
        _MANUAL_PARAMS_FMT, payload)
    if cmd != CommandCode.SET_MANUAL_PARAMS:
        raise ProtocolError(
            f"expected SET_MANUAL_PARAMS ({int(CommandCode.SET_MANUAL_PARAMS)}) cmd word, got {cmd}")
    return ManualParams(ranging_mode, frame_period_us, exposure_ms, power_mode)


@dataclass(frozen=True)
class LegacyAck:
    """Typed form of the legacy 12-byte ACK (cmd, result, applied) -- commands 1-8, 11,
    12. For 11 (SET_IMU_ENV_RATE) and 12 (GET_IMU_ENV_RATE) `applied` IS the applied
    rate_hz (0 = coupled)."""
    cmd: int
    result: int
    applied: int


@dataclass(frozen=True)
class RangingConfigAck:
    """Typed form of the extended 16-byte ACK -- commands 9 (SET_MANUAL_PARAMS) and 10
    (GET_RANGING_CONFIG). Carries the complete applied/readback ranging configuration
    after cmd+result, so the host can prove what the device actually applied instead of
    echoing the request back at itself. Sent with this shape regardless of `result`
    (docs/protocol.md): a BUSY/BAD_PARAM/SENSOR_ERROR result still returns 16 bytes, with
    the config fields either the prior known-good config or zeroed, never a shorter
    payload -- the ACK's wire shape depends only on which command it answers."""
    cmd: int
    result: int
    ranging_mode: int
    frame_period_us: int
    exposure_ms: int
    power_mode: int


_RANGING_CONFIG_ACK_CMDS = frozenset({CommandCode.SET_MANUAL_PARAMS, CommandCode.GET_RANGING_CONFIG})


def parse_typed_ack(cmd: int, payload: bytes) -> "LegacyAck | RangingConfigAck":
    """Typed ACK decode, keyed by the command code the ACK answers.

    Commands 9 (SET_MANUAL_PARAMS) and 10 (GET_RANGING_CONFIG) use the extended 16-byte
    ranging-config ACK shape; every other command (1-8, 11, 12) uses the legacy 12-byte
    cmd+result+applied shape. The caller always knows which command it sent, so dispatch
    is by `cmd`, not by inferring the shape from payload length -- see docs/protocol.md
    "ACK frame payload" for the exact byte offsets each shape uses.
    """
    if cmd in _RANGING_CONFIG_ACK_CMDS:
        if len(payload) != ACK_RANGING_CONFIG_SIZE:
            raise ProtocolError(
                f"ranging-config ACK payload must be {ACK_RANGING_CONFIG_SIZE} bytes, "
                f"got {len(payload)}")
        c, result, ranging_mode, frame_period_us, exposure_ms, power_mode = struct.unpack(
            "<II" + _RANGING_CONFIG_FMT[1:], payload)
        return RangingConfigAck(c, result, ranging_mode, frame_period_us, exposure_ms, power_mode)
    if len(payload) != ACK_LEGACY_SIZE:
        raise ProtocolError(f"ACK payload must be exactly {ACK_LEGACY_SIZE} bytes, got {len(payload)}")
    c, result, applied = struct.unpack("<III", payload)
    return LegacyAck(c, result, applied)


def decode_imu_quat(payload: bytes) -> tuple[float, float, float, float]:
    """Decode a stream 9 IMU_QUAT payload -> (w, x, y, z) unit quaternion."""
    if len(payload) != IMU_QUAT_SIZE:
        raise ProtocolError(f"IMU_QUAT payload must be {IMU_QUAT_SIZE} bytes, got {len(payload)}")
    w, x, y, z = struct.unpack("<4f", payload)
    return w, x, y, z


@dataclass(frozen=True)
class ImuRawBatch:
    """One stream-11 payload, demuxed by FIFO tag. Every array is one row per FIFO word,
    in FIFO (chronological) order; the matching `*_cnt` array holds that word's TAG_CNT
    (the 2-bit sample-time slot counter), which is what groups a gyro word with the accel
    and timestamp words of the same sample time."""
    gyro_dps: "np.ndarray"        # (N, 3) float64, deg/s
    gyro_cnt: "np.ndarray"        # (N,) uint8
    accel_g: "np.ndarray"         # (N, 3) float64, g
    accel_cnt: "np.ndarray"
    gravity_g: "np.ndarray"       # (N, 3) float64, g — SFLP gravity vector
    gravity_cnt: "np.ndarray"
    gbias_dps: "np.ndarray"       # (N, 3) float64, deg/s — SFLP gyro bias estimate
    gbias_cnt: "np.ndarray"
    timestamp_ticks: "np.ndarray"  # (N,) uint32, LSM timestamp counter (`tick_us` per LSB)
    timestamp_cnt: "np.ndarray"
    n_records: int                # total words in the payload, including unknown tags
    tick_us: float = IMU_RAW_TICK_US  # timestamp LSB actually applied (see decode_imu_raw)

    @property
    def timestamp_us(self) -> "np.ndarray":
        """Timestamp words in microseconds on the LSM's own clock."""
        return self.timestamp_ticks.astype(np.float64) * self.tick_us


def decode_imu_raw(payload: bytes, tick_us: float = IMU_RAW_TICK_US) -> ImuRawBatch:
    """Decode a stream 11 IMU_RAW payload (N × 8-byte verbatim FIFO records).

    Record layout: byte 0 = the FIFO_DATA_OUT_TAG register byte, `TAG_SENSOR << 3 |
    TAG_CNT << 1` (bit 0 is the register's not_used0 and is always 0 — the ST driver
    discards it); bytes 1-6 = the FIFO data bytes untouched; byte 7 = reserved zero.

    `tick_us` is the timestamp-counter LSB to scale the TIMESTAMP words by. It defaults to
    the nominal 21.7 µs, which is what a recording made before stream 12 existed can offer;
    pass `imu_tick_us(freq_fine)` from a stream-12 frame to get the part's real tick.
    """
    if len(payload) == 0 or len(payload) % IMU_RAW_REC_SIZE != 0:
        raise ProtocolError(
            f"IMU_RAW payload must be a non-zero multiple of {IMU_RAW_REC_SIZE} bytes, "
            f"got {len(payload)}")
    rec = np.frombuffer(payload, dtype=np.uint8).reshape(-1, IMU_RAW_REC_SIZE)
    tag = rec[:, 0] >> 3
    cnt = (rec[:, 0] >> 1) & 0x03
    data = rec[:, 1:7]

    def vec3(tag_id: int, scale: float) -> tuple["np.ndarray", "np.ndarray"]:
        sel = tag == tag_id
        words = np.ascontiguousarray(data[sel]).view("<i2").reshape(-1, 3)
        return words.astype(np.float64) * scale, cnt[sel]

    gyro, gyro_cnt = vec3(ImuFifoTag.GY_NC, IMU_RAW_GY_MDPS_PER_LSB / 1000.0)
    accel, accel_cnt = vec3(ImuFifoTag.XL_NC, IMU_RAW_XL_MG_PER_LSB / 1000.0)
    gravity, gravity_cnt = vec3(ImuFifoTag.SFLP_GRAVITY, IMU_RAW_GRAVITY_MG_PER_LSB / 1000.0)
    gbias, gbias_cnt = vec3(ImuFifoTag.SFLP_GBIAS, IMU_RAW_GBIAS_MDPS_PER_LSB / 1000.0)

    ts_sel = tag == ImuFifoTag.TIMESTAMP
    # timestamp word: u32 tick in data[0:4], BDR metadata in data[4:6] (not decoded)
    ticks = np.ascontiguousarray(data[ts_sel][:, :4]).view("<u4").reshape(-1)

    return ImuRawBatch(gyro, gyro_cnt, accel, accel_cnt, gravity, gravity_cnt,
                       gbias, gbias_cnt, ticks, cnt[ts_sel], rec.shape[0], tick_us)


def imu_tick_us(freq_fine: int) -> float:
    """LSM timestamp-counter LSB in µs for a given INTERNAL_FREQ_FINE (AN5763 6.4)."""
    return 1e6 / (IMU_TICK_BASE_HZ * (1.0 + IMU_TICK_FREQ_FINE_STEP * freq_fine))


@dataclass(frozen=True)
class ImuClockCal:
    """One stream-12 payload: the LSM6DSV16X's factory oscillator trim."""
    freq_fine: int    # INTERNAL_FREQ_FINE (register 0x4F), signed, 0.13% per LSB
    valid: bool       # False => the device could not read the register; use the nominal tick

    @property
    def tick_us(self) -> float:
        """True timestamp-counter LSB, falling back to nominal when `valid` is False."""
        return imu_tick_us(self.freq_fine) if self.valid else IMU_RAW_TICK_US


def decode_imu_cal(payload: bytes) -> ImuClockCal:
    """Decode a stream 12 IMU_CAL payload -> ImuClockCal.

    Layout: int8 freq_fine, uint8 valid, uint16 reserved (0). The device only emits this
    stream at all once it has read the register successfully, so `valid` is 1 in practice;
    it exists so the field can never be silently mistaken for a legitimate freq_fine of 0.
    """
    if len(payload) != IMU_CAL_SIZE:
        raise ProtocolError(f"IMU_CAL payload must be {IMU_CAL_SIZE} bytes, got {len(payload)}")
    freq_fine, valid, _reserved = struct.unpack("<bBH", payload)
    return ImuClockCal(freq_fine, bool(valid))


@dataclass(frozen=True)
class ImuSync:
    """One stream-13 payload: this ToF frame's FRAME_READY edge on the LSM clock.

    `lsm_ticks` is in the same units as stream 11's TIMESTAMP words, so scale it with the
    stream-12 tick (`ImuClockCal.tick_us`), not the nominal 21.7 µs.
    """
    lsm_ticks: int          # LSM TIMESTAMP counter latched just after FRAME_READY
    latch_delay_us: int     # MCU µs from the frame's t_us to the middle of that read
    drain_delay_us: int     # MCU µs from the frame's t_us to the FIFO drain (diagnostic)
    quat_mid_ticks: int     # LSM tick the paired stream-9 quaternion is valid AT (batch midpoint)
    read_us: int            # duration of the latch read — the uncertainty on lsm_ticks
    quat_n: int             # SFLP samples averaged into that quaternion (0 = none this drain)
    valid: bool

    def frame_ready_ticks(self, tick_us: float) -> float:
        """The FRAME_READY edge itself, in LSM ticks: the latch minus its own delay."""
        return self.lsm_ticks - self.latch_delay_us / tick_us

    def quat_offset_us(self, tick_us: float) -> float | None:
        """How far the paired quaternion's instant sits AFTER the frame-ready edge, in µs.

        Positive means the orientation LEADS the depth frame, which is the case here
        (+7.8 ms measured): the averaged batch straddles the edge and is centred well
        past it. A host that wants the orientation at the frame instant must propagate
        it BACKWARD by this much — the opposite direction to "the quat is stale".
        Returns None when this drain produced no quaternion.

        Wrap-safe (#155): `lsm_ticks` and `quat_mid_ticks` are raw uint32 counter
        values ~8 ms apart on a clock that wraps every ~26 h, so the delta is taken
        modulo 2^32 (nearest signed representative), not by plain subtraction —
        otherwise one frame per wrap reports an offset of ±26 hours.
        """
        if not self.quat_n or not self.quat_mid_ticks:
            return None
        mid_after_latch = signed_tick_delta(self.lsm_ticks, self.quat_mid_ticks)
        return (mid_after_latch + self.latch_delay_us / tick_us) * tick_us


def decode_imu_sync(payload: bytes) -> ImuSync:
    """Decode a stream 13 IMU_SYNC payload -> ImuSync.

    Layout: u32 lsm_ticks, u32 latch_delay_us, u32 drain_delay_us, u32 quat_mid_ticks,
    u16 read_us, u16 quat_n, u8 valid, u8 reserved (0). The device only emits the stream
    when the register read succeeded, so `valid` is 1 in practice; absence of the stream
    means "unknown", exactly like stream 12.
    """
    if len(payload) != IMU_SYNC_SIZE:
        raise ProtocolError(f"IMU_SYNC payload must be {IMU_SYNC_SIZE} bytes, got {len(payload)}")
    (ticks, latch_us, drain_us, quat_mid, read_us, quat_n,
     valid, _reserved) = struct.unpack("<IIIIHHBB", payload)
    return ImuSync(ticks, latch_us, drain_us, quat_mid, read_us, quat_n, bool(valid))


def decode_env(payload: bytes) -> tuple[float, tuple[float, float, float], float]:
    """Decode a stream 10 ENV payload -> (pressure_pa, (mx, my, mz) µT, temp_c)."""
    if len(payload) != ENV_SIZE:
        raise ProtocolError(f"ENV payload must be {ENV_SIZE} bytes, got {len(payload)}")
    pressure, mx, my, mz, temp = struct.unpack("<5f", payload)
    return pressure, (mx, my, mz), temp


def is_valid_mag(mag: tuple[float, float, float] | list[float] | np.ndarray) -> bool:
    """True if mag vector is finite and non-zero (> 1e-3 µT magnitude)."""
    if len(mag) != 3:
        return False
    mx, my, mz = float(mag[0]), float(mag[1]), float(mag[2])
    if not (math.isfinite(mx) and math.isfinite(my) and math.isfinite(mz)):
        return False
    return (mx * mx + my * my + mz * mz) > 1e-3


def is_valid_env(pressure_pa: float, mag: tuple[float, float, float] | list[float] | np.ndarray, temp_c: float) -> bool:
    """True if all ENV components are finite and within physical sensor bounds."""
    if not (math.isfinite(pressure_pa) and 30000.0 <= pressure_pa <= 120000.0):
        return False
    if not (math.isfinite(temp_c) and -40.0 <= temp_c <= 85.0):
        return False
    return is_valid_mag(mag)


# --- RAW_3DMD frame metadata tail (vl53l9_meta_t) ---------------------------
# The VL53L9CX places a fixed metadata block in the LAST TOF_META_SIZE bytes of
# every raw 3DMD payload (firmware/vendor/53L9A1/Utilities/vl53l9-common/vl53l9/
# vl53l9_utils.c:155: buffer[buffer_size - sizeof(vl53l9_meta_t)]). The firmware
# reads only frame_counter from it; the host archives the whole tail in every
# RAW_3DMD frame but never decoded it. Offsets below are relative to the start of
# the metadata block and were validated empirically against recorded captures
# (frame_counter increments 1/frame, frame_period_us == 33333 at 30 fps,
# nb_step 6/7 distinguishes ambient/precision, frame_width/height == 54/42).
TOF_META_SIZE = 100  # sizeof(vl53l9_meta_t)

# AN6522 Table 3 step->exposure ratios (nb_shot_step_n = ratio * exposure_ms).
# Keyed by nb_step: precision mode runs 7 integration steps, ambient runs 6.
_TOF_EXPOSURE_RATIOS = {
    7: (117.0, 1443.0),   # precision: (step1, step6) coefficients
    6: (231.0, 1418.0),   # ambient
}


def _u24le(m: bytes, o: int) -> int:
    return m[o] | (m[o + 1] << 8) | (m[o + 2] << 16)


def decode_tof_meta(payload: bytes) -> dict | None:
    """Decode the vl53l9_meta_t block in a RAW_3DMD payload's last 100 bytes.

    Accepts a full RAW_3DMD payload (or just the >=100-byte tail) and returns a
    flat dict of the device's per-frame readback: die temperature, per-frame
    error status/code, reference-SPAD channels, DSS/binning/nb_step, actual
    frame_period, and the nb_shot_step exposure counts -- plus a derived
    `exposure_ms`, `ranging_mode`, and `fps`. Returns None if the payload is too
    short to carry the metadata block.

    `die_temp_c` is the sensor die temperature; ST does not document a scale in
    the vendored header, but it reads as degrees C empirically (a few C above the
    STTS22H ambient, tracking laser self-heating). `exposure_ms` is inverted from
    the nb_shot_step counts via the AN6522 ratios; `exposure_consistent` is True
    when the step1- and step6-derived values agree within 2%.
    """
    if payload is None or len(payload) < TOF_META_SIZE:
        return None
    m = payload[-TOF_META_SIZE:]

    frame_counter = int.from_bytes(m[0:4], "little")
    die_temp_c = int.from_bytes(m[4:6], "little")
    refs = struct.unpack_from("<8H", m, 36)  # amp/dist ch1L, ch2L, ch1S, ch2S
    frame_width = int.from_bytes(m[52:54], "little")
    frame_height = int.from_bytes(m[54:56], "little")
    static = m[56]
    ambient_attenuation = m[57]
    dyn = int.from_bytes(m[58:60], "little")
    error_code = int.from_bytes(m[60:62], "little")
    error_status = m[62]
    frame_period_us = int.from_bytes(m[68:72], "little")

    dss_mode = (dyn >> 4) & 0x3
    binning = (dyn >> 6) & 0x1F
    nb_step = (dyn >> 12) & 0xF

    step1 = _u24le(m, 76)
    step4_5 = _u24le(m, 79)
    step6 = _u24le(m, 82)
    step7 = _u24le(m, 85)

    ranging_mode = {7: "precision", 6: "ambient"}.get(nb_step)
    exposure_ms = None
    exposure_consistent = None
    ratios = _TOF_EXPOSURE_RATIOS.get(nb_step)
    if ratios is not None:
        x1 = step1 / ratios[0]
        x6 = step6 / ratios[1]
        exposure_ms = (x1 + x6) / 2.0
        exposure_consistent = abs(x1 - x6) <= 0.02 * max(exposure_ms, 1e-6)

    fps = (1_000_000.0 / frame_period_us) if frame_period_us else None

    return {
        "frame_counter": frame_counter,
        "die_temp_c": die_temp_c,
        "error_status": error_status,
        "error_code": error_code,
        "ranging_mode": ranging_mode,
        "nb_step": nb_step,
        "dss_mode": dss_mode,
        "binning": binning,
        "power_mode": (static >> 2) & 0x3,
        "sync_mode": static & 0x3,
        "ambient_attenuation": ambient_attenuation,
        "frame_period_us": frame_period_us,
        "fps": fps,
        "exposure_ms": exposure_ms,
        "exposure_consistent": exposure_consistent,
        "nb_shot_step1": step1,
        "nb_shot_step4_5": step4_5,
        "nb_shot_step6": step6,
        "nb_shot_step7": step7,
        "ref_channels": list(refs),  # [amp1L, dist1L, amp2L, dist2L, amp1S, dist1S, amp2S, dist2S]
        "frame_width": frame_width,
        "frame_height": frame_height,
    }
