hellosamblack/lidar-roomscanner/host/src/roomscan/metrics.py

"""Live viewer metrics: per-sensor data rates, rendered FPS, system resources.

Pure/testable core (no Open3D imports) consumed by the control panel's HUD
overlay. See docs/superpowers/specs/completed/2026-07-10-viewer-metrics-hud-design.md.

Rate model (owner-confirmed 2026-07-10): every wire frame carries an on-device
microsecond timestamp ``t_us``. For each sensor stream we report two rates:

* **device_hz** (``->hub``) = ``1e6 / mean(delta t_us)`` — the cadence the MCU /
  sensor-hub *produced* samples at, independent of the link. ``None`` when a
  stream's ``t_us`` is absent/zero/non-monotonic (firmware not stamping it).
* **host_hz** (``->host``) = frames received / wall-clock window — the rate that
  actually reached the PC.

host < device reveals frames lost/decimated on the USB CDC link, per sensor.

Threading: ``RateMeter``/``MetricsRegistry`` are fed from the reader thread and
read from the UI thread; each guards its own state with a lock (mirrors
``SensorState``). ``ResourceSampler`` runs its own daemon thread and publishes a
latest-snapshot via an atomic reference swap.
"""
from __future__ import annotations

import threading
import time
from collections import deque
from dataclasses import dataclass

from .protocol import FrameHeader, FrameType, StreamId

WINDOW_S = 2.0                 # sliding window for rate/bandwidth estimates

# stream_id -> short HUD label. DEPTH_ZF32 (Phase-1 replay) and RAW_3DMD
# (raw-only live) are both the ToF depth source and never co-occur in practice.
SENSOR_LABELS: dict[int, str] = {
    StreamId.DEPTH_ZF32: "ToF",
    StreamId.RAW_3DMD: "ToF",
    StreamId.IMU_QUAT: "IMU",
    StreamId.IMU_RAW: "IMUraw",
    StreamId.ENV: "Env",
}
# fixed display order (ToF, IMU, IMU raw, Env); anything else sorts last
_SENSOR_ORDER: dict[int, int] = {
    StreamId.DEPTH_ZF32: 0,
    StreamId.RAW_3DMD: 0,
    StreamId.IMU_QUAT: 1,
    StreamId.IMU_RAW: 2,
    StreamId.ENV: 3,
}


class RateMeter:
    """Sliding-window rate/bandwidth tracker for one stream. Pure aside from a
    lock guarding the sample deque (reader writes, UI reads)."""

    def __init__(self, window_s: float = WINDOW_S):
        self.window_s = window_s
        self._lock = threading.Lock()
        self._samples: deque[tuple[float, int, int]] = deque()  # (arrival_s, t_us, nbytes)

    def record(self, t_us: int, arrival_s: float, nbytes: int) -> None:
        with self._lock:
            self._samples.append((arrival_s, int(t_us), int(nbytes)))
            self._trim(arrival_s)

    def _trim(self, now: float) -> None:
        s = self._samples
        while s and now - s[0][0] > self.window_s:
            s.popleft()

    def host_hz(self, now: float) -> float:
        with self._lock:
            self._trim(now)
            s = self._samples
            if len(s) < 2:
                return 0.0
            span = s[-1][0] - s[0][0]
            return (len(s) - 1) / span if span > 0 else 0.0

    def device_hz(self, now: float) -> float | None:
        with self._lock:
            self._trim(now)
            ts = [x[1] for x in self._samples]
        if len(ts) < 2:
            return None
        deltas = [b - a for a, b in zip(ts, ts[1:])]
        if any(d <= 0 for d in deltas):     # zero/flat or non-monotonic t_us
            return None
        mean_us = sum(deltas) / len(deltas)
        return 1e6 / mean_us if mean_us > 0 else None

    def bytes_per_s(self, now: float) -> float:
        with self._lock:
            self._trim(now)
            s = self._samples
            if len(s) < 2:
                return 0.0
            span = s[-1][0] - s[0][0]
            if span <= 0:
                return 0.0
            # bytes that arrived after the window-start reference frame
            total = sum(x[2] for x in list(s)[1:])
            return total / span

    def jitter_ms(self, now: float) -> float | None:
        with self._lock:
            self._trim(now)
            # A COPY, not the live deque: every other reader here (`host_hz`,
            # `device_hz`, `bytes_per_s`) does its whole `len`/index walk
            # INSIDE the lock, but this one walks `s` in a loop AFTER
            # releasing it. Against a real background reader thread calling
            # `record()` (which also calls `_trim`, popping the left end)
            # concurrently, `len(s)` read here can already be stale by the
            # time the loop below indexes into it, hitting a deque IndexError --
            # reproduced by a real reader thread + a concurrent `snapshot()`
            # poller (issue #101 test infrastructure, discovered incidentally
            # while adding a real-background-reader end-to-end test).
            s = list(self._samples)
        if len(s) < 2:
            return None
        j_sum = 0.0
        for i in range(1, len(s)):
            dh = s[i][0] - s[i-1][0]
            dd = (s[i][1] - s[i-1][1]) / 1e6
            if dd > 0:
                j_sum += abs(dh - dd)
        return (j_sum / (len(s) - 1)) * 1000.0


@dataclass(frozen=True)
class StreamRate:
    stream_id: int
    label: str
    device_hz: float | None
    host_hz: float
    bytes_per_s: float
    jitter_ms: float | None


@dataclass(frozen=True)
class ResourceSnapshot:
    """Resource usage of this process AND of the box it runs on.

    The per-process fields came first (``proc_*``): what our app consumes.
    ``proc_cpu_percent`` is summed across cores (100% == one full core); divide
    by 100 for core-equivalents. ``proc_vram`` is None where the platform can't
    attribute GPU memory per process (Windows WDDM) or where ``pynvml`` isn't
    installed -- which is the normal case here, since it lives in the optional
    ``monitor`` extra.

    The system/device-wide fields (``sys_cpu_percent``, ``ram_used``,
    ``device_vram_*``) were added 2026-07-31 for the Live SLAM resource
    monitor, because the owner's question is "am I about to hit a limit?" and a
    per-process number cannot answer it: the limit is shared with every other
    process on the box, and the VRAM ceiling in particular is the one BUG-032
    (mesh-extraction leak) and BUG-035 (TSDF block capacity) were about. VRAM
    comes from ``slam.gpumem.Nvml`` -- ctypes NVML, no dependency -- so it works
    in a venv with no ``pynvml``; every one of them degrades to None rather than
    raising on a box with no GPU.
    """
    proc_cpu_percent: float
    n_cores: int
    proc_rss: int                   # our process resident set size (bytes)
    ram_total: int                  # system RAM (the capacity the bar fills toward)
    gpu_util: float | None          # process or device SM utilization; see gpu_source
    proc_vram: int | None           # our process VRAM (bytes), None if unavailable
    vram_total: int | None
    gpu_name: str | None
    gpu_source: str                 # "pynvml" | "nvml-device" | "n/a" | test tag
    # System/device-wide (all None-able: no psutil sample yet, or no GPU).
    sys_cpu_percent: float | None = None    # whole-box CPU %, 0..100 across all cores
    ram_used: int | None = None             # system RAM in use (total - available)
    device_vram_used: int | None = None     # DEVICE-wide VRAM in use (all processes)
    device_vram_total: int | None = None
    device_vram_source: str = "n/a"         # "nvml" | "n/a" | test tag


@dataclass(frozen=True)
class MetricsSnapshot:
    render_fps: float
    streams: list[StreamRate]
    link_bytes_per_s: float
    resources: ResourceSnapshot | None
    drops: int = 0
    gaps: int = 0
    # Task 9 (2026-08-03, high-framerate decoupling): the rate at which
    # TRANSFORMED frames complete (`stage.feed` succeeding), fed from the
    # reader thread and NOT capped by the broadcaster's presentation cadence
    # (`render_fps`'s slot-pull tick is capped at ~POINT_INTERVAL, currently
    # 30 Hz). At a 30 Hz source the two agree; at 90 Hz they diverge, and the
    # gap IS the deliberate presentation decimation -- distinct from data
    # loss (compare against a stream's own `host_hz` in `streams`, which is
    # the pre-transform arrival rate) or SLAM loss (`frames_submitted`/
    # `frames_processed`/`frames_overwritten` in the `slam` message).
    transform_fps: float = 0.0
    # Literal browser-facing send rate: ticked only where the point-cloud
    # broadcast actually happens (`web._broadcaster`'s `point_cloud` display
    # branch), so it does not over-count the way `render_fps` does in
    # `slam`/`detailed` display (see `tick_browser`'s docstring). 0.0 from a
    # MetricsRegistry never fed one (e.g. the desktop panel, which has no
    # browser to send to), same null-safe default as `drops`/`gaps`.
    browser_fps: float = 0.0


class MetricsRegistry:
    """One RateMeter per stream_id seen + a rendered-frame counter. Fed from the
    reader thread (``record``/``tick_render``); the UI thread reads ``snapshot``.

    Optional ``sampler`` is a ResourceSampler whose latest snapshot is folded into
    ``MetricsSnapshot.resources`` (None if absent)."""

    def __init__(self, window_s: float = WINDOW_S, sampler: "ResourceSampler | None" = None):
        self.window_s = window_s
        self.sampler = sampler
        self._lock = threading.Lock()
        self._meters: dict[int, RateMeter] = {}
        self._render_ticks: deque[float] = deque()
        self._transform_ticks: deque[float] = deque()
        self._browser_ticks: deque[float] = deque()

    def reset_source(self) -> None:
        """Drop every per-stream rate meter and every render/transform/browser
        tick history -- everything here is derived from the frames of the
        source just left (issue #101 step 2: a Live<->View swap must not let
        the OLD source's rates/jitter bleed into the new one's HUD rows).

        `sampler` (host process/system CPU, RAM, GPU) is deliberately left
        alone: it measures THIS PROCESS, not the active source, so it must
        keep running across a source switch -- the same "preserve genuinely
        host-wide state" rule `SensorState.reset_source` follows for its own
        fields."""
        with self._lock:
            self._meters.clear()
            self._render_ticks.clear()
            self._transform_ticks.clear()
            self._browser_ticks.clear()

    def record(self, header: FrameHeader, nbytes: int, now: float) -> None:
        """Record one decoded DATA frame. Non-DATA frames are ignored (their
        stream_id field is meaningless and would pollute the ToF meter)."""
        if header.frame_type != FrameType.DATA:
            return
        sid = header.stream_id
        with self._lock:
            m = self._meters.get(sid)
            if m is None:
                m = RateMeter(self.window_s)
                self._meters[sid] = m
        m.record(header.t_us, now, nbytes)

    def tick_render(self, now: float) -> None:
        with self._lock:
            self._render_ticks.append(now)
            while self._render_ticks and now - self._render_ticks[0] > self.window_s:
                self._render_ticks.popleft()

    def render_fps(self, now: float) -> float:
        with self._lock:
            ticks = self._render_ticks
            if len(ticks) < 2:
                return 0.0
            span = ticks[-1] - ticks[0]
            return (len(ticks) - 1) / span if span > 0 else 0.0

    def tick_transform(self, now: float) -> None:
        """One TRANSFORMED frame completed (Task 9). Fed from the reader
        thread, right where `stats.update(header)` runs -- i.e. on every
        frame that survives `TransformStage.feed`, before it is ever paced
        or handed to a display/SLAM consumer. Unlike `tick_render` (which
        only ticks when the broadcaster's ~30 Hz loop happens to pull a fresh
        slot item), this free-runs at the transform's own rate, so it is the
        number to compare against a source's raw arrival rate (a stream's
        `host_hz`) to see transform-stage loss, and against `render_fps` to
        see presentation decimation."""
        with self._lock:
            self._transform_ticks.append(now)
            while self._transform_ticks and now - self._transform_ticks[0] > self.window_s:
                self._transform_ticks.popleft()

    def transform_fps(self, now: float) -> float:
        with self._lock:
            ticks = self._transform_ticks
            if len(ticks) < 2:
                return 0.0
            span = ticks[-1] - ticks[0]
            return (len(ticks) - 1) / span if span > 0 else 0.0

    def tick_browser(self, now: float) -> None:
        """One POINT_CLOUD payload actually handed to `_broadcast_bytes`
        (Task 9). Unlike `tick_render` -- which ticks on every fresh slot
        pull regardless of display mode, so it over-counts in `slam`/
        `detailed` display where no point cloud goes to the browser at all
        -- this ticks only at the real send site, so it is the literal
        answer to "how many point clouds did the browser get", never
        conflated with SLAM's own mesh cadence."""
        with self._lock:
            self._browser_ticks.append(now)
            while self._browser_ticks and now - self._browser_ticks[0] > self.window_s:
                self._browser_ticks.popleft()

    def browser_fps(self, now: float) -> float:
        with self._lock:
            ticks = self._browser_ticks
            if len(ticks) < 2:
                return 0.0
            span = ticks[-1] - ticks[0]
            return (len(ticks) - 1) / span if span > 0 else 0.0

    def snapshot(self, now: float) -> MetricsSnapshot:
        with self._lock:
            meters = list(self._meters.items())
        streams: list[StreamRate] = []
        link_bps = 0.0
        for sid, m in meters:
            bps = m.bytes_per_s(now)
            link_bps += bps
            label = SENSOR_LABELS.get(sid)
            if label is not None:
                streams.append(StreamRate(sid, label, m.device_hz(now), m.host_hz(now), bps, m.jitter_ms(now)))
        streams.sort(key=lambda s: _SENSOR_ORDER.get(s.stream_id, 99))
        resources = self.sampler.latest() if self.sampler is not None else None
        return MetricsSnapshot(self.render_fps(now), streams, link_bps, resources,
                               transform_fps=self.transform_fps(now),
                               browser_fps=self.browser_fps(now))


# --- text formatting (pure) --------------------------------------------------

def fmt_hz(hz: float | None) -> str:
    """Rate for the HUD: ``-`` when unknown (device rate with no usable t_us),
    else adaptive precision (finer under 10 Hz)."""
    if hz is None:
        return "-"
    return f"{hz:.1f}" if hz < 10 else f"{hz:.0f}"


def fmt_rate(n_bytes_per_s: float) -> str:
    """Bytes/second -> compact B/s, KB/s, MB/s (1024-based)."""
    x = float(n_bytes_per_s)
    for unit in ("B", "KB", "MB", "GB"):
        if x < 1024 or unit == "GB":
            return f"{x:.0f} {unit}/s" if unit == "B" else f"{x:.1f} {unit}/s"
        x /= 1024
    return f"{x:.1f} GB/s"


def fmt_bytes(n: int | None) -> str:
    """Absolute byte count -> GB/MB for RAM/VRAM readouts. ``?`` when unknown."""
    if n is None:
        return "?"
    x = float(n)
    for unit in ("B", "KB", "MB", "GB", "TB"):
        if x < 1024 or unit == "TB":
            return f"{x:.1f} {unit}"
        x /= 1024
    return f"{x:.1f} TB"


# --- GPU probing (per-process, NVML only) ------------------------------------
# nvidia-smi can't report per-process GPU utilization, so the per-project GPU
# readout needs NVML (optional `monitor` extra). Without it, GPU shows n/a.

def _nvml_recent_us() -> int:
    """Timestamp (us) ~2 s ago: the lower bound for nvmlDeviceGetProcessUtilization
    so it returns only recent SM-utilization samples."""
    return int(time.time() * 1e6) - 2_000_000


def _probe_gpu_pynvml(pid: int):
    import pynvml as N   # optional dep; ImportError -> caught by probe_gpu_process
    N.nvmlInit()
    try:
        h = N.nvmlDeviceGetHandleByIndex(0)
        name = N.nvmlDeviceGetName(h)
        if isinstance(name, bytes):
            name = name.decode("ascii", "replace")
        vram_total = int(N.nvmlDeviceGetMemoryInfo(h).total)
        proc_vram = None                      # WDDM (Windows) reports None per process
        try:
            running = (list(N.nvmlDeviceGetGraphicsRunningProcesses(h))
                       + list(N.nvmlDeviceGetComputeRunningProcesses(h)))
            for p in running:
                if p.pid == pid and getattr(p, "usedGpuMemory", None):
                    proc_vram = int(p.usedGpuMemory)
        except N.NVMLError:
            pass
        util = 0.0                            # NVML up but our pid idle -> 0, not n/a
        try:
            for s in N.nvmlDeviceGetProcessUtilization(h, _nvml_recent_us()):
                if s.pid == pid:
                    util = float(s.smUtil)
        except N.NVMLError:
            util = 0.0                        # no recent samples == no GPU activity
        return util, proc_vram, vram_total, name, "pynvml"
    finally:
        try:
            N.nvmlShutdown()
        except Exception:
            pass


def probe_gpu_process(pid: int, probes=None):
    """Per-process GPU sample ``(util%, proc_vram, vram_total, name, source)``.
    Tries each probe; first that returns wins; all failures -> the n/a tuple.
    ``probes`` is injectable for tests (each called with ``pid``)."""
    for fn in (probes if probes is not None else [_probe_gpu_pynvml]):
        try:
            return fn(pid)
        except Exception:
            continue
    return None, None, None, None, "n/a"


def probe_device_vram():
    """DEVICE-wide VRAM ``(used, total, name, source)`` -- bytes, bytes, str,
    str -- or ``(None, None, None, "n/a")``.

    Uses ``roomscan.slam.gpumem.Nvml``: a ctypes binding to libnvidia-ml, so it
    needs no ``pynvml`` (which is not installed here -- it is in the optional
    ``monitor`` extra, which is why ``probe_gpu_process`` reports "n/a" and
    every per-process GPU field is null on this box). Device-wide rather than
    per-process is also the RIGHT number for the headroom question: the card is
    shared, and what kills a scan is the device running out, not our share of
    it (BUG-032, BUG-035).

    Never raises: no driver library, no GPU, or an NVML error all give "n/a".

    **It will not match `nvidia-smi --query-gpu=memory.used` — that is expected.**
    Measured on this box 2026-07-31: NVML said 370.94 MiB while `nvidia-smi`
    said 18 MiB used and 354 MiB *reserved*, i.e. 18 + 354 = 372 ~ 371. The v1
    `nvmlDeviceGetMemoryInfo` counts the driver's reserved allocation and
    `memory.used` does not. Totals agree exactly (8188 MiB). Including reserved
    is the right choice for a headroom gauge: reserved memory is not available
    to a new allocation either.
    """
    try:
        from .slam.gpumem import Nvml
    except Exception:
        return None, None, None, "n/a"
    try:
        nvml = Nvml()
    except Exception:
        return None, None, None, "n/a"
    try:
        if not nvml.ok:
            return None, None, None, "n/a"
        used, total = nvml.used_bytes(), nvml.total_bytes()
        if total <= 0:
            return None, None, None, "n/a"
        return int(used), int(total), nvml.name(), "nvml"
    except Exception:
        return None, None, None, "n/a"
    finally:
        try:
            nvml.close()
        except Exception:
            pass


class ResourceSampler:
    """Background daemon sampling CPU/RAM/GPU at ``interval`` seconds, publishing
    the latest ResourceSnapshot for lockless reads. Off the render loop so a slow
    probe never stalls it.

    Samples both scopes: this process (``proc_*``, psutil + per-process NVML) and
    the whole box (``sys_cpu_percent`` / ``ram_used`` / ``device_vram_*``).
    ``device_util_probe`` optionally supplies the device-wide utilization
    fallback when the per-process probe has none. Every probe runs on this
    thread -- a consumer of :meth:`latest` must never perform hardware I/O.
    All probes are injectable so tests need no GPU; ``pid`` defaults to the
    current process.
    """

    def __init__(self, interval: float = 0.7, gpu_probe=None, pid: int | None = None,
                 vram_probe=None, device_util_probe=None):
        import os
        self.interval = interval
        self._pid = pid if pid is not None else os.getpid()
        self._gpu_probe = gpu_probe if gpu_probe is not None else (lambda: probe_gpu_process(self._pid))
        self._vram_probe = vram_probe if vram_probe is not None else probe_device_vram
        self._device_util_probe = device_util_probe
        self._latest: ResourceSnapshot | None = None
        self._stop = threading.Event()
        self._thread: threading.Thread | None = None

    def start(self) -> None:
        if self._thread is not None:
            return
        self._stop.clear()
        self._thread = threading.Thread(target=self._run, name="resource-sampler", daemon=True)
        self._thread.start()

    def stop(self) -> None:
        self._stop.set()
        t = self._thread
        if t is not None:
            t.join(timeout=2.0)
            self._thread = None

    def is_running(self) -> bool:
        return self._thread is not None and self._thread.is_alive()

    def latest(self) -> ResourceSnapshot | None:
        return self._latest       # atomic reference read; no lock needed

    def _run(self) -> None:
        import psutil
        proc = psutil.Process(self._pid)
        proc.cpu_percent(None)              # prime (first call is a 0.0 baseline)
        psutil.cpu_percent(None)            # ditto for the system-wide meter
        n_cores = psutil.cpu_count() or 1
        while not self._stop.wait(self.interval):
            try:
                cpu = proc.cpu_percent(None)
                rss = int(proc.memory_info().rss)
            except psutil.Error:
                continue                    # process vanished mid-sample; try again
            vm = psutil.virtual_memory()
            ram_total = int(vm.total)
            # `available` (not `total - used`) is what a new allocation can
            # actually get: cache/buffers are reclaimable, so `used` alone
            # would report a Linux box as near-full at idle.
            ram_used = max(0, ram_total - int(getattr(vm, "available", 0)))
            try:
                sys_cpu = float(psutil.cpu_percent(None))
            except psutil.Error:
                sys_cpu = None
            gpu_util, proc_vram, vram_total, gpu_name, src = self._gpu_probe()
            if gpu_util is None and self._device_util_probe is not None:
                try:
                    dev_util = self._device_util_probe()
                    fallback_util = (None if dev_util is None
                                     else float(dev_util["gpu_pct"]))
                except Exception:
                    fallback_util = None
                if fallback_util is not None:
                    gpu_util = fallback_util
                    src = "nvml-device"
            dev_used, dev_total, dev_name, dev_src = self._vram_probe()
            self._latest = ResourceSnapshot(
                proc_cpu_percent=float(cpu),
                n_cores=int(n_cores),
                proc_rss=rss,
                ram_total=ram_total,
                gpu_util=gpu_util,
                proc_vram=proc_vram,
                vram_total=vram_total,
                # Prefer the per-process probe's name (it knows which device
                # our pid is on); fall back to the ctypes device-wide one,
                # which is the only source present without pynvml.
                gpu_name=gpu_name or dev_name,
                gpu_source=src,
                sys_cpu_percent=sys_cpu,
                ram_used=ram_used,
                device_vram_used=dev_used,
                device_vram_total=dev_total,
                device_vram_source=dev_src,
            )
