hellosamblack/lidar-roomscanner/host/src/roomscan/magsweep.py

"""Magnetometer sweep coverage + calibration-quality diagnostics.

Backs the web app's "Calibrate Mag" modal (owner ask, 2026-07-29). The fit
itself is `magcal.fit_ellipsoid` reused verbatim; everything here is the
*diagnostic* layer around it -- the part that was missing and that let a bad
calibration ship silently.

Why this exists
---------------
A correctly calibrated magnetometer reports a CONSTANT field magnitude in every
orientation. On 2026-07-29 the shipped `mag_cal.json` was measured across a tilt
sweep and did not:

    tilt from vertical:  0.3   0.2   30.5  60.6  80.0  90.6  30.6  2.8   (deg)
    |B| after cal:       50.5  47.4  58.7  76.5  81.1  85.1  62.8  50.7  (uT)

Accurate ceiling-facing, degrading monotonically to ~1.7x toward horizontal --
the signature of an incomplete tumble: good coverage in ONE attitude family,
poor everywhere else. The ellipsoid fit is happy to interpolate a plausible
ellipsoid through a cap of samples; nothing downstream noticed. Hence: measure
the coverage during collection, and measure the |B| consistency of the result
before anyone accepts it.

Binning: a Fibonacci (golden-spiral) sphere lattice
---------------------------------------------------
Cells are the Voronoi cells of an N-point Fibonacci lattice, and a sample is
assigned to the cell whose lattice direction it is closest to (a single argmax
over dot products -- no wrap/branch logic, no boundary special cases).

Chosen over naive lat/lon bins because those are wildly UNequal in area (a
15-degree lat/lon bin at the pole is ~1/50 the area of one at the equator), so a
lat/lon coverage percentage would over-weight the poles and report "covered"
for a tumble that missed most of the actual sphere -- precisely the failure mode
this tool exists to catch. The Fibonacci lattice is the standard cheap
quasi-uniform sphere point set: every cell has near-identical area, so
"fraction of cells occupied" IS "fraction of the sphere covered", and a gap of
K cells means the same thing wherever it sits.

`SPHERE_CELLS = 92` gives ~0.137 sr per cell, i.e. a cell radius of ~12 deg
(diameter ~24 deg) -- coarse enough that a careful hand tumble can fill every
cell, fine enough that the measured defect above (a whole hemisphere-ish family
of attitudes missing) is many cells wide, not one.

What gets binned
----------------
The **calibrated, body-frame** field direction -- `unit(AXIS_CONVENTION @
cal.apply(raw))` -- NOT the raw direction. This matters and is not a detail:
the rig's hard-iron offset is ~65 uT against a ~50 uT field, so the raw vectors
all live in a cone around the offset and their directions cover barely half the
sphere no matter how thoroughly you tumble. Binned raw, coverage could never
reach 100% and the map would be meaningless. Binned calibrated, a cell IS "the
device was oriented such that the field entered it from this direction", which
is both what the user can act on and what the ellipsoid fit needs to span (full
body-frame direction coverage <=> the raw cloud wraps the whole ellipsoid).

With no calibration available at all (fresh install), `provisional_calibration`
derives a cheap hard-iron-only estimate from the sample bounding box so the map
still works on the very first tumble; it is used ONLY for binning/display and
is never saved.
"""
from __future__ import annotations

import math
import time
from collections import deque

import numpy as np

from .magcal import MagCalibration, fit_ellipsoid
from .sensors import AXIS_CONVENTION, T_WORLD_TO_CV

# Cell count of the Fibonacci sphere lattice -- see the module docstring for
# why 92 (cell radius ~12 deg, fillable by hand, gap-legible).
SPHERE_CELLS = 92

# Cap on retained raw samples (~11 min at the 30 Hz env-stream rate). Beyond
# this the oldest are dropped: an ellipsoid fit saturates long before, and the
# whole-array recompute in `build_report` stays a few ms.
MAX_SAMPLES = 20000

# --- quality thresholds (documented in docs/web-protocol.md) -----------------
#
# Field consistency is the HEADLINE metric: std(|B|)/mean(|B|) after applying
# the candidate calibration. The 2% "good" bar matches the existing convention
# in docs/yaw-fusion.md ("< 0.02 is a clean fit"); the defective calibration
# above scores ~20%.
FIELD_GOOD_PCT = 2.0
FIELD_MARGINAL_PCT = 5.0
# Fraction of sphere cells that must hold >=1 sample.
COVERAGE_GOOD = 0.85
COVERAGE_MARGINAL = 0.60
# Raw sample count. `fit_ellipsoid` needs 20 to be solvable at all; 300 is
# ~10 s of tumbling and the point where the 9-parameter fit stops being
# noise-dominated.
SAMPLES_GOOD = 300
SAMPLES_MARGINAL = 100
MIN_FIT_SAMPLES = 20

_VERDICT_RANK = {"good": 0, "marginal": 1, "bad": 2}

# --- guidance / live-fit / motion tuning (3D feedback, 2026-07-29) -----------
#
# Steer at the largest connected empty region rather than the nearest stray
# cell -- chasing a singleton is busywork. Below this size the region structure
# has stopped meaning anything and the nearest empty cell is the better target
# (a nearly-finished sphere with scattered misses).
MIN_GUIDANCE_REGION = 3

# Below this rotation the "from face -> to face" half of the guidance sentence is
# dropped: two directions a few degrees apart can straddle a face boundary and
# name two opposite faces for a nudge, which reads as a much bigger instruction
# than it is.
FACE_HINT_MIN_DEG = 25.0

# The rolling provisional fit refits the WHOLE cloud on every report tick, so it
# is capped: measured on this box `fit_ellipsoid` costs 0.29 ms at 1200 samples
# and 3.18 ms at 20 000, and the report runs at 5 Hz. Above the cap the cloud is
# decimated (evenly, not truncated -- truncating would drop the newest samples'
# coverage, which is exactly what the user is watching).
LIVE_FIT_MAX_SAMPLES = 4000

# "The device isn't turning" detection, off the field DIRECTION rather than a
# gyro: a device whose calibrated field direction has not moved is a device that
# cannot be filling new cells, which is the only thing this view cares about.
# Window and threshold are deliberately generous -- the point is to catch "the
# board is sitting on the desk", not to measure motion.
STATIONARY_WINDOW_S = 2.0
STATIONARY_MIN_SAMPLES = 8
STATIONARY_SPREAD_DEG = 4.0

# Body-frame faces (SFLP body: X = Up, Y = Right, Z = Forward/boresight -- see
# docs/coordinate-frames.md). Used to name WHERE a coverage gap is, so the
# guidance is an instruction ("aim the Right face at the field") rather than a
# vector the user has to decode.
FACES = (
    ("Top", (1.0, 0.0, 0.0)),
    ("Bottom", (-1.0, 0.0, 0.0)),
    ("Right", (0.0, 1.0, 0.0)),
    ("Left", (0.0, -1.0, 0.0)),
    ("Front", (0.0, 0.0, 1.0)),
    ("Back", (0.0, 0.0, -1.0)),
)


# --- sphere lattice ---------------------------------------------------------

_LATTICE_CACHE: dict[int, np.ndarray] = {}
_NEIGHBOUR_CACHE: dict[tuple[int, int], list[tuple[int, ...]]] = {}


def sphere_lattice(n: int = SPHERE_CELLS) -> np.ndarray:
    """(n, 3) unit vectors on a Fibonacci (golden-spiral) sphere lattice --
    the cell centres. Deterministic and cached; callers must not mutate the
    returned array (it is returned read-only)."""
    cached = _LATTICE_CACHE.get(n)
    if cached is not None:
        return cached
    if n < 4:
        raise ValueError(f"need at least 4 cells, got {n}")
    i = np.arange(n, dtype=np.float64) + 0.5
    z = 1.0 - 2.0 * i / n
    r = np.sqrt(np.maximum(0.0, 1.0 - z * z))
    phi = math.pi * (1.0 + math.sqrt(5.0)) * i
    pts = np.column_stack([r * np.cos(phi), r * np.sin(phi), z])
    pts /= np.linalg.norm(pts, axis=1, keepdims=True)
    pts.setflags(write=False)
    _LATTICE_CACHE[n] = pts
    return pts


def cell_neighbours(n: int = SPHERE_CELLS, k: int = 6) -> list[tuple[int, ...]]:
    """Symmetrized k-nearest-neighbour adjacency of the lattice cells, used to
    grow connected empty regions. k=6 because a Fibonacci lattice is locally
    hexagonal; symmetrizing (union of both directions) keeps the graph
    undirected where the k-NN relation isn't mutual."""
    key = (n, k)
    cached = _NEIGHBOUR_CACHE.get(key)
    if cached is not None:
        return cached
    lat = sphere_lattice(n)
    dots = lat @ lat.T
    np.fill_diagonal(dots, -2.0)
    nearest = np.argsort(-dots, axis=1)[:, :k]
    sets: list[set[int]] = [set(row.tolist()) for row in nearest]
    for a, row in enumerate(nearest):
        for b in row.tolist():
            sets[b].add(a)
    adj = [tuple(sorted(s)) for s in sets]
    _NEIGHBOUR_CACHE[key] = adj
    return adj


def unit(vec) -> np.ndarray | None:
    """Normalize a 3-vector, or None if it is degenerately short."""
    v = np.asarray(vec, dtype=np.float64).reshape(3)
    n = float(np.linalg.norm(v))
    if not np.isfinite(n) or n < 1e-9:
        return None
    return v / n


def assign_cells(directions, n: int = SPHERE_CELLS) -> np.ndarray:
    """(M, 3) unit directions -> (M,) cell index (nearest lattice point).
    An empty input yields an empty int array."""
    d = np.asarray(directions, dtype=np.float64).reshape(-1, 3)
    if d.shape[0] == 0:
        return np.zeros(0, dtype=np.int64)
    return np.argmax(d @ sphere_lattice(n).T, axis=1)


# --- calibration helpers ----------------------------------------------------

def provisional_calibration(samples) -> MagCalibration | None:
    """Cheap hard-iron-only estimate: centre = per-axis midpoint of the sample
    bounding box, soft-iron = identity, field = mean radius. Used ONLY to bin
    directions for the coverage map when no real calibration exists yet (first
    ever tumble) -- never fitted, never saved, never fed to the yaw fusion. Its
    directions are good enough for 24-deg-wide cells long before the sample
    cloud is good enough for `fit_ellipsoid`.

    None when there is too little spread to centre anything meaningfully."""
    x = np.asarray(samples, dtype=np.float64).reshape(-1, 3)
    if x.shape[0] < 4:
        return None
    centre = (x.max(axis=0) + x.min(axis=0)) / 2.0
    radii = np.linalg.norm(x - centre, axis=1)
    field = float(np.mean(radii))
    if not np.isfinite(field) or field < 1e-6:
        return None
    return MagCalibration(
        offset=tuple(float(v) for v in centre),
        matrix=((1.0, 0.0, 0.0), (0.0, 1.0, 0.0), (0.0, 0.0, 1.0)),
        field_ut=field,
    )


def calibrated_directions(samples, cal: MagCalibration | None) -> np.ndarray:
    """(N, 3) raw uT -> (N, 3) unit body-frame field directions under `cal`.

    `AXIS_CONVENTION` is applied so the directions are in the SFLP body frame
    (X=Up, Y=Right, Z=Forward), matching how the rest of the host consumes the
    mag (`web._mag_validity`, `build_sensor_message`, `YawFusion.update`) --
    the face names in `FACES` are only meaningful in that frame. With
    `cal=None` the raw vectors are used unchanged; see the module docstring for
    why that is a poor basis for binning and only a last resort."""
    x = np.asarray(samples, dtype=np.float64).reshape(-1, 3)
    if x.shape[0] == 0:
        return np.zeros((0, 3), dtype=np.float64)
    if cal is not None:
        m = np.asarray(cal.matrix, dtype=np.float64)
        b = np.asarray(cal.offset, dtype=np.float64)
        x = (x - b) @ m.T
    x = x @ np.asarray(AXIS_CONVENTION, dtype=np.float64).T
    norms = np.linalg.norm(x, axis=1, keepdims=True)
    norms[norms < 1e-9] = 1.0
    return x / norms


def calibrated_norms(samples, cal: MagCalibration) -> np.ndarray:
    """(N,) |B| in uT after applying `cal`. AXIS_CONVENTION is a signed
    permutation, so it cannot change a magnitude -- omitted deliberately."""
    x = np.asarray(samples, dtype=np.float64).reshape(-1, 3)
    if x.shape[0] == 0:
        return np.zeros(0, dtype=np.float64)
    m = np.asarray(cal.matrix, dtype=np.float64)
    b = np.asarray(cal.offset, dtype=np.float64)
    return np.linalg.norm((x - b) @ m.T, axis=1)


# --- metrics ----------------------------------------------------------------

def _verdict(value: float, good: float, marginal: float, higher_is_better: bool) -> str:
    if higher_is_better:
        if value >= good:
            return "good"
        return "marginal" if value >= marginal else "bad"
    if value < good:
        return "good"
    return "marginal" if value < marginal else "bad"


def field_consistency(samples, cal: MagCalibration | None) -> dict | None:
    """THE headline metric: |B| across every sample after applying `cal`.

    A correctly calibrated magnetometer reads the same field magnitude in every
    orientation, so `std_pct` (= std/mean, as a percent) is a direct, physical,
    assumption-free measure of calibration error -- it needs no ground truth,
    no reference heading, and no second instrument. `ratio` (max/min) is
    reported alongside because that is the number the 2026-07-29 tilt sweep
    exposed (~1.7x) and it is more legible than a std to a human eye.

    None when there are no samples or no calibration to apply."""
    x = np.asarray(samples, dtype=np.float64).reshape(-1, 3)
    if x.shape[0] == 0 or cal is None:
        return None
    norms = calibrated_norms(x, cal)
    mean = float(np.mean(norms))
    if not np.isfinite(mean) or mean < 1e-9:
        return None
    std = float(np.std(norms))
    lo, hi = float(np.min(norms)), float(np.max(norms))
    expected = float(cal.field_ut)
    std_pct = 100.0 * std / mean
    # Spread alone is not sufficient. A calibration can be perfectly SELF-
    # consistent (tiny std) while sitting at completely the wrong magnitude --
    # observed on-rig 2026-07-29: 255 stationary samples read |B| = 101.96 uT
    # against the saved calibration's own field_ut of 49.87 uT, a x2.04 bias,
    # yet scored std_pct = 0.22%. `bias_pct` is that second failure mode, and
    # the field verdict is the WORSE of the two so neither can hide the other.
    bias_pct = (100.0 * (mean - expected) / expected) if expected > 1e-9 else float("inf")
    spread_verdict = _verdict(std_pct, FIELD_GOOD_PCT, FIELD_MARGINAL_PCT, higher_is_better=False)
    bias_verdict = _verdict(abs(bias_pct), FIELD_GOOD_PCT, FIELD_MARGINAL_PCT, higher_is_better=False)
    return {
        "mean_ut": mean,
        "std_ut": std,
        "std_pct": std_pct,
        "bias_pct": bias_pct,
        "min_ut": lo,
        "max_ut": hi,
        "ratio": (hi / lo) if lo > 1e-9 else float("inf"),
        # RMS deviation of the calibrated samples from the sphere the fit
        # claims they lie on -- the fit residual, in physical uT. Combines both
        # failure modes above: sqrt(std^2 + bias^2).
        "residual_rms_ut": float(np.sqrt(np.mean((norms - expected) ** 2))),
        "expected_ut": expected,
        "spread_verdict": spread_verdict,
        "bias_verdict": bias_verdict,
        "verdict": max((spread_verdict, bias_verdict), key=lambda v: _VERDICT_RANK[v]),
    }


def attitude_locked_error(samples, t_s, cal: MagCalibration | None,
                          window_s: float = 5.0, n: int = SPHERE_CELLS,
                          min_cell: int = 15) -> dict | None:
    """Split |B| error into the part a calibration CAN fix and the part it cannot.

    `field_consistency` assumes every sample was taken in one place. That holds
    for a tumble and fails for a room scan: as the operator walks, the
    building's own ferrous mass moves the ambient field under them, so both the
    spread and the bias grow for reasons no calibration can touch. Measured on
    the 2026-07-30 sweep, **85% of the |B| variance was that slow spatial
    drift** -- and `field_consistency` scored the (good) calibration "bad"
    because the room's field level differed from the spot the tumble happened
    in. Read this function's verdict, not that one, on a moving capture.

    Method: detrend |B| with a short rolling median to remove the slow level,
    then measure how much of the residual is a function of body-frame
    ATTITUDE. Residual hard/soft iron is attitude-locked -- it repeats every
    time the device returns to the same pose -- while the room's contribution
    does not, so the between-cell spread of the detrended residual isolates the
    calibration's own error. On the 2026-07-30 fit that is 0.28 uT (0.55%);
    the superseded 2026-07-15 fit scores 3.4 uT (3.8%) on the same data.

    `window_s` must be long enough to span several attitudes (so real
    calibration error is not absorbed into the trend) and short enough to track
    the walk. None when there is nothing to measure.

    **This is a LOWER bound on calibration error, not a bound.** Wherever the
    operator holds one attitude family for longer than `window_s`, the trend
    absorbs that family's error along with the room's -- the superseded fit
    scores 3.4 uT at a 5 s window and 9.0 uT at 10 s on the same data for
    exactly that reason. So a "good" here is only trustworthy alongside a flat
    |B|-vs-tilt table (`tools/mag_check.py`), which is detrend-free and cannot
    hide a monotonic attitude ramp.
    """
    x = np.asarray(samples, dtype=np.float64).reshape(-1, 3)
    t = np.asarray(t_s, dtype=np.float64).reshape(-1)
    if cal is None or x.shape[0] < MIN_FIT_SAMPLES or t.shape[0] != x.shape[0]:
        return None
    span = float(t[-1] - t[0])
    if not np.isfinite(span) or span <= 0:
        return None
    norms = calibrated_norms(x, cal)
    mean = float(np.mean(norms))
    if not np.isfinite(mean) or mean < 1e-9:
        return None

    rate = x.shape[0] / span
    half = max(1, int(round(window_s * rate / 2.0)))
    padded = np.pad(norms, half, mode="edge")
    windows = np.lib.stride_tricks.sliding_window_view(padded, 2 * half + 1)
    trend = np.median(windows, axis=1)
    resid = norms - trend

    cells = assign_cells(calibrated_directions(x, cal), n)
    keep = [c for c in np.unique(cells) if int((cells == c).sum()) >= min_cell]
    if len(keep) < 2:
        # One attitude family only: there is no attitude dependence to measure,
        # which is NOT the same as measuring none. Say so rather than return 0.
        return {"window_s": window_s, "cells_used": len(keep), "attitude_locked_ut": None,
                "attitude_locked_pct": None, "mean_ut": mean,
                "total_std_ut": float(np.std(norms)), "spatial_std_ut": float(np.std(trend)),
                "residual_std_ut": float(np.std(resid)), "verdict": "unknown",
                "reason": f"only {len(keep)} attitude cells hold >={min_cell} samples"}
    cell_means = np.array([resid[cells == c].mean() for c in keep])
    cell_n = np.array([int((cells == c).sum()) for c in keep], dtype=np.float64)
    grand = float(np.average(cell_means, weights=cell_n))
    att = float(np.sqrt(np.average((cell_means - grand) ** 2, weights=cell_n)))
    att_pct = 100.0 * att / mean
    return {
        "window_s": window_s,
        "cells_used": len(keep),
        "mean_ut": mean,
        "total_std_ut": float(np.std(norms)),
        # The building's field as the operator walks -- irreducible by calibration.
        "spatial_std_ut": float(np.std(trend)),
        "residual_std_ut": float(np.std(resid)),
        # The calibration's own error.
        "attitude_locked_ut": att,
        "attitude_locked_pct": att_pct,
        "verdict": _verdict(att_pct, FIELD_GOOD_PCT, FIELD_MARGINAL_PCT, higher_is_better=False),
    }
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
